MKme/ResQ/Aircraft Files  and Design Ref/Flight Controller Reference/f405-wing_3.jpg

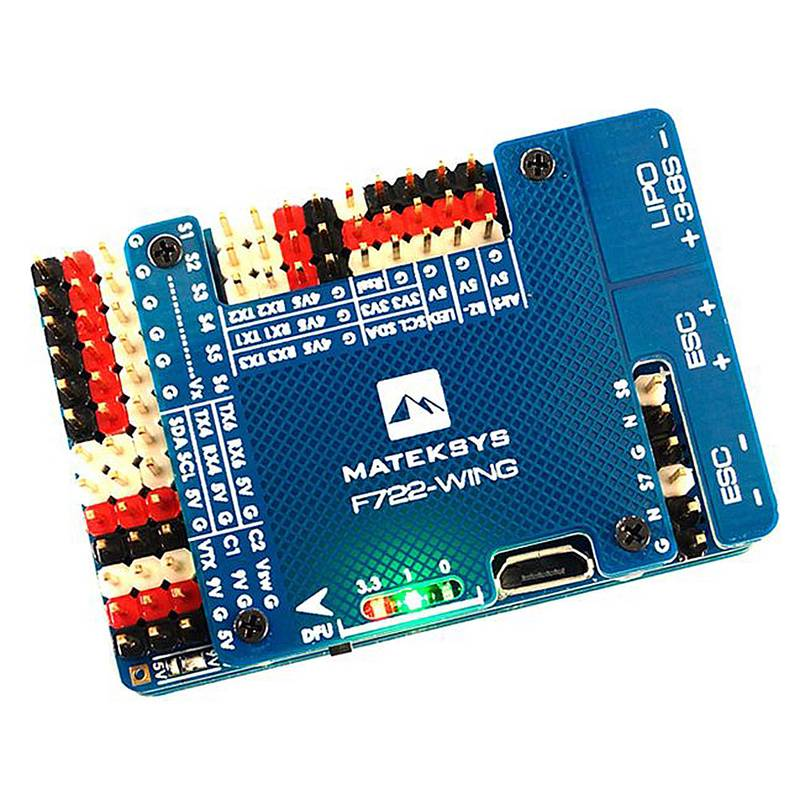
Aircraft Files and Design Ref/Flight Controller Reference/f405-wing_3.jpg
