MKme/ResQ/Code/Camera Module ESP32 Code/FTDI Connections for programming .PNG

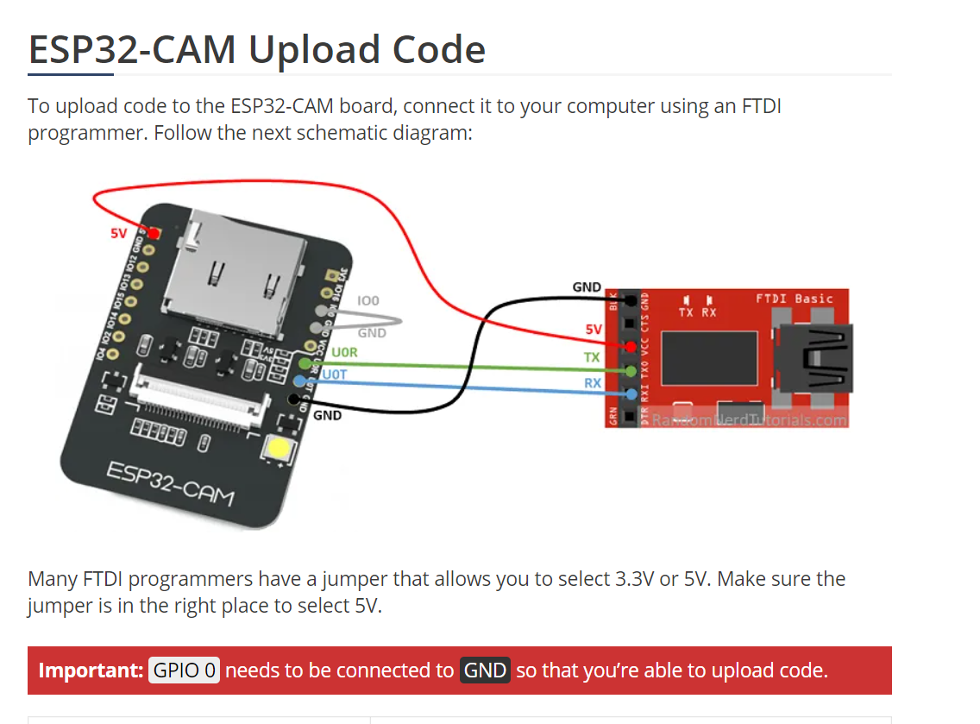
Code/Camera Module ESP32 Code/FTDI Connections for programming .PNG
