MKme/ResQ/Code/Camera Module ESP32 Code/Use the3se settings in Arduino IDE to program the board.png

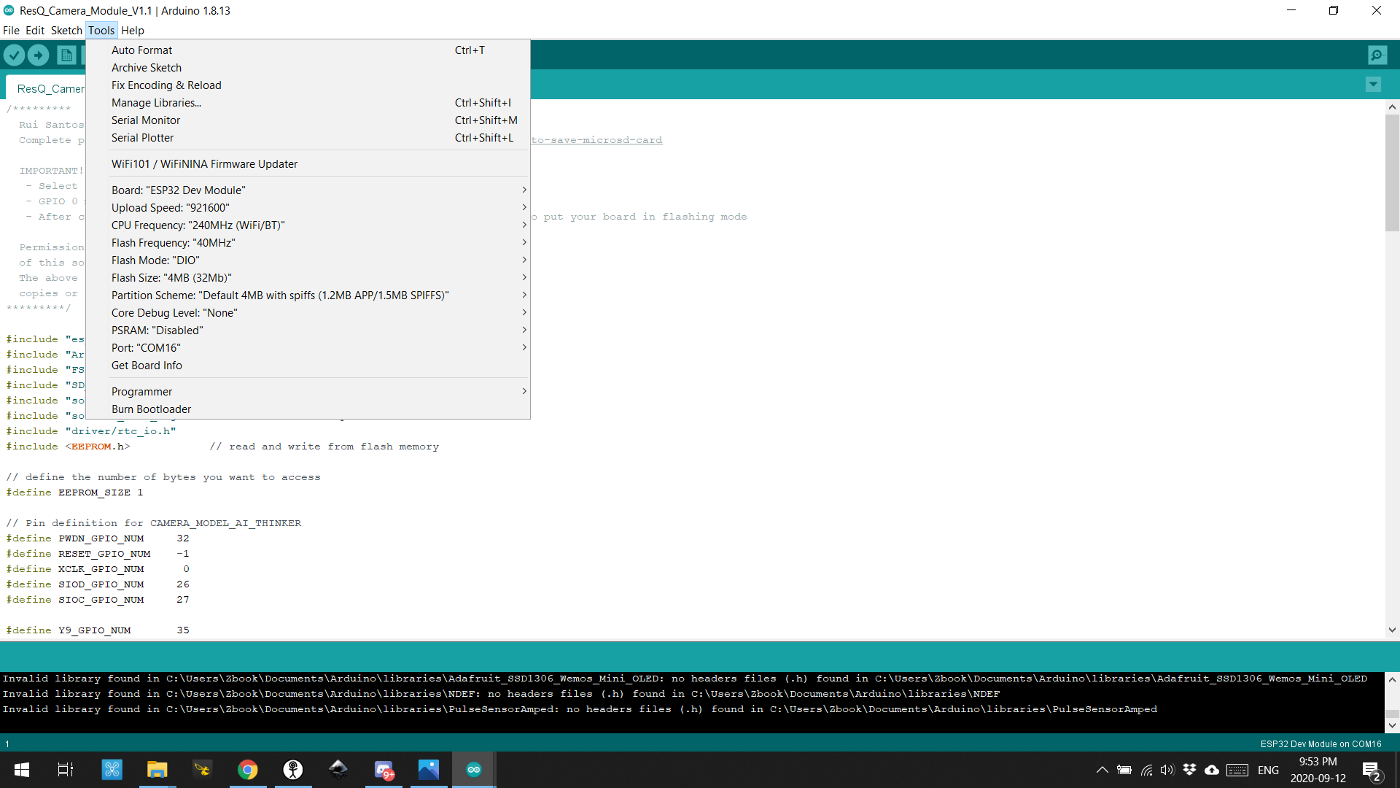
Code/Camera Module ESP32 Code/Use the3se settings in Arduino IDE to program the board.png
