MKme/ResQ/Enclsoure CAD Files/2D Models/Air unit case design  svg .PNG

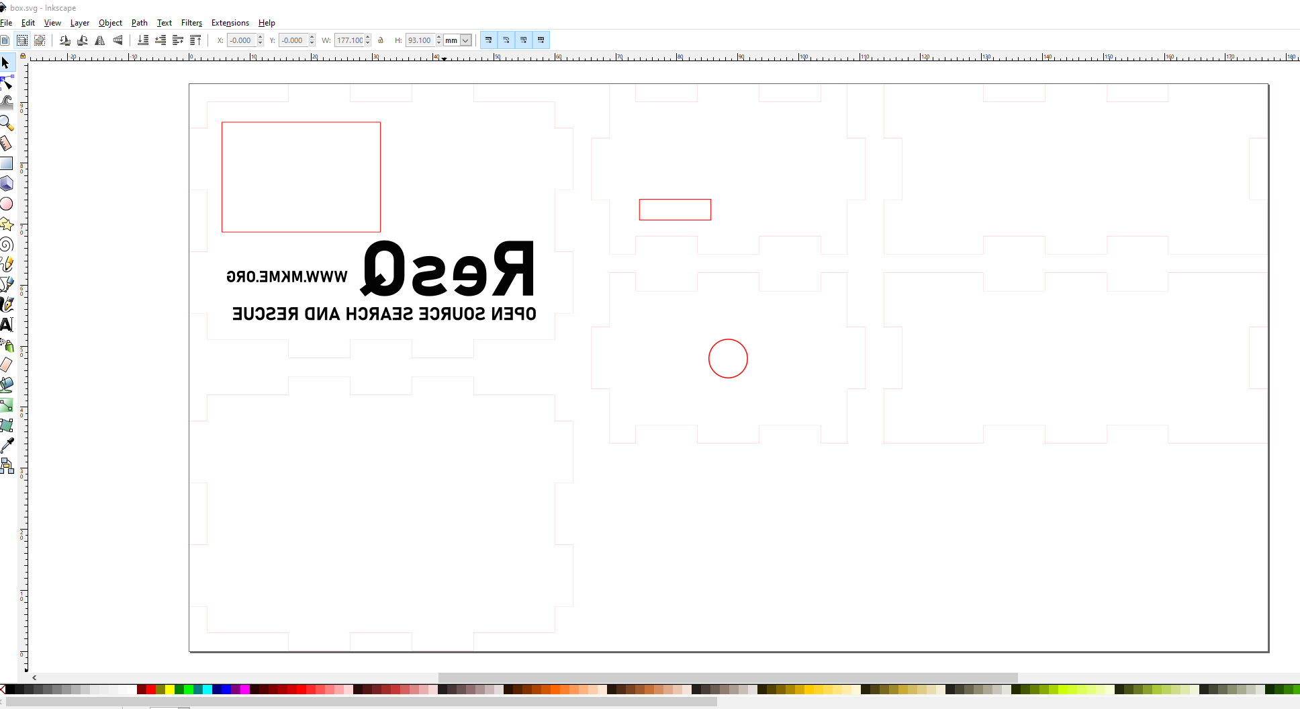
Enclsoure CAD Files/2D Models/Air unit case design svg .PNG
