MKme/ResQ/Enclsoure CAD Files/2D Models/Air Unit/V1.1 Air Unit Enclosure Laser Cut Version/Air unit dimensions.PNG

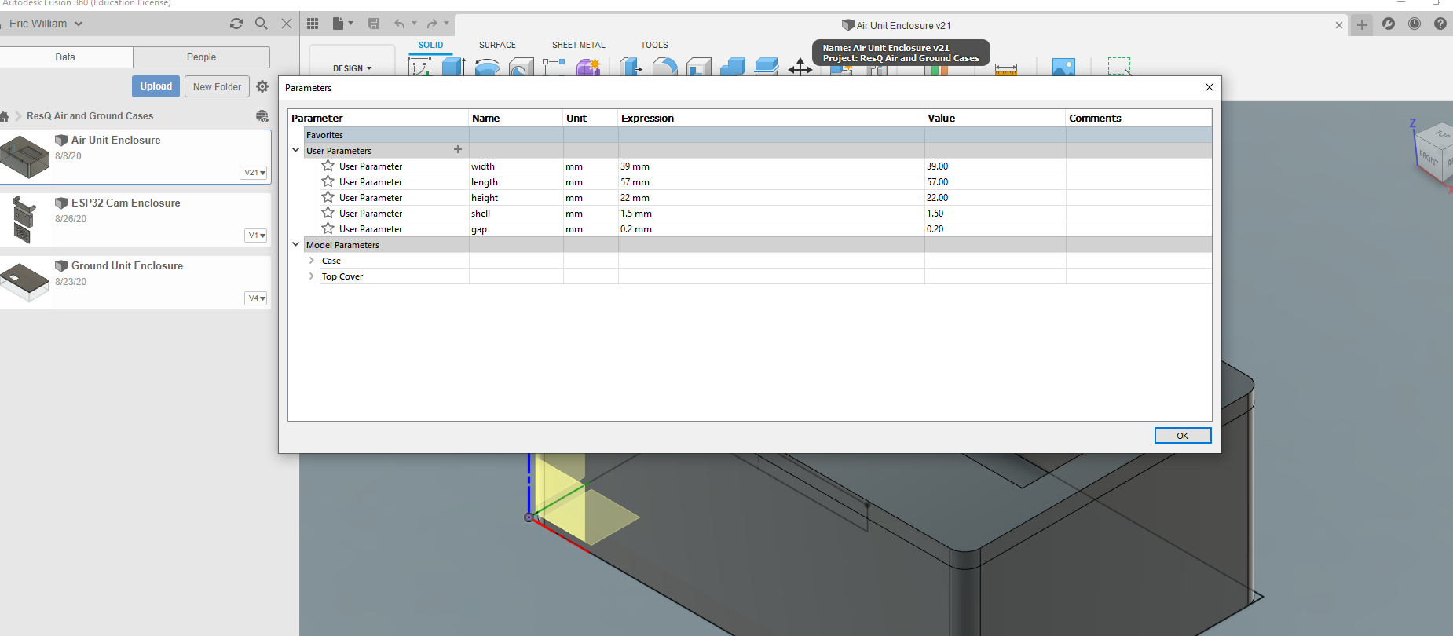
Enclsoure CAD Files/2D Models/Air Unit/V1.1 Air Unit Enclosure Laser Cut Version/Air unit dimensions.PNG
