MKme/ResQ/Enclsoure CAD Files/2D Models/Air Unit/V1.1 Air Unit Enclosure Laser Cut Version/OLED Cutout size that works .PNG

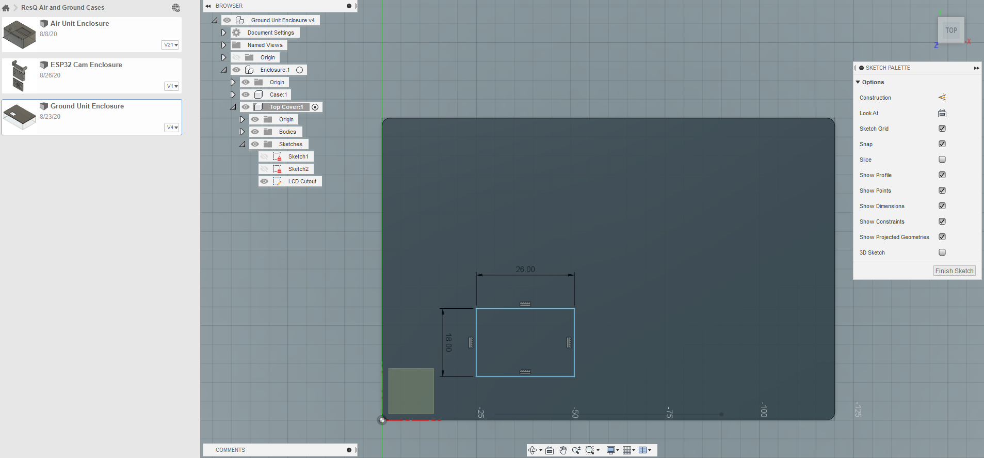
Enclsoure CAD Files/2D Models/Air Unit/V1.1 Air Unit Enclosure Laser Cut Version/OLED Cutout size that works .PNG
