MKme/ResQ/Enclsoure CAD Files/2D Models/Air Unit/V1.2 Air Unit Changed to outside dimensios plus 3mm/Dimesnions- Chjanged to INNER to add 3mm .PNG

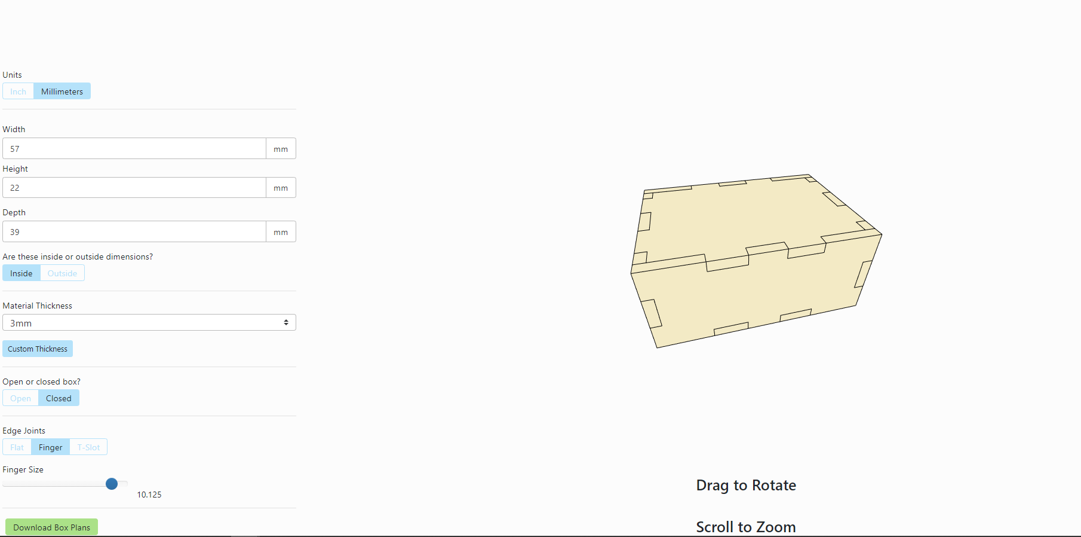
Enclsoure CAD Files/2D Models/Air Unit/V1.2 Air Unit Changed to outside dimensios plus 3mm/Dimesnions- Chjanged to INNER to add 3mm .PNG
