MKme/ResQ/Enclsoure CAD Files/2D Models/Air Unit/V1.3 Air Unit Sclaed back down to 1.1 plus 3mm height/Capture.PNG

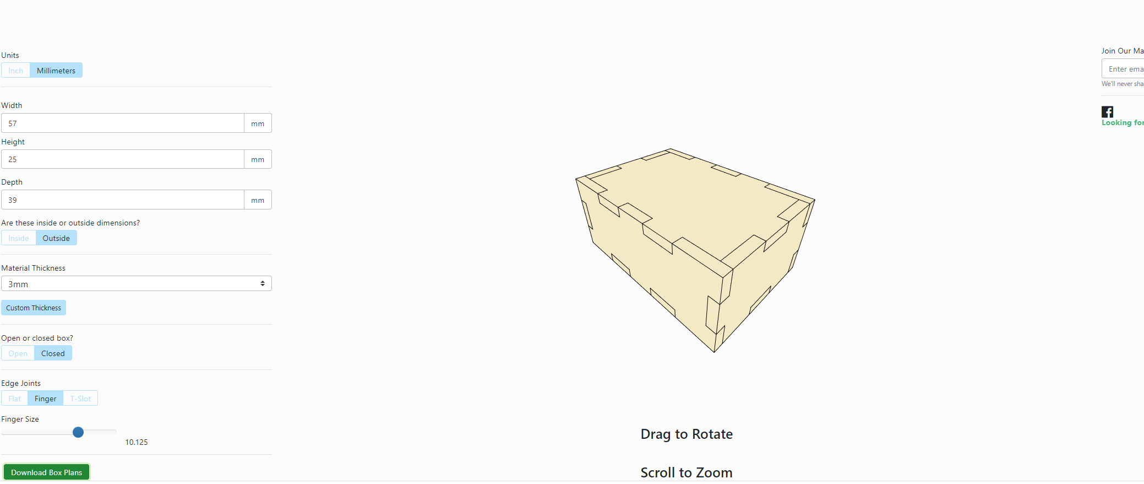
Enclsoure CAD Files/2D Models/Air Unit/V1.3 Air Unit Sclaed back down to 1.1 plus 3mm height/Capture.PNG
