MKme/ResQ/Enclsoure CAD Files/2D Models/Air Unit/V1.4 2mm Higher/Capture.PNG

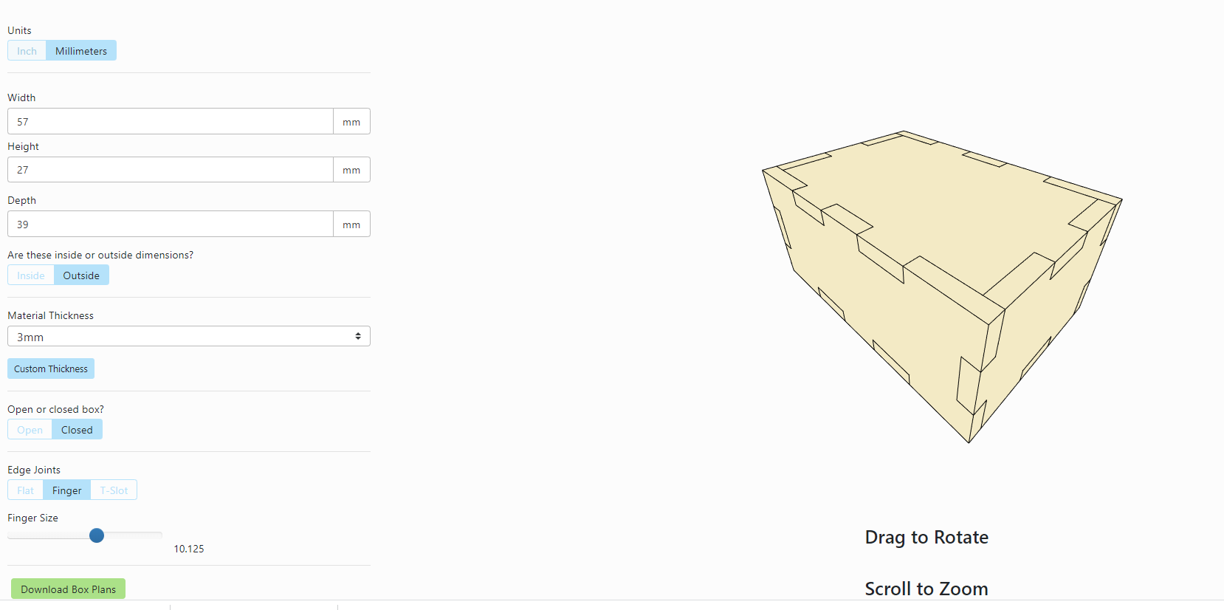
Enclsoure CAD Files/2D Models/Air Unit/V1.4 2mm Higher/Capture.PNG
