MKme/ResQ/Enclsoure CAD Files/2D Models/Ground Enclosure design V1.1 .PNG

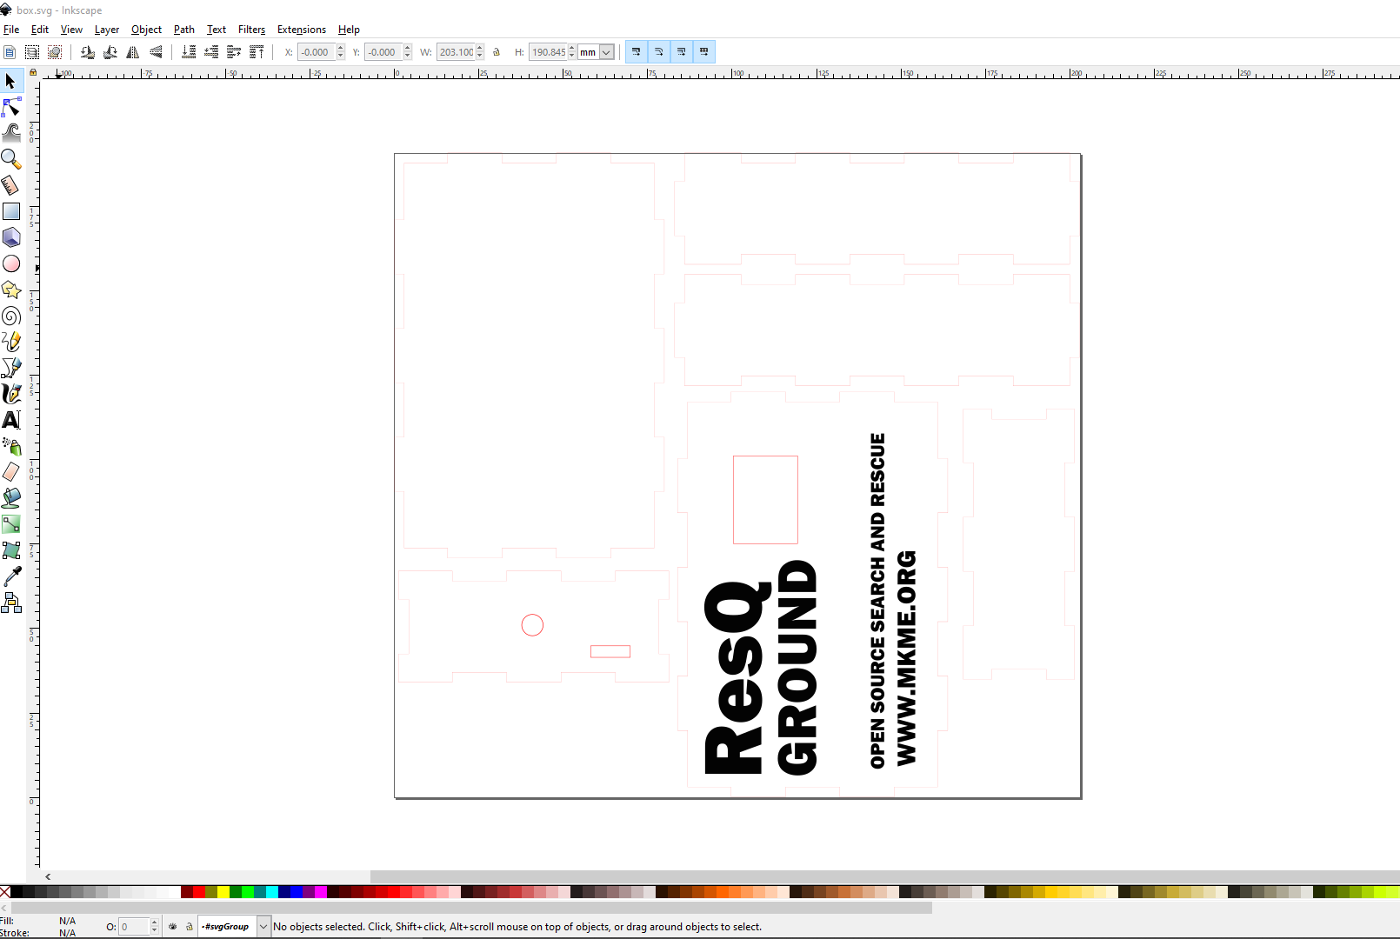
Enclsoure CAD Files/2D Models/Ground Enclosure design V1.1 .PNG
