MKme/ResQ/Enclsoure CAD Files/3D Models/Air Unit Enclosure/V1.4 Fusion 360/CaseBottom .PNG

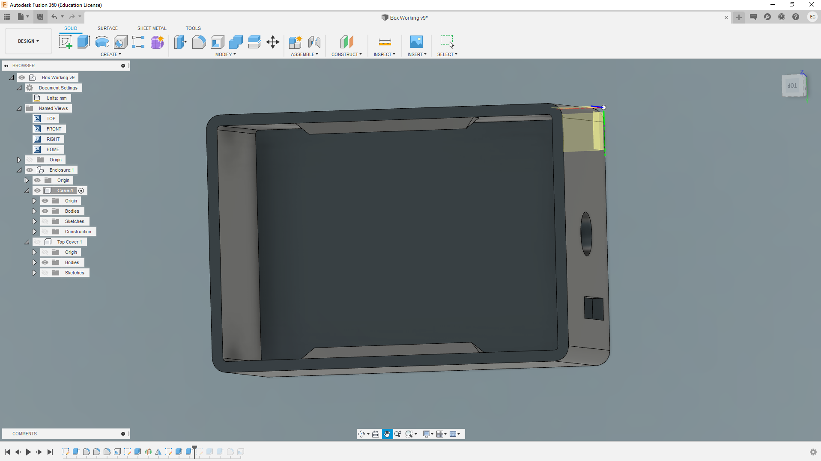
Enclsoure CAD Files/3D Models/Air Unit Enclosure/V1.4 Fusion 360/CaseBottom .PNG
