MKme/ResQ/Enclsoure CAD Files/ResQ Sentry Enclosure/2D/dimensions.PNG

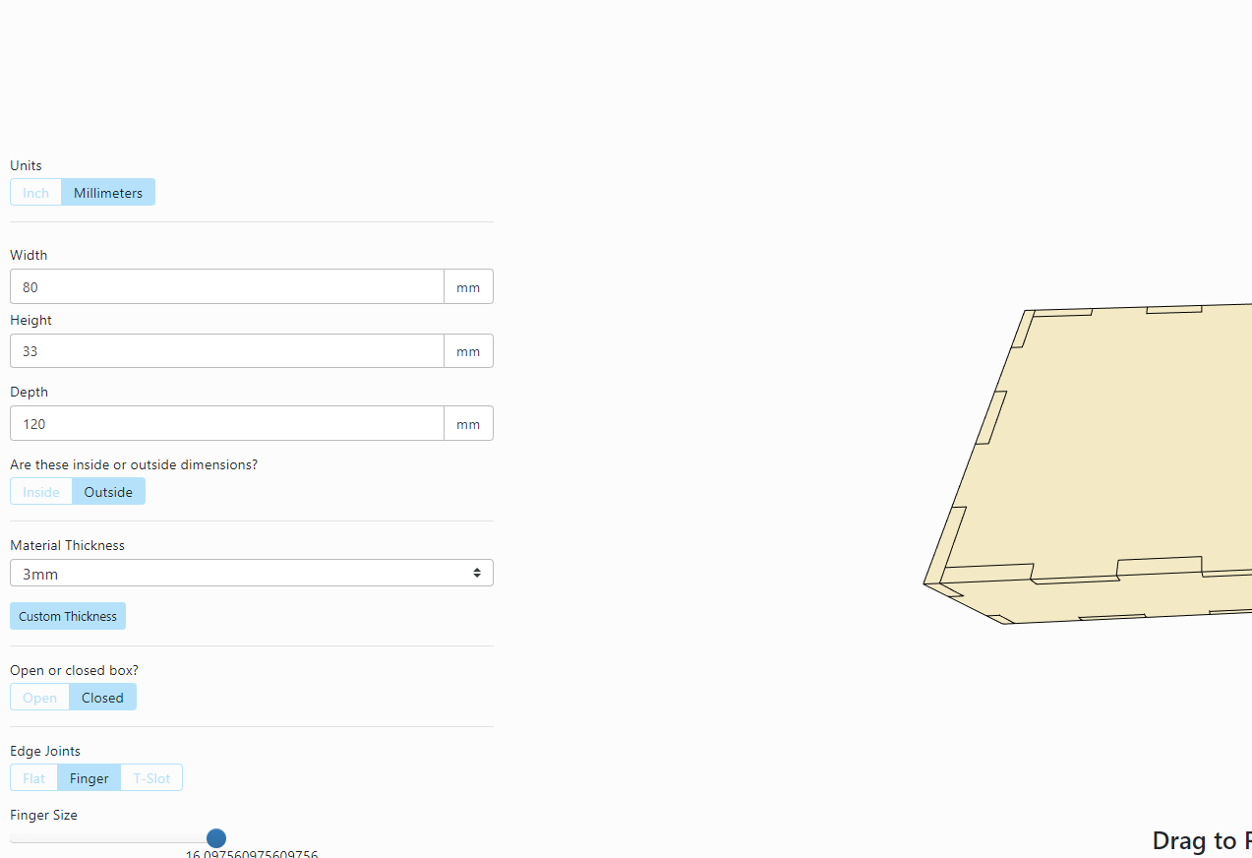
Enclsoure CAD Files/ResQ Sentry Enclosure/2D/dimensions.PNG
