MKme/ResQ/PCB/V1.1 PCB Files and Gerbers/ResQ PCB V1.1 Routing PCB 2  _schem.png

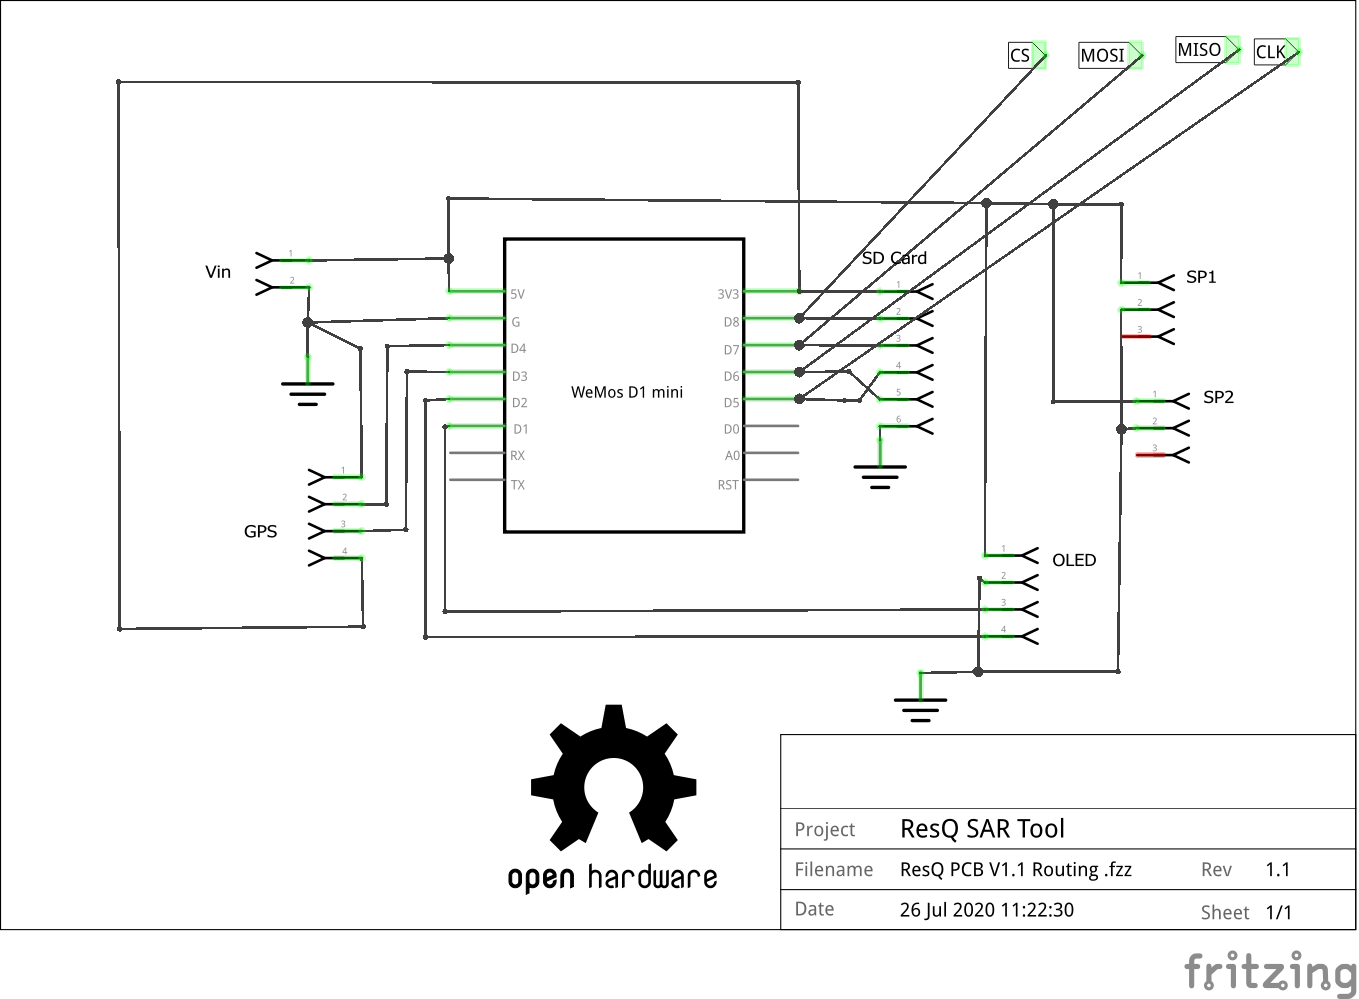
PCB/V1.1 PCB Files and Gerbers/ResQ PCB V1.1 Routing PCB 2 _schem.png
