MKme/ResQ/PCB/V1.1 PCB Files and Gerbers/ResQ V1.1PCB Powers and Grounds png.png

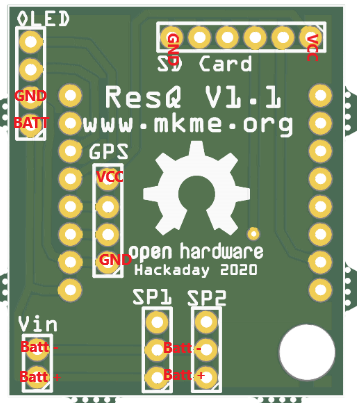
PCB/V1.1 PCB Files and Gerbers/ResQ V1.1PCB Powers and Grounds png.png
