MKme/ResQ/PCB/V2.1 KiCad Version/Board Connections Layout .png

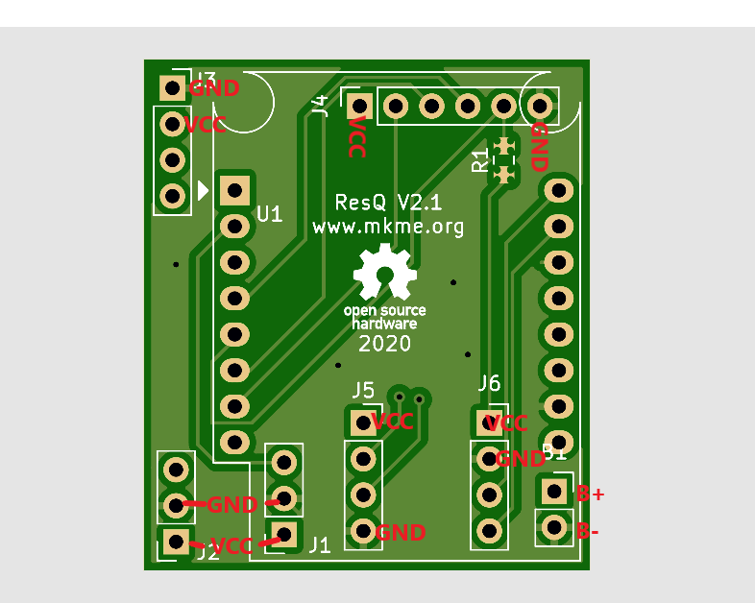
PCB/V2.1 KiCad Version/Board Connections Layout .png
