MKme/ResQ/PCB/V2.1 KiCad Version/Bottom .PNG

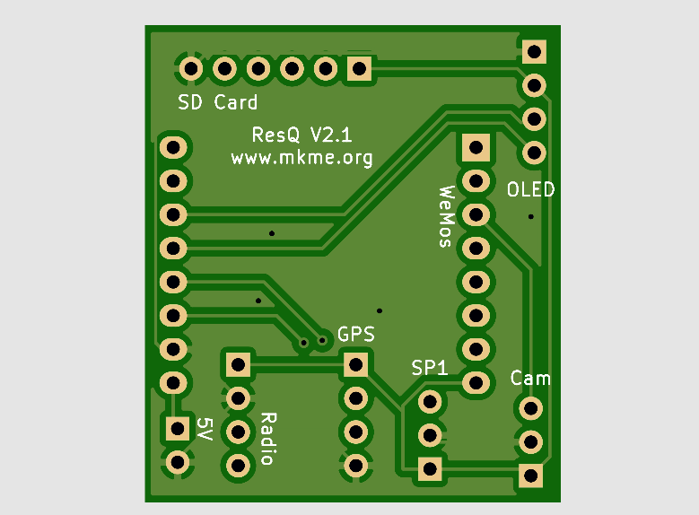
PCB/V2.1 KiCad Version/Bottom .PNG
