MKme/ResQ/PCB/V2.1 KiCad Version/ResQ KiCad Version/oled.jpg

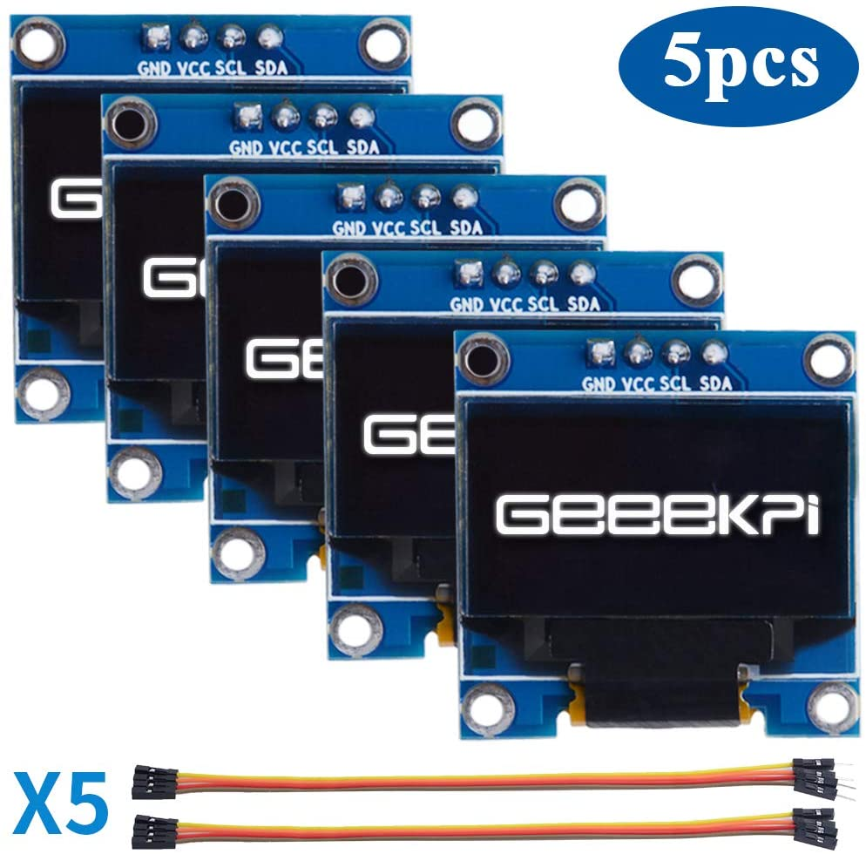
PCB/V2.1 KiCad Version/ResQ KiCad Version/oled.jpg
