MKme/ResQ/Photos/4CA8209F-AA27-4E30-B530-D4E17EBE052C.jpg

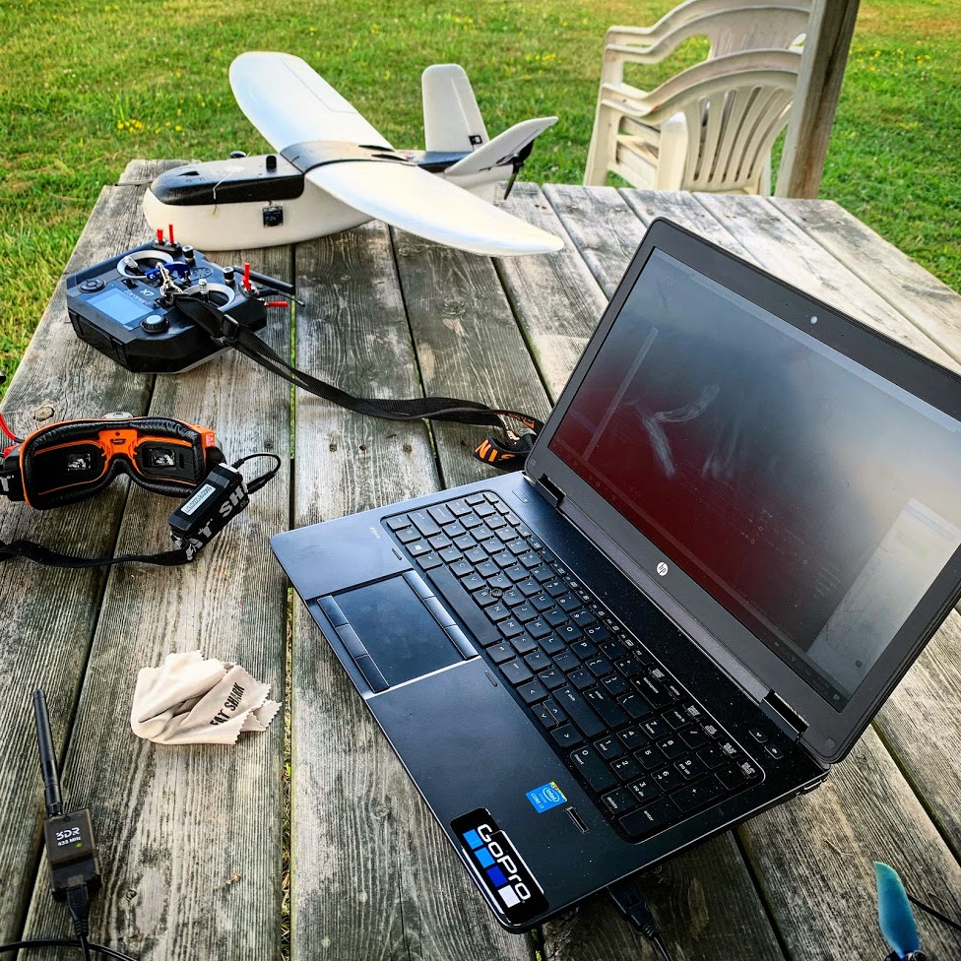
Photos/4CA8209F-AA27-4E30-B530-D4E17EBE052C.jpg
