MKme/ResQ/Photos/Air Unit Case .PNG

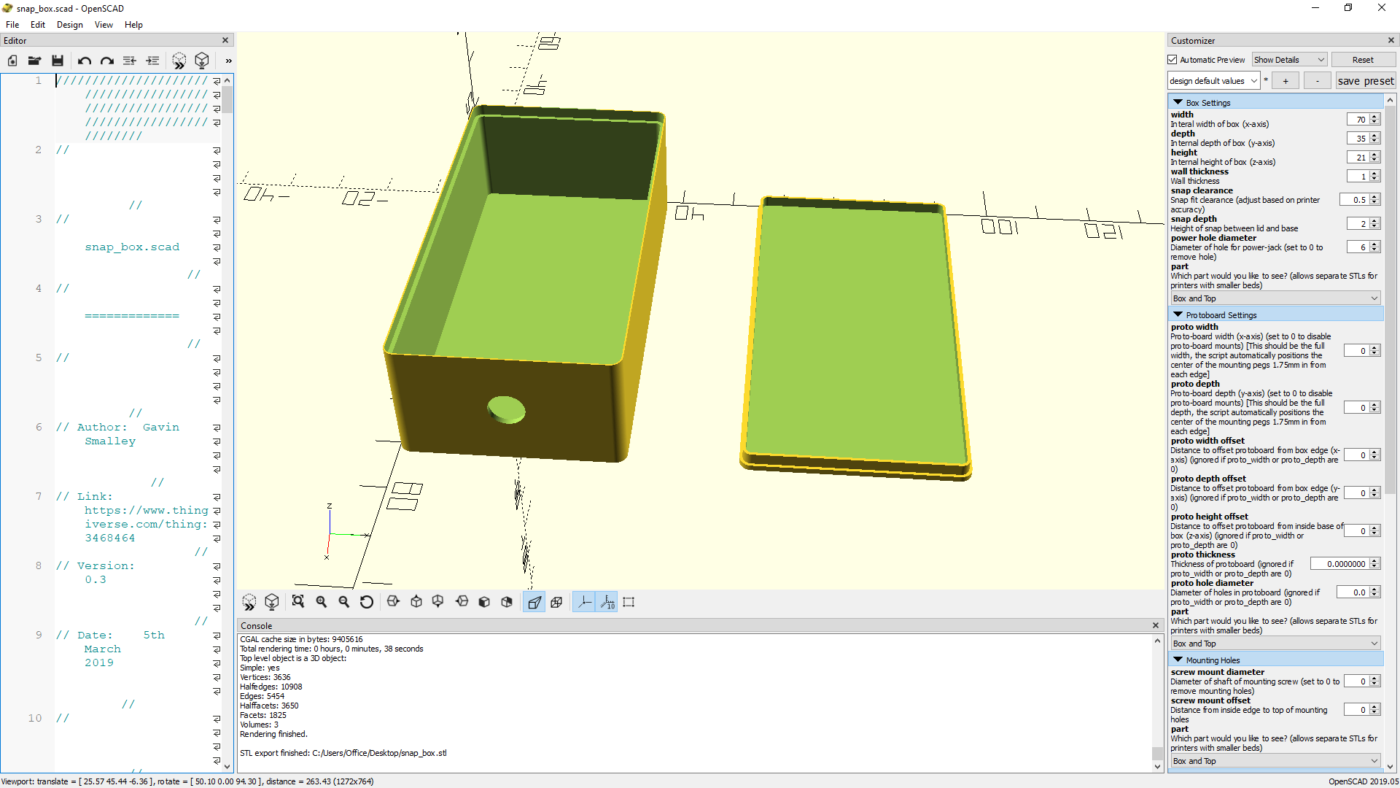
Photos/Air Unit Case .PNG
