MKme/ResQ/Photos/Airunitcura.PNG

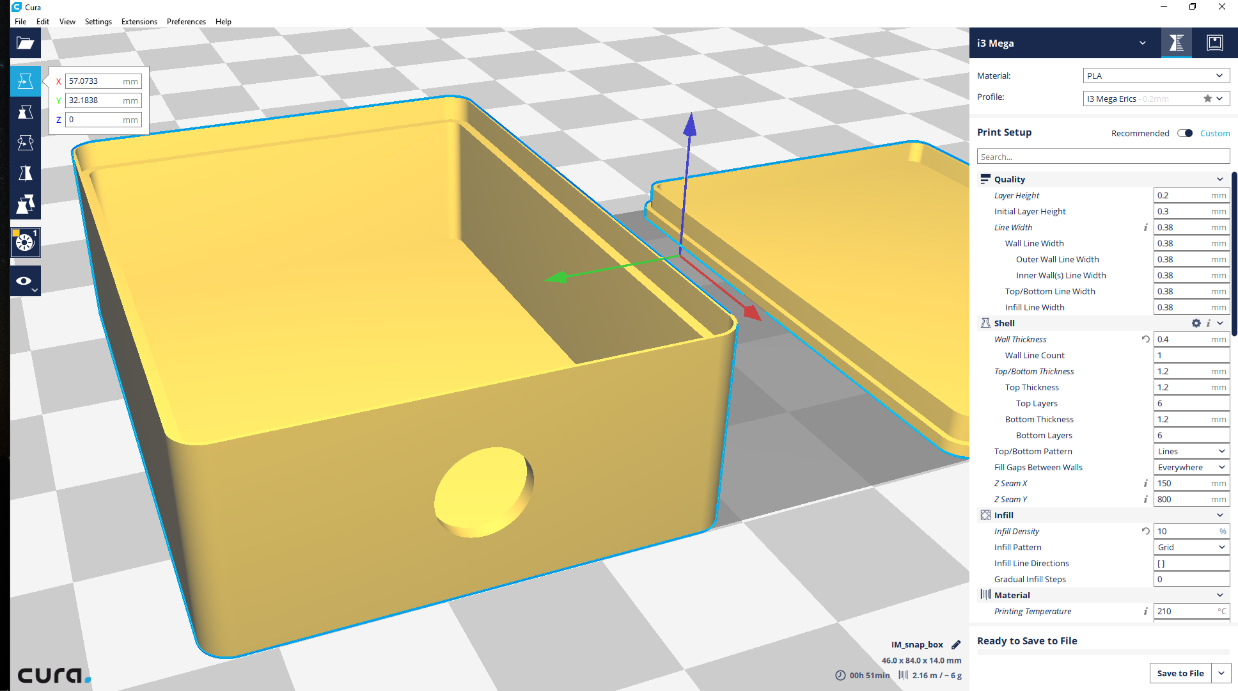
Photos/Airunitcura.PNG
