MKme/ResQ/Photos/Airunitopenscad.PNG

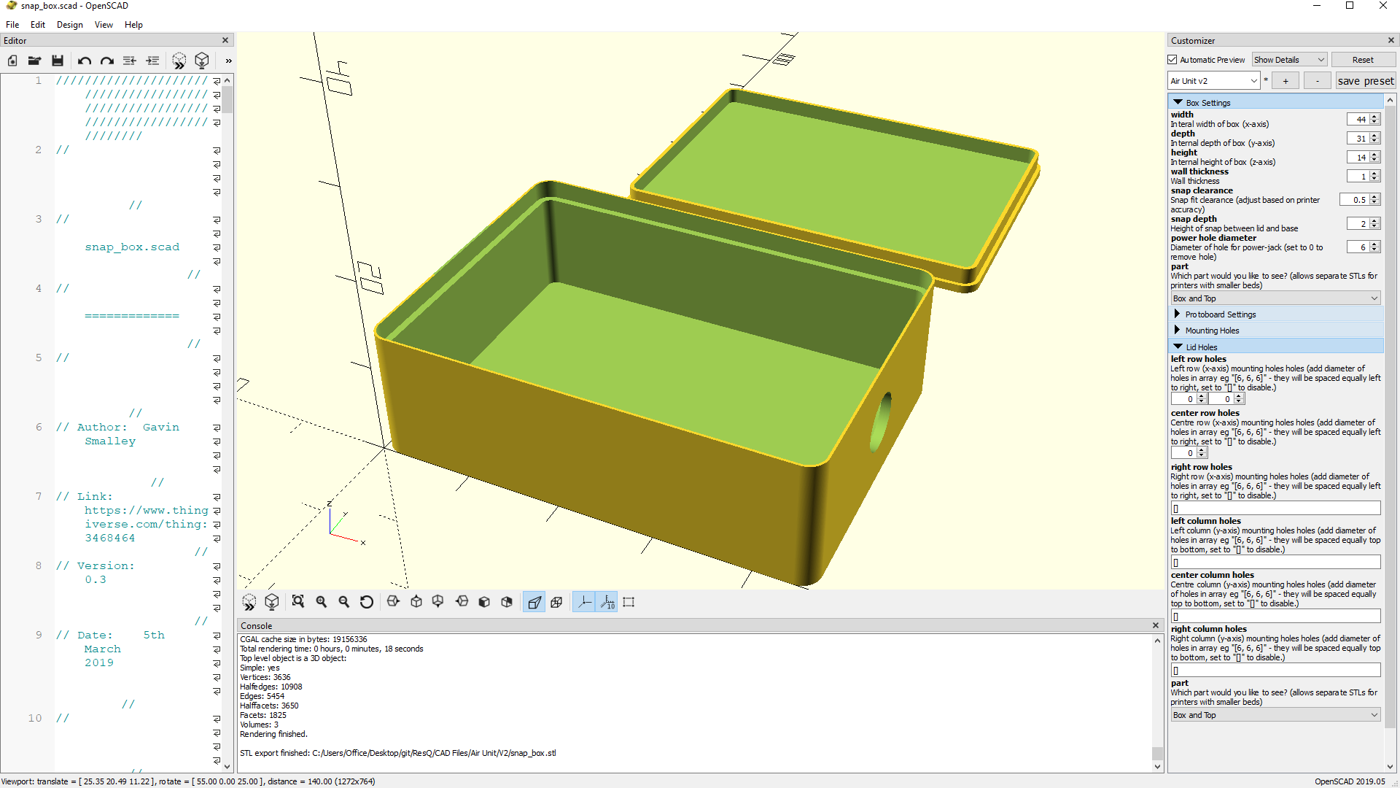
Photos/Airunitopenscad.PNG
