MKme/ResQ/Photos/Bluetooth/HC-05-Bluetooth-Module.jpg

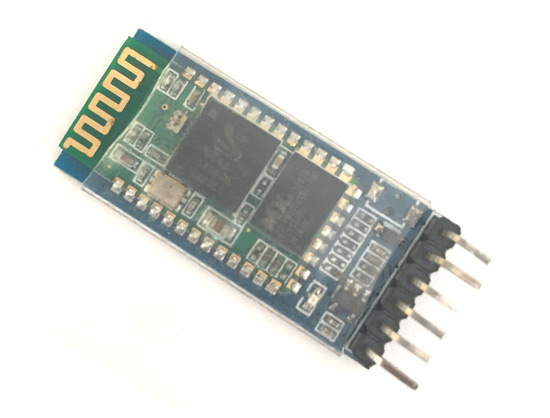
Photos/Bluetooth/HC-05-Bluetooth-Module.jpg
