MKme/ResQ/Photos/Bluetooth/IMG_1080.jpg

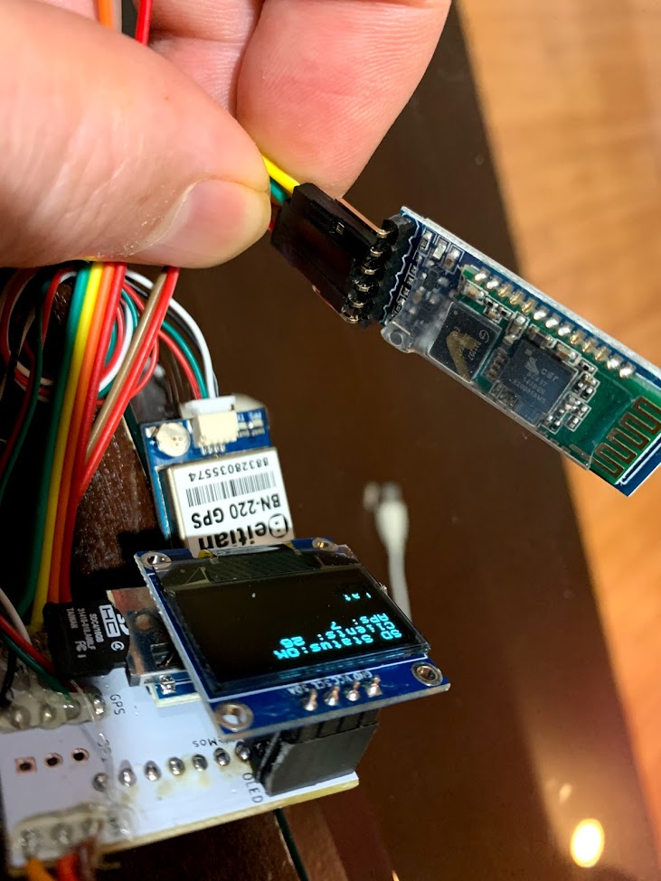
Photos/Bluetooth/IMG_1080.jpg
