MKme/ResQ/Photos/Bluetooth/IMG_1085.jpg

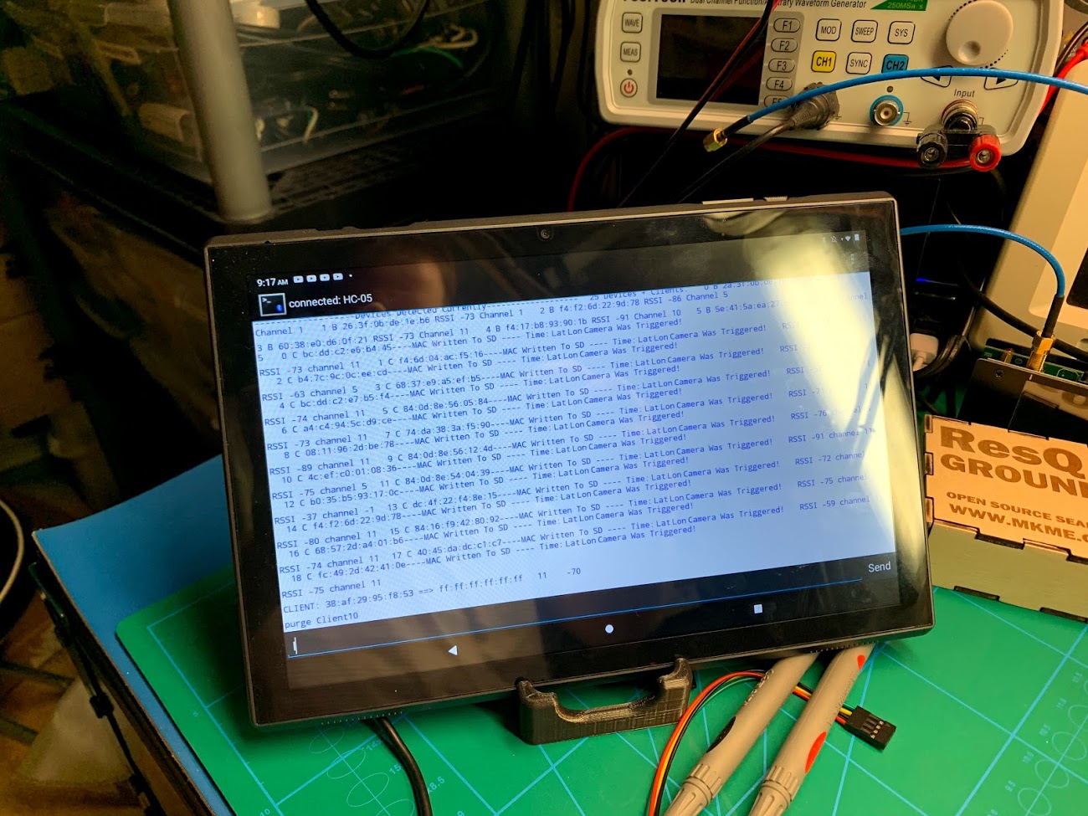
Photos/Bluetooth/IMG_1085.jpg
