MKme/ResQ/Photos/Bluetooth/IMG_1095.jpg

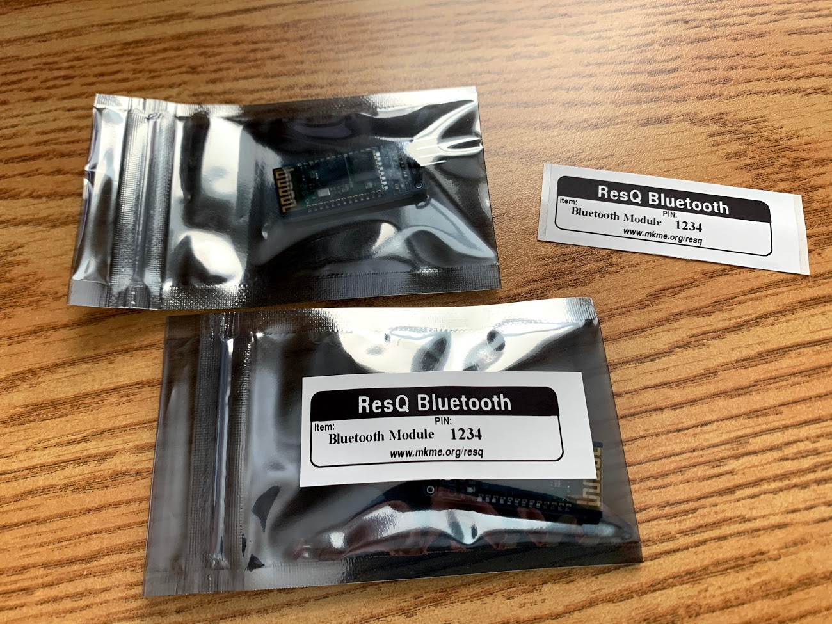
Photos/Bluetooth/IMG_1095.jpg
