MKme/ResQ/Photos/Bluetooth/RadioConn.jpg

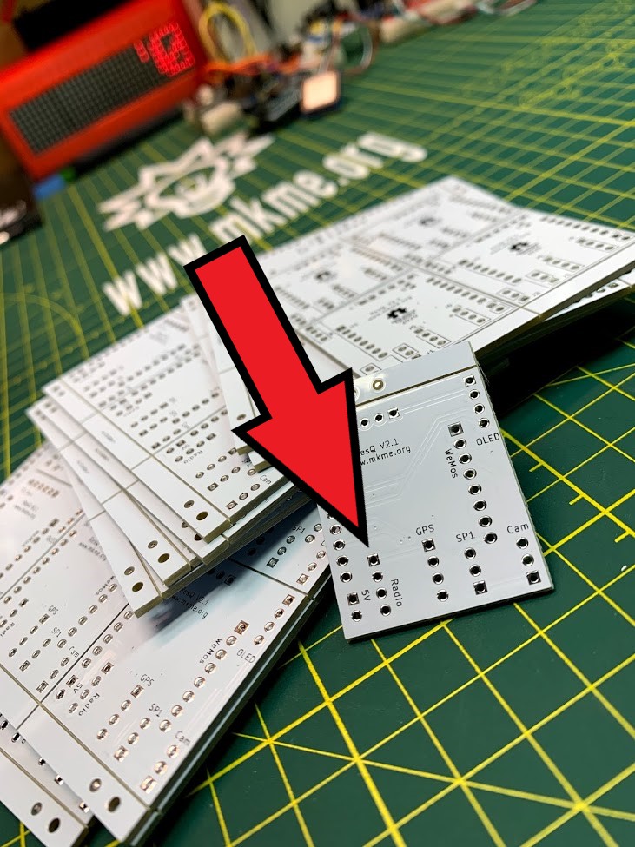
Photos/Bluetooth/RadioConn.jpg
