MKme/ResQ/Photos/C24DCCB7-45C5-4DEE-B202-2B8DF717EF2D.jpg

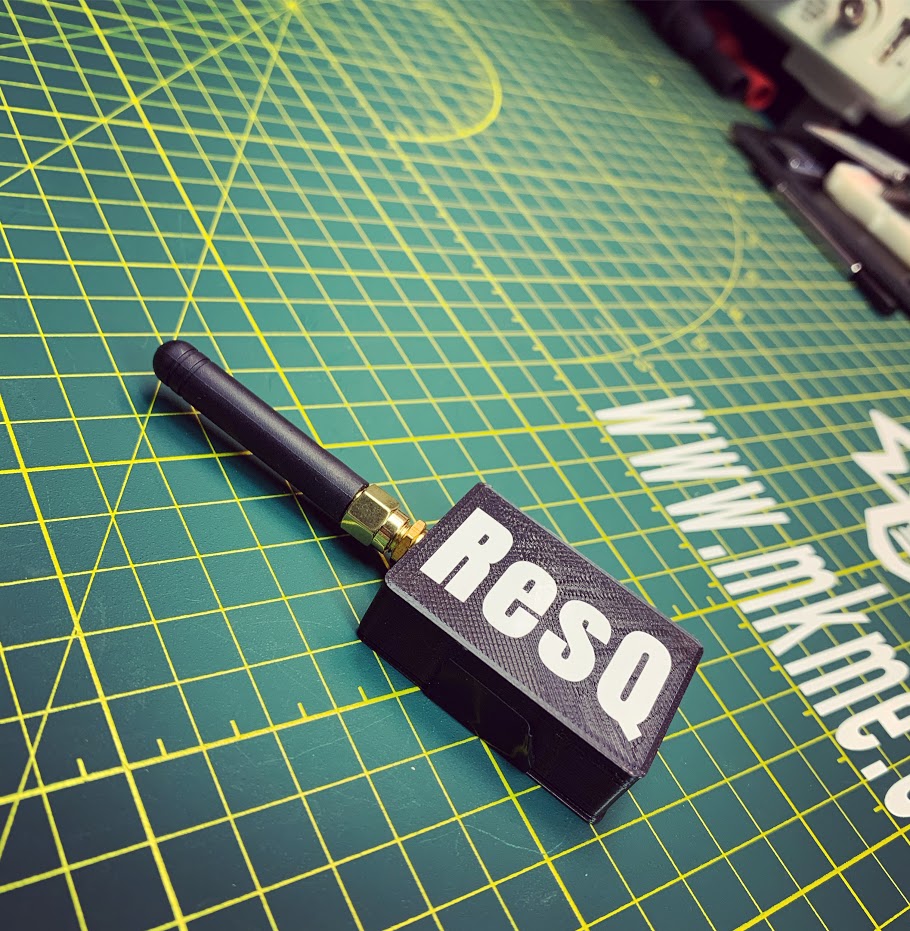
Photos/C24DCCB7-45C5-4DEE-B202-2B8DF717EF2D.jpg
