MKme/ResQ/Photos/Clients at Beach. PNG.PNG

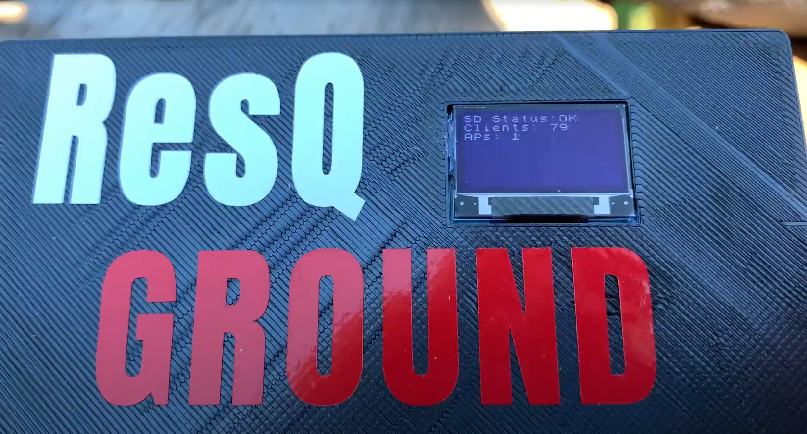
Photos/Clients at Beach. PNG.PNG
