MKme/ResQ/Photos/DA7A53AD-6385-4ABC-AD7B-FEE3AB23B0AE.jpg

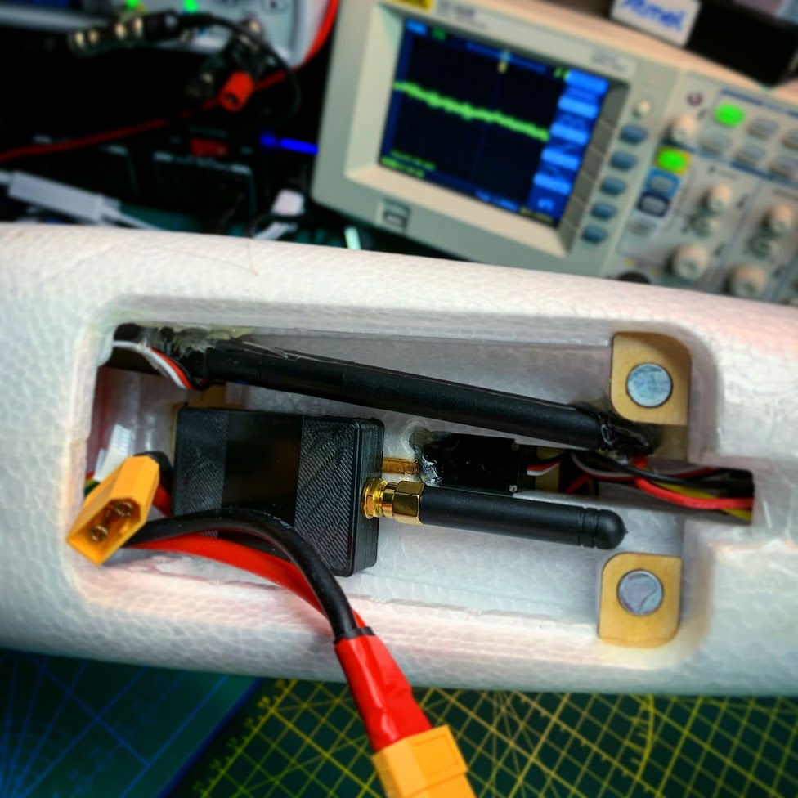
Photos/DA7A53AD-6385-4ABC-AD7B-FEE3AB23B0AE.jpg
