MKme/ResQ/Photos/datalog txt screenshot .PNG

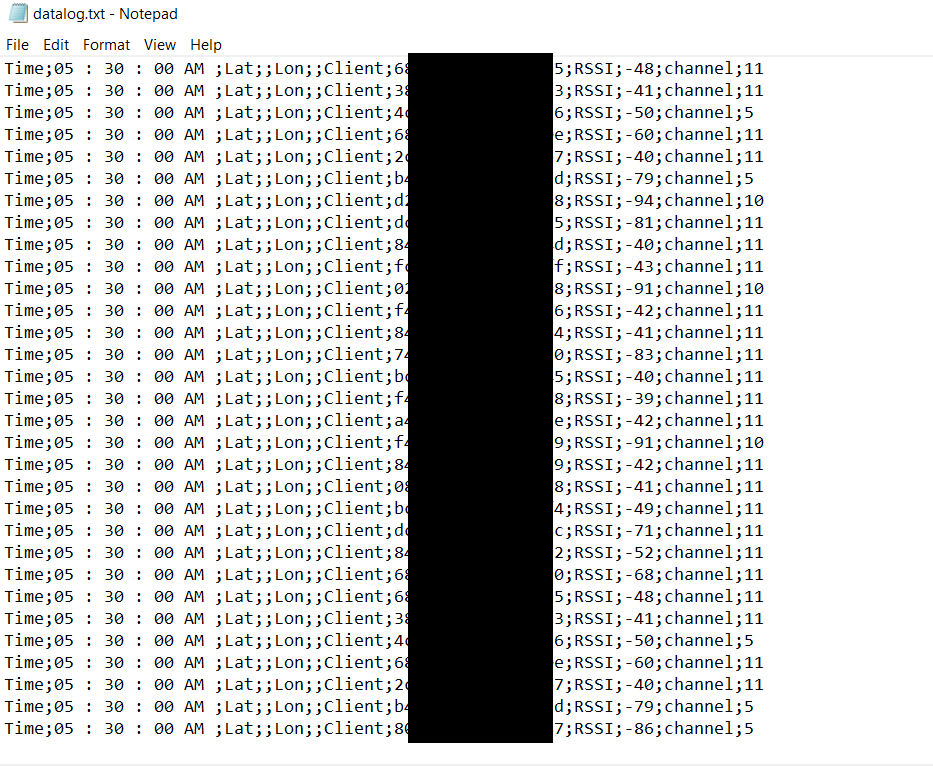
Photos/datalog txt screenshot .PNG
