MKme/ResQ/Photos/Edit.PNG

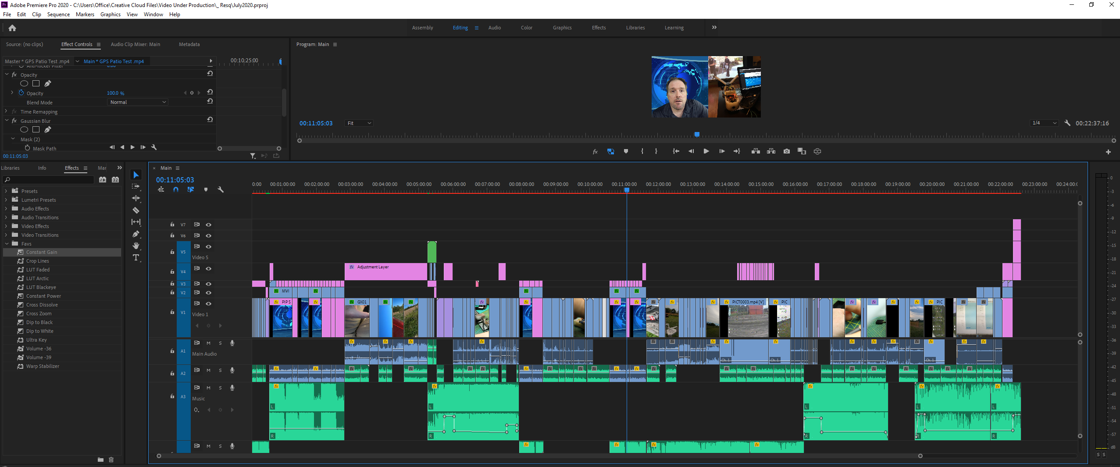
Photos/Edit.PNG
