MKme/ResQ/Photos/Fall2019 proto.jpg

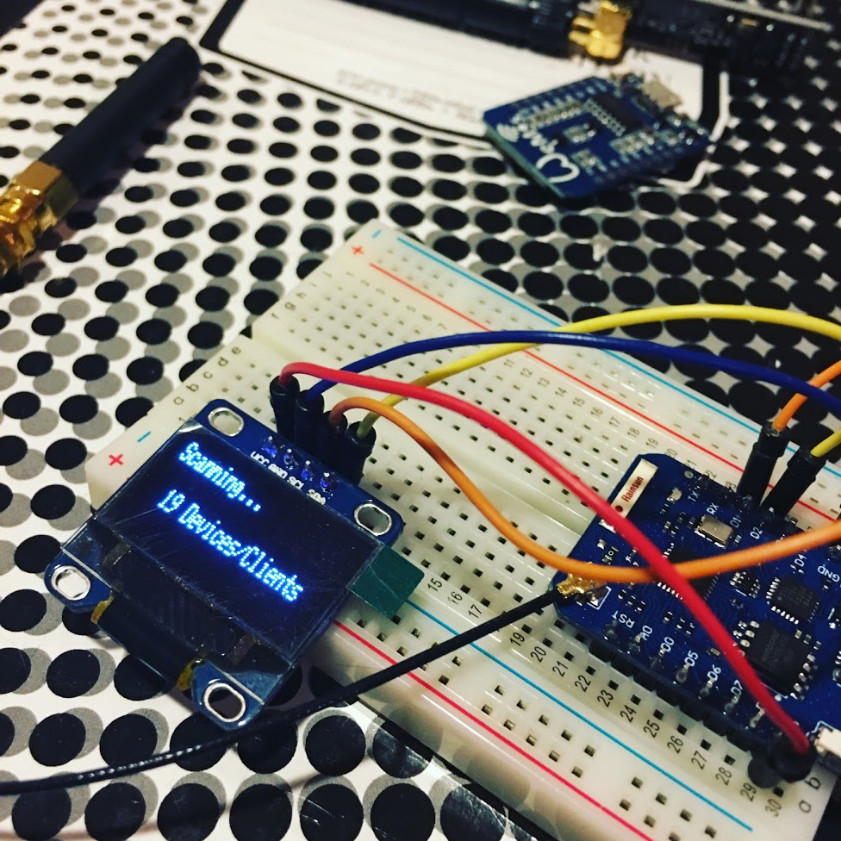
Photos/Fall2019 proto.jpg
