MKme/ResQ/Photos/FritzingBreadboard .PNG

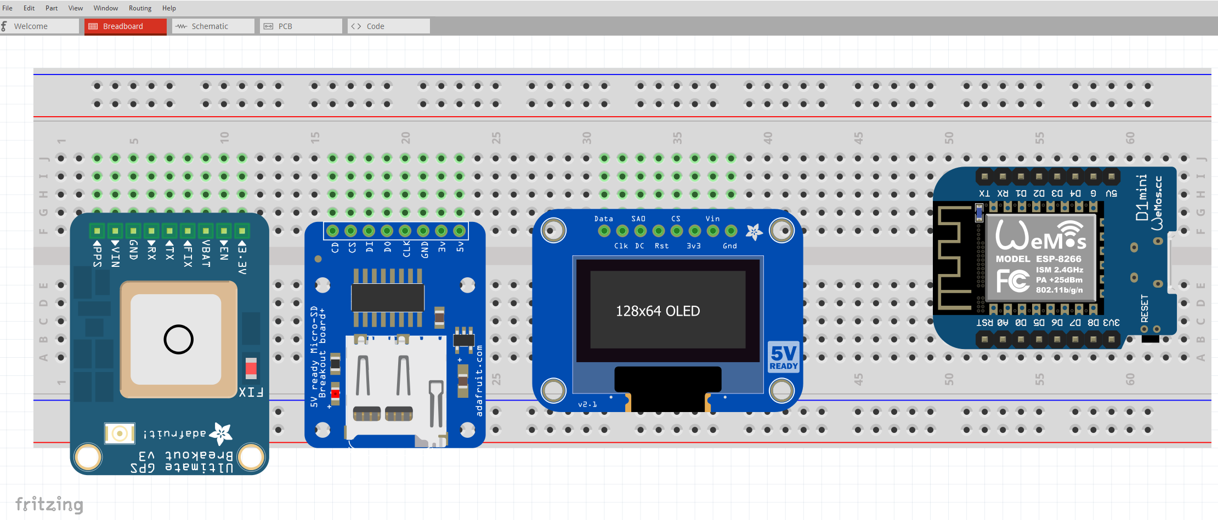
Photos/FritzingBreadboard .PNG
