MKme/ResQ/Photos/GPS _Code_Added .PNG

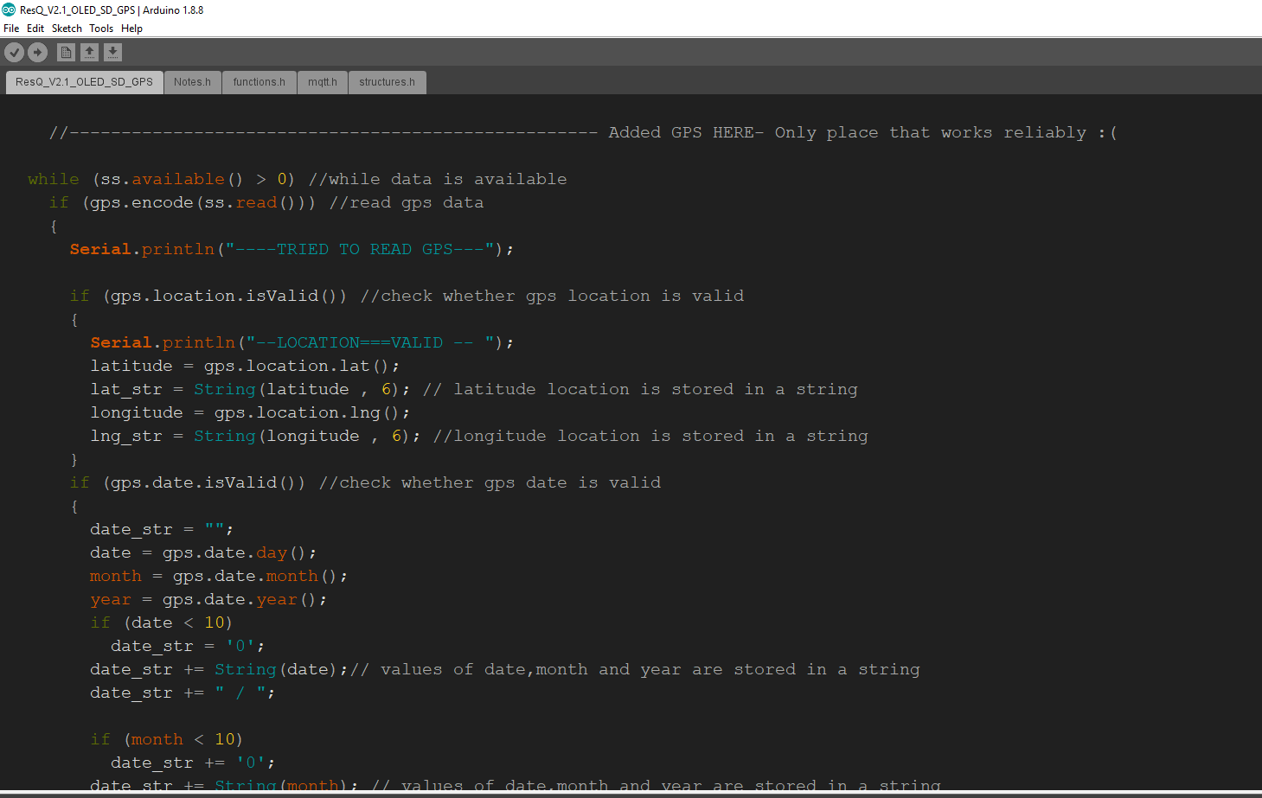
Photos/GPS _Code_Added .PNG
