MKme/ResQ/Photos/GPS_Integration_WORKS.jpg

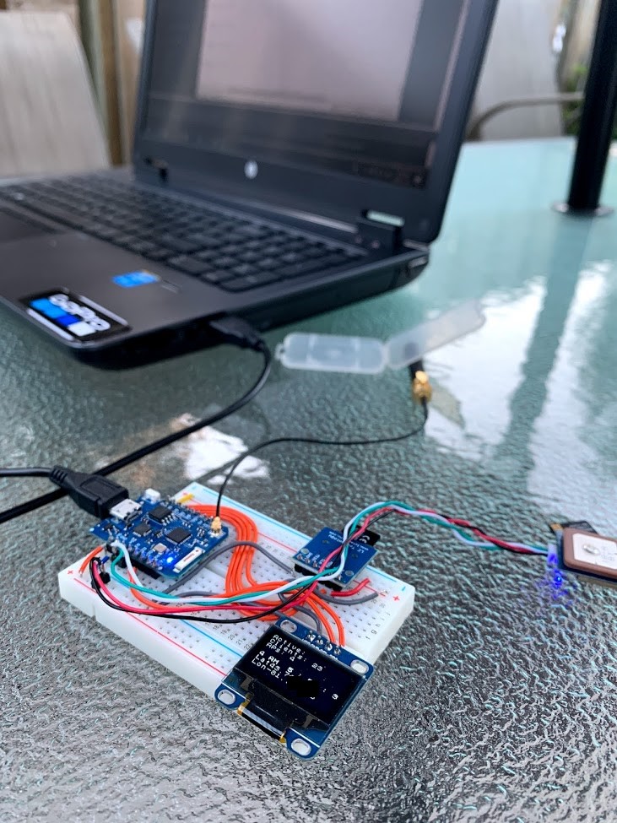
Photos/GPS_Integration_WORKS.jpg
