MKme/ResQ/Photos/Ground Unit CAD .PNG

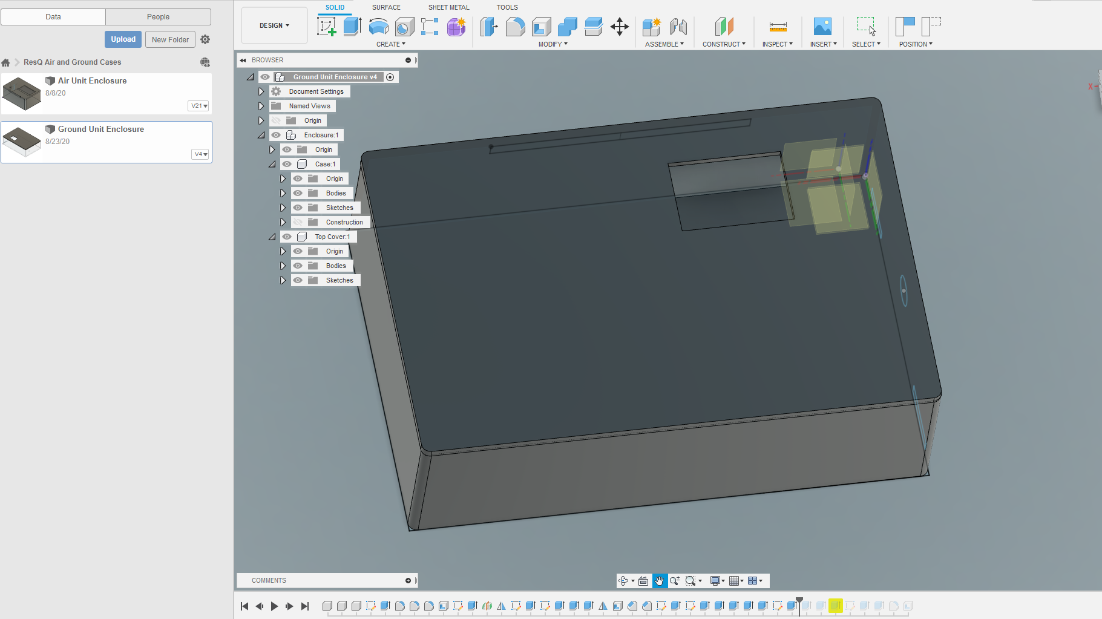
Photos/Ground Unit CAD .PNG
