MKme/ResQ/Photos/Ground Unit Enclosure CURA .PNG

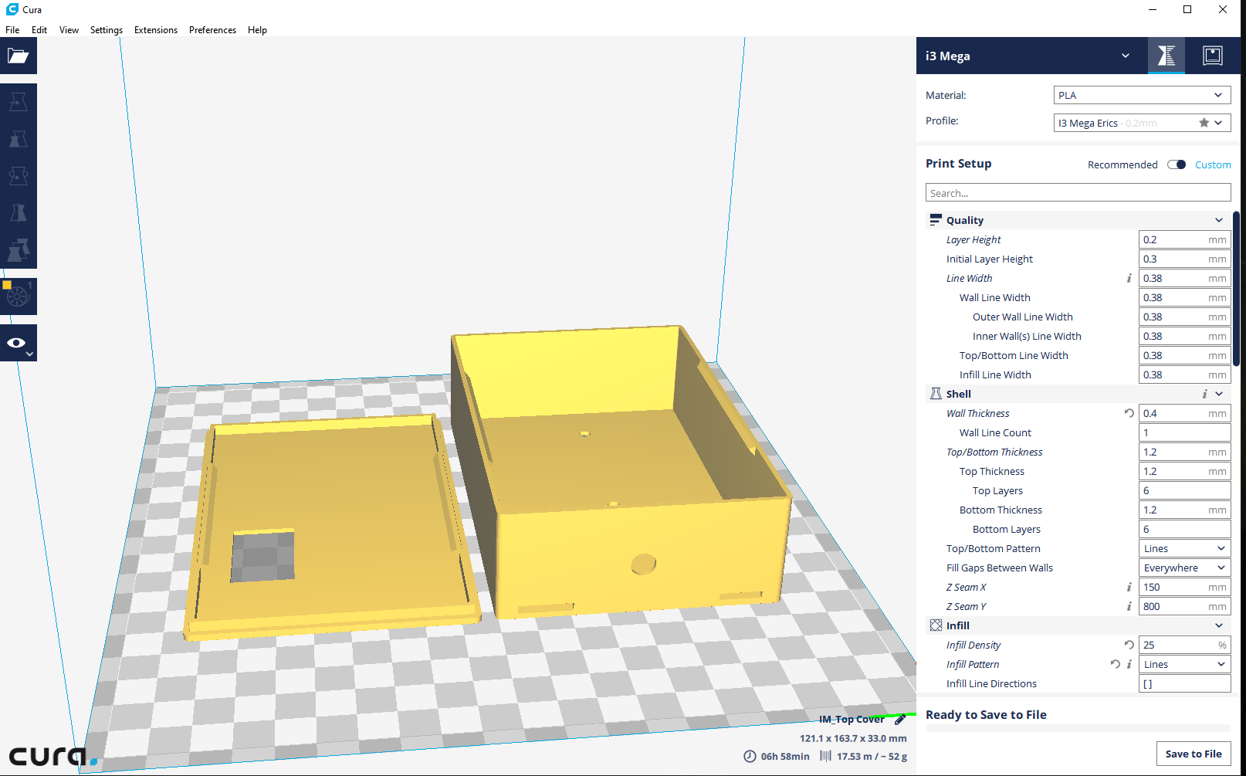
Photos/Ground Unit Enclosure CURA .PNG
