MKme/ResQ/Photos/IMG_0216.jpg

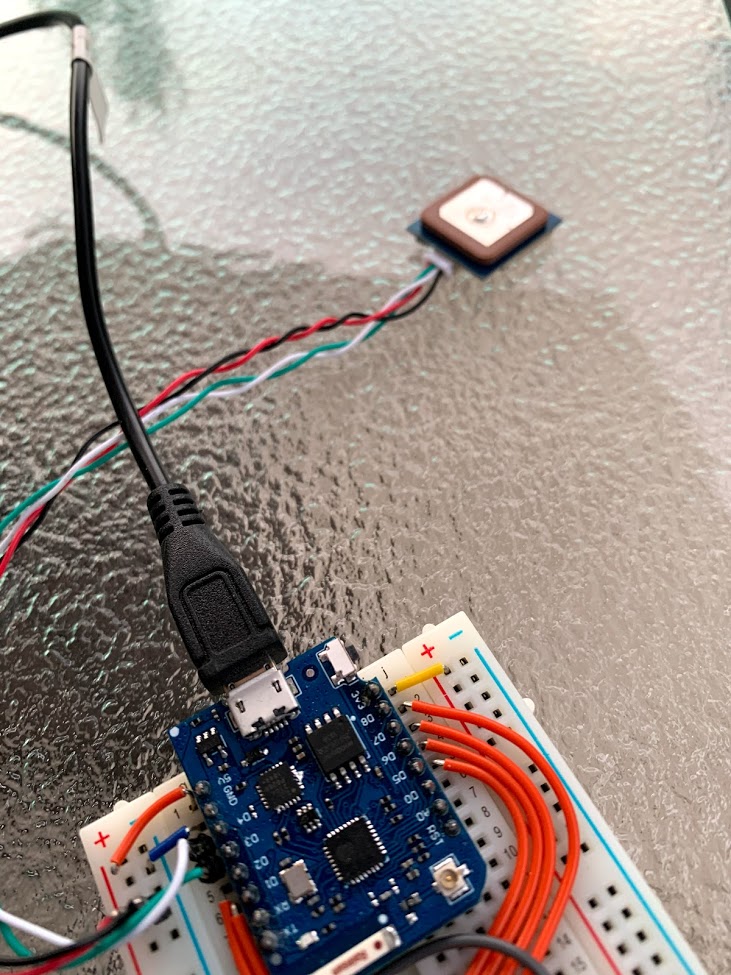
Photos/IMG_0216.jpg
