MKme/ResQ/Photos/IMG_0254.jpg

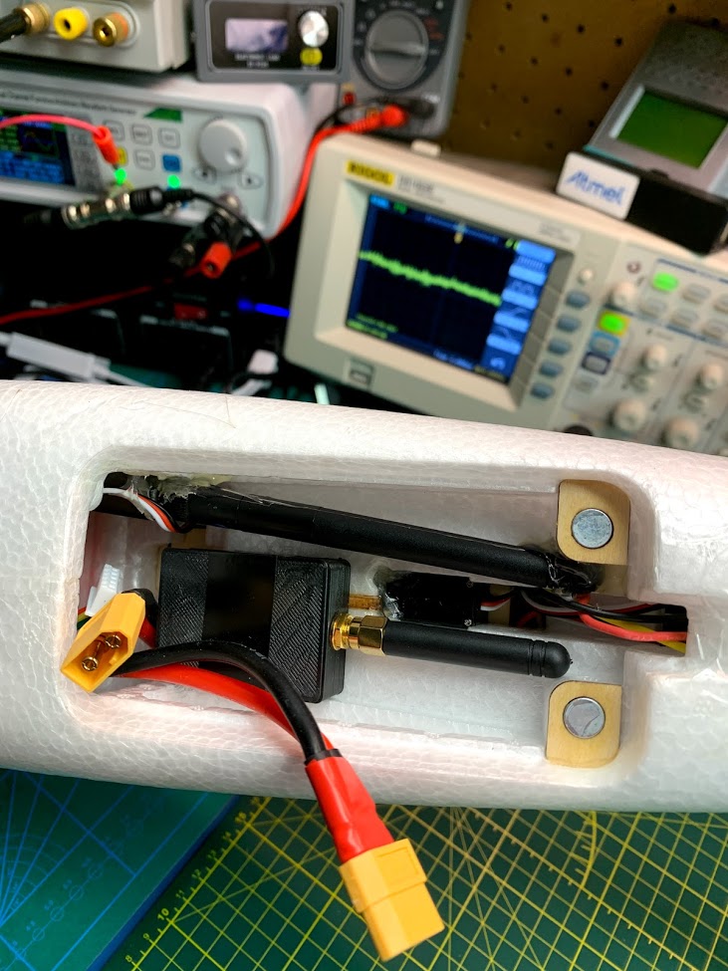
Photos/IMG_0254.jpg
