MKme/ResQ/Photos/IMG_0349.jpg

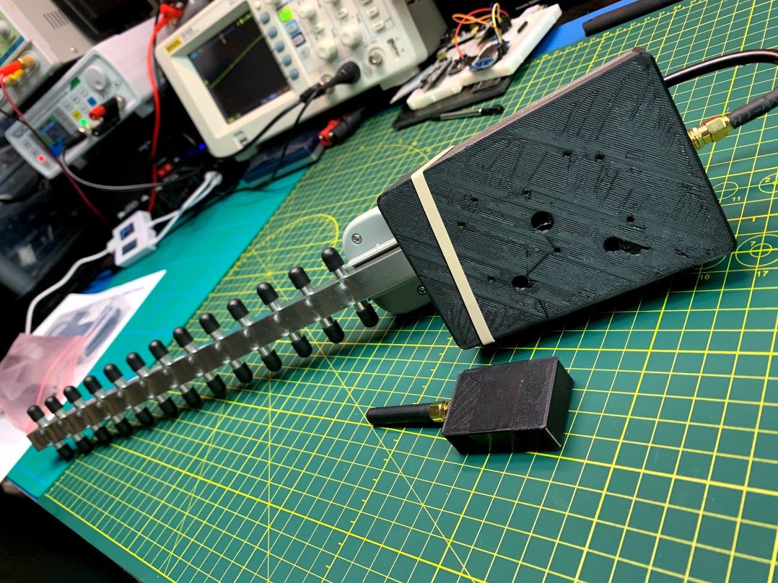
Photos/IMG_0349.jpg
