MKme/ResQ/Photos/IMG_0379.jpg

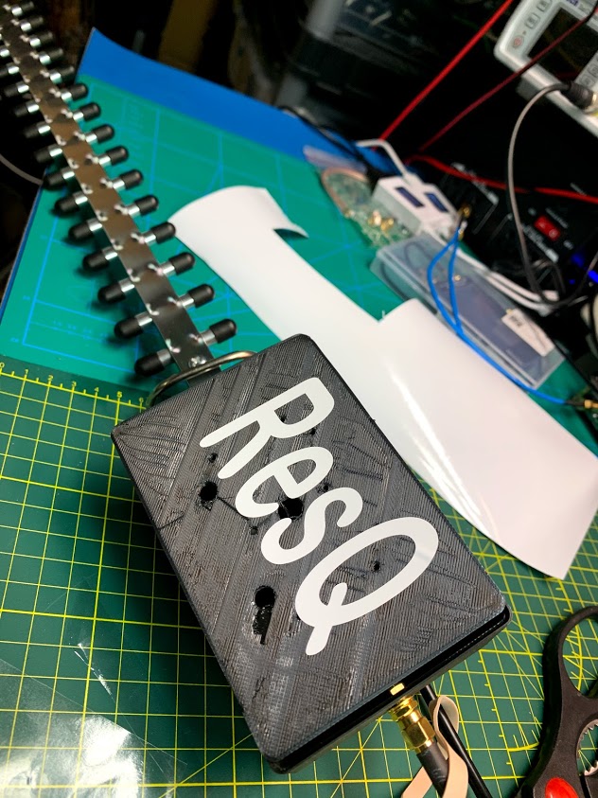
Photos/IMG_0379.jpg
