MKme/ResQ/Photos/IMG_0539.jpg

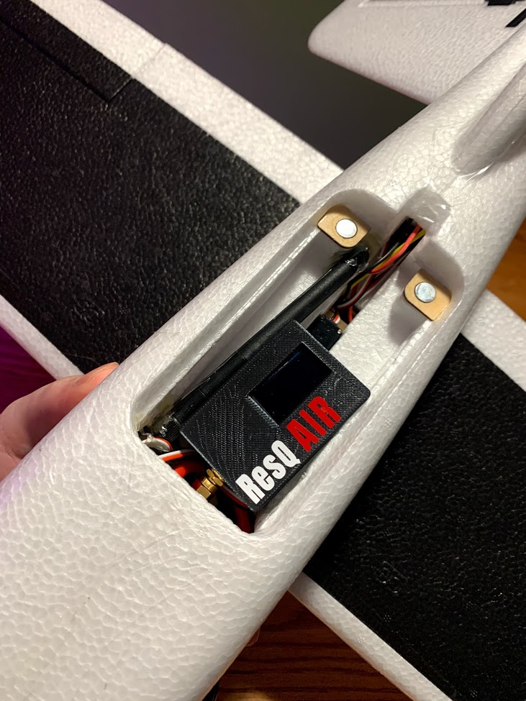
Photos/IMG_0539.jpg
