MKme/ResQ/Photos/IMG_0625.jpg

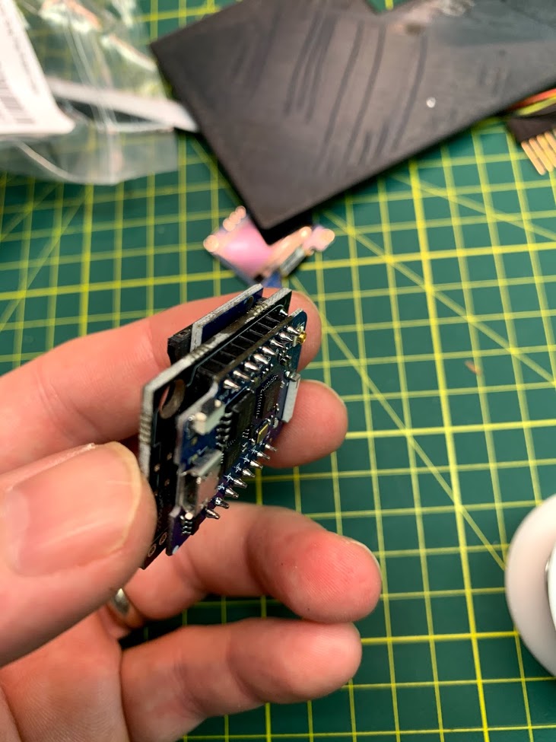
Photos/IMG_0625.jpg
