MKme/ResQ/Photos/IMG_0630.jpg

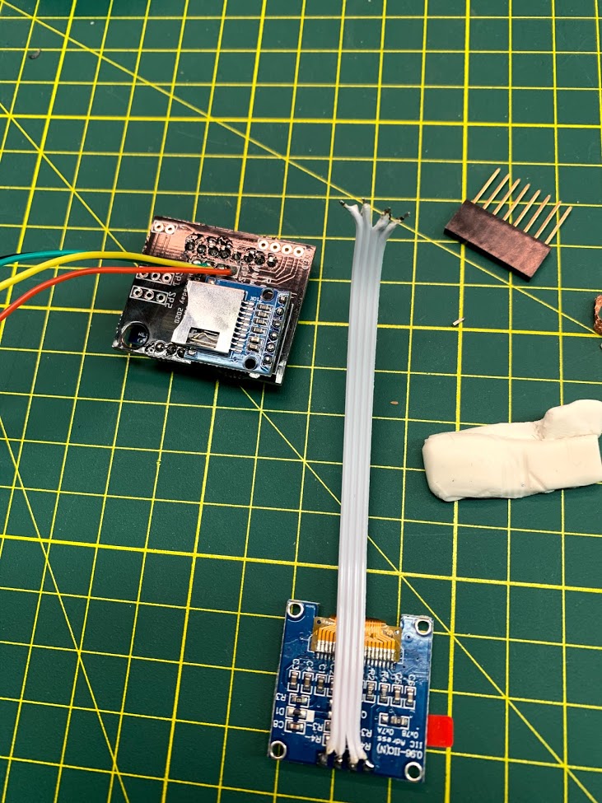
Photos/IMG_0630.jpg
