MKme/ResQ/Photos/IMG_0642.jpg

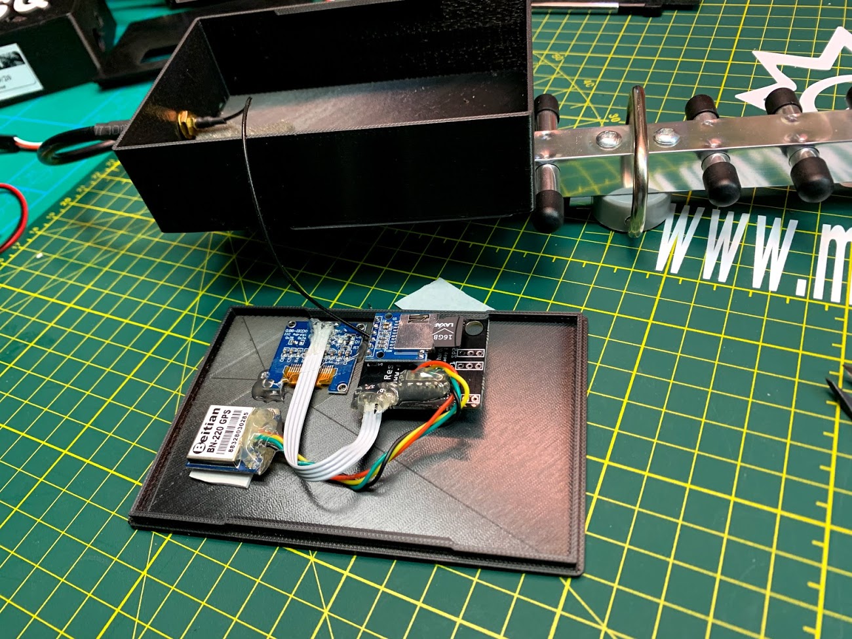
Photos/IMG_0642.jpg
