MKme/ResQ/Photos/IMG_0659.jpg

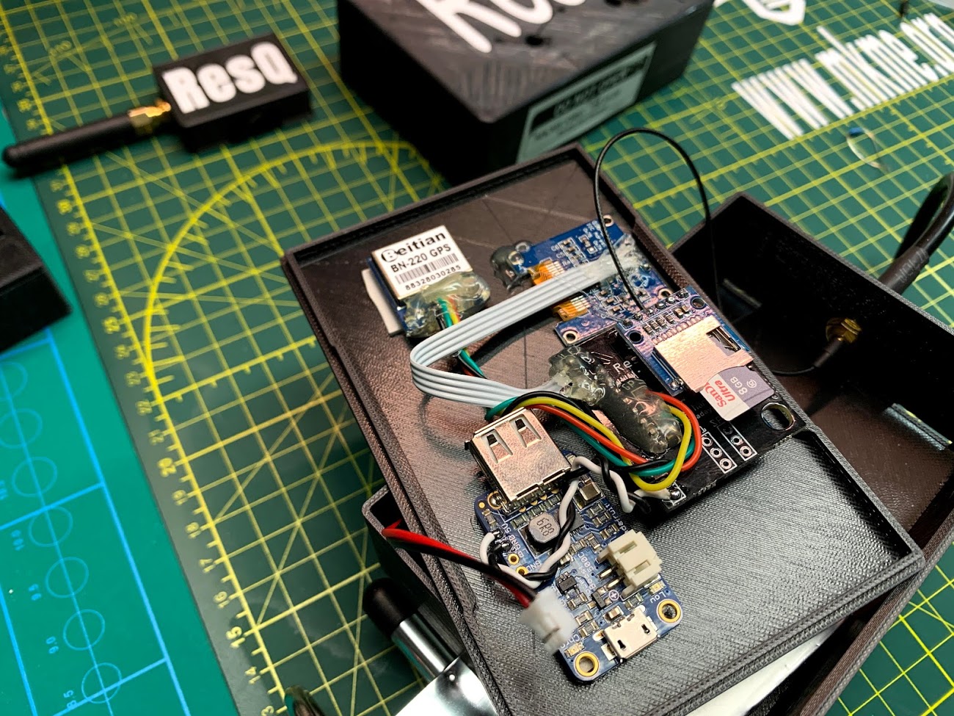
Photos/IMG_0659.jpg
