MKme/ResQ/Photos/IMG_0660.jpg

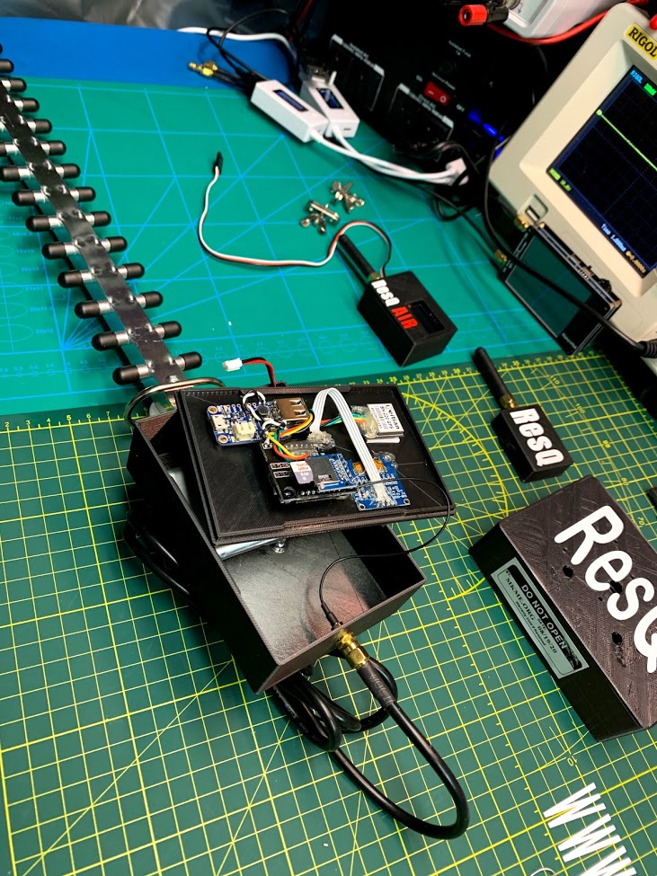
Photos/IMG_0660.jpg
