MKme/ResQ/Photos/IMG_0670.jpg

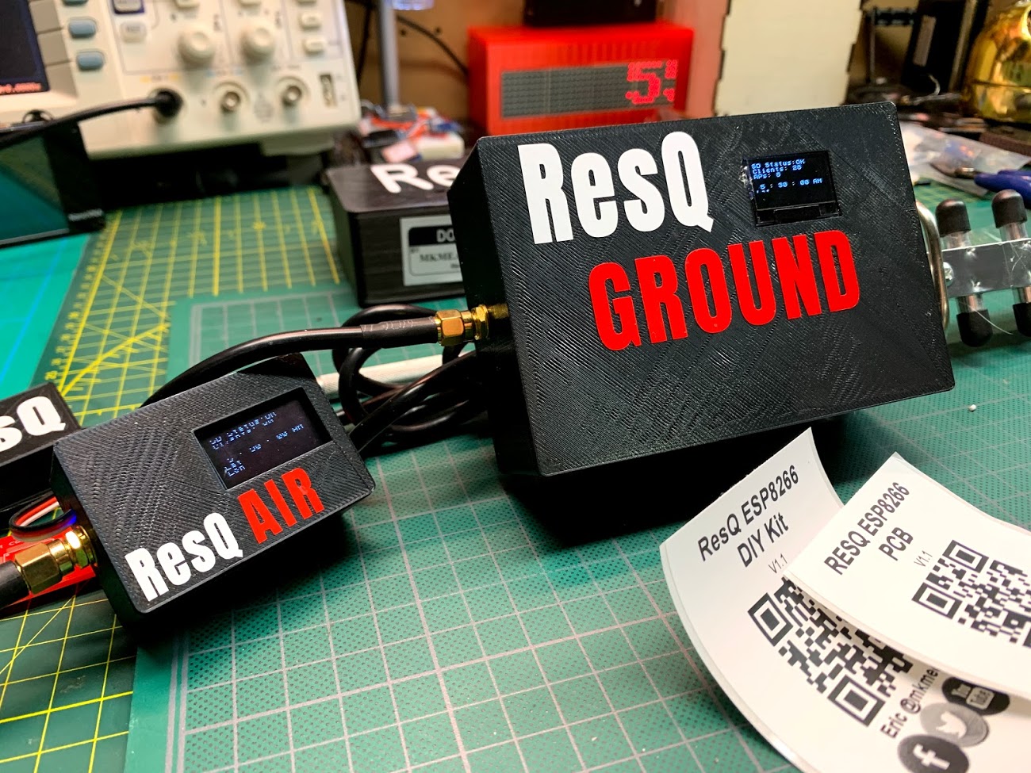
Photos/IMG_0670.jpg
