MKme/ResQ/Photos/IMG_0807.jpg

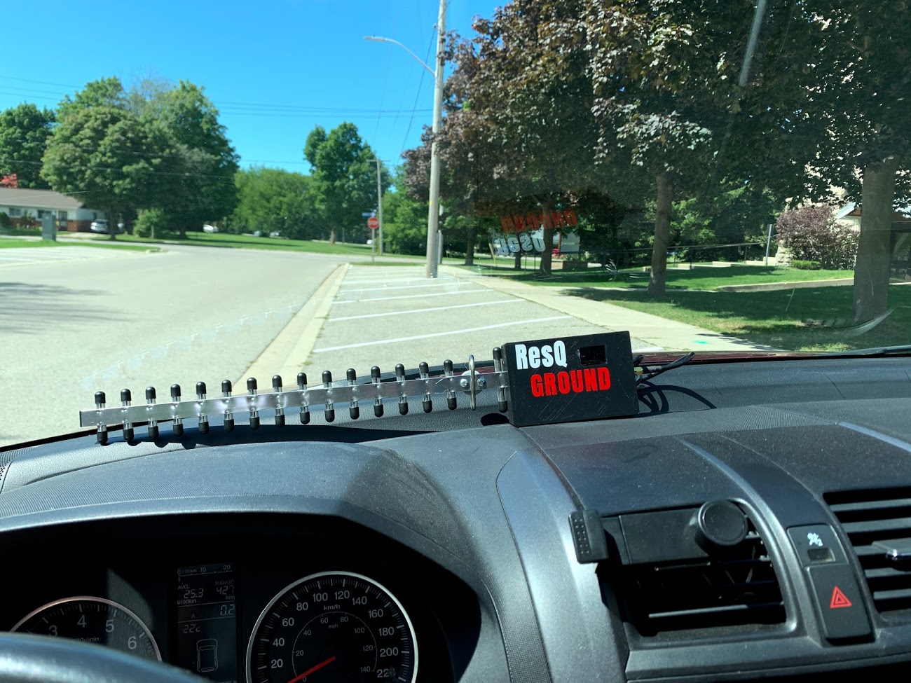
Photos/IMG_0807.jpg
