MKme/ResQ/Photos/IMG_0820.jpg

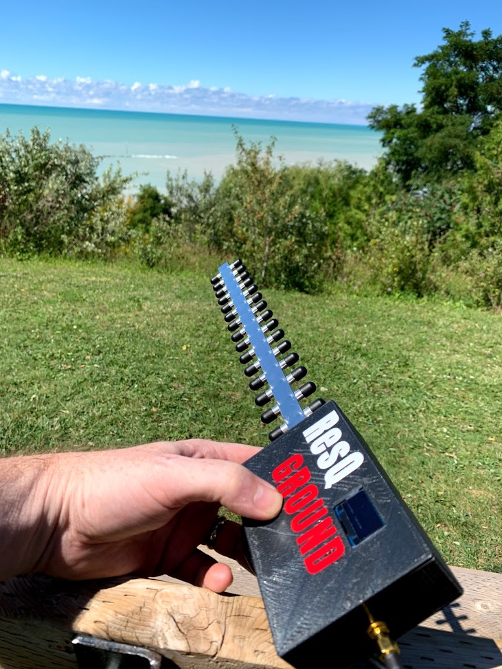
Photos/IMG_0820.jpg
