MKme/ResQ/Photos/IMG_0826.jpg

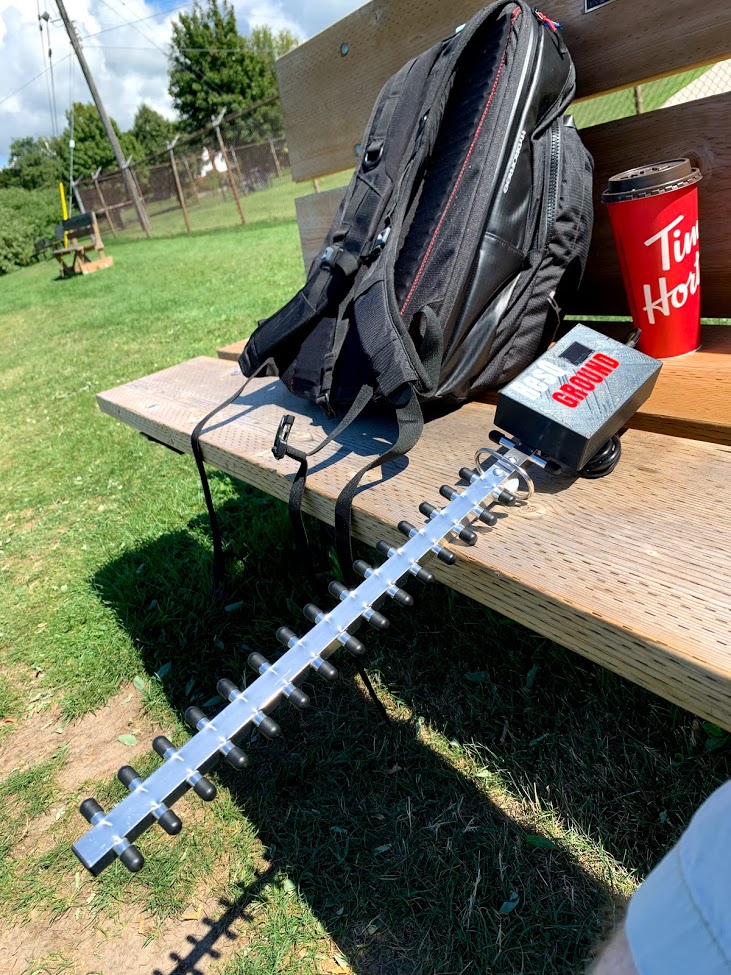
Photos/IMG_0826.jpg
