MKme/ResQ/Photos/IMG_1096.jpg

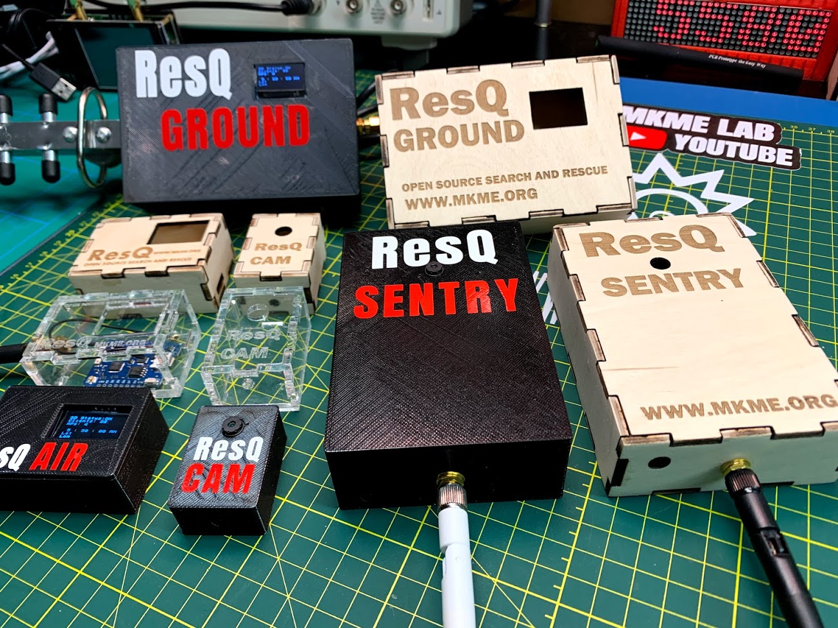
Photos/IMG_1096.jpg
