MKme/ResQ/Photos/IMG_1097.jpg

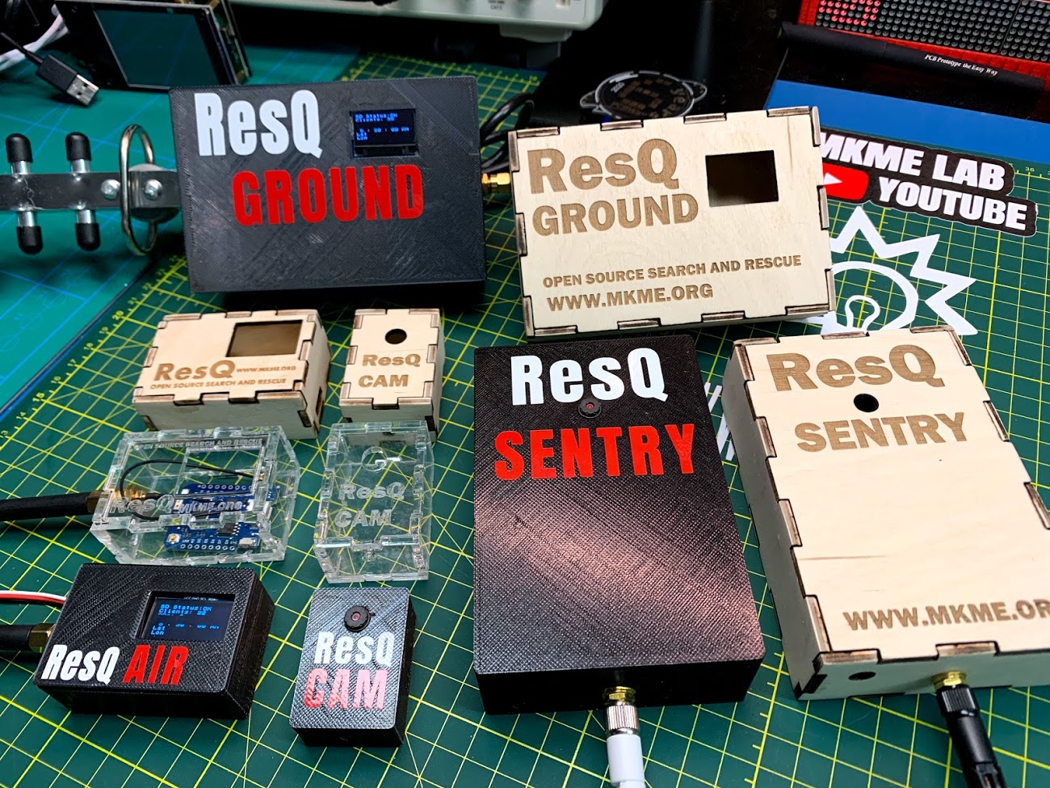
Photos/IMG_1097.jpg
