MKme/ResQ/Photos/IMG_3125.jpg

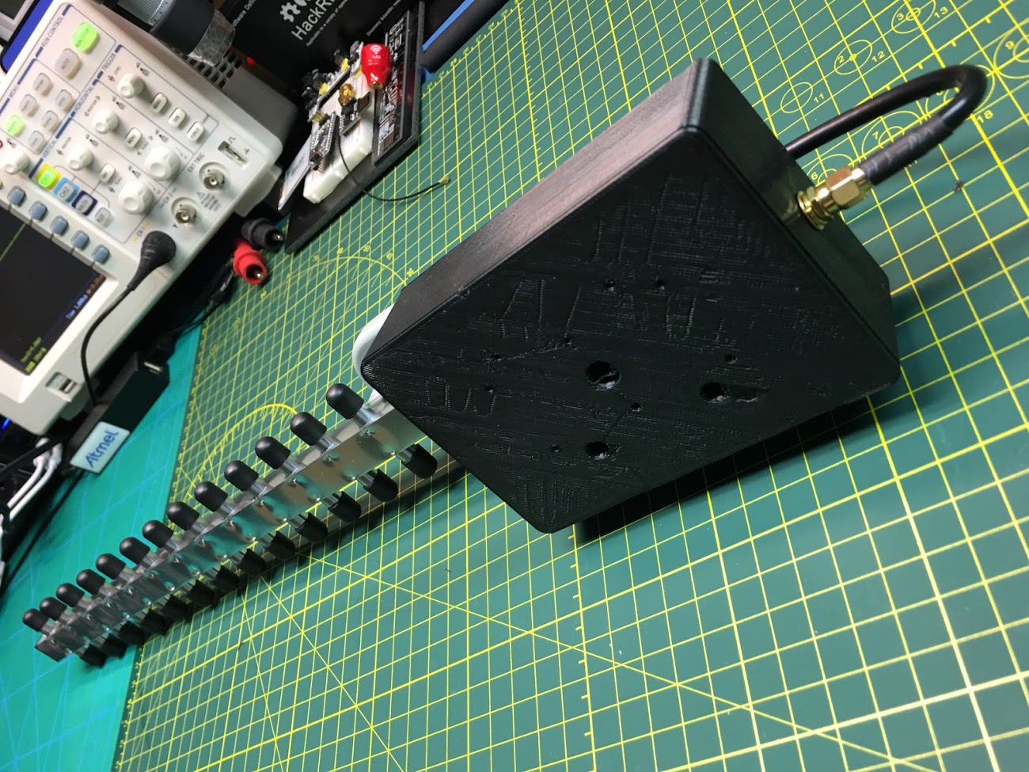
Photos/IMG_3125.jpg
