MKme/ResQ/Photos/Kits/32462DD9-EC00-4F45-B1A9-F2E413A55265.jpg

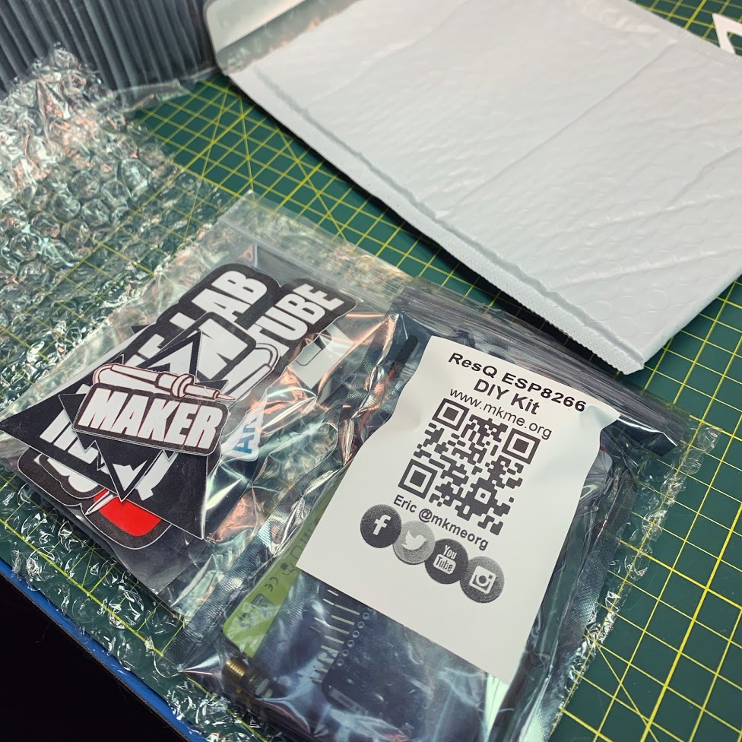
Photos/Kits/32462DD9-EC00-4F45-B1A9-F2E413A55265.jpg
