MKme/ResQ/Photos/Kits/C25DD262-713B-4B76-90C8-FA7FE2238E6B.jpg

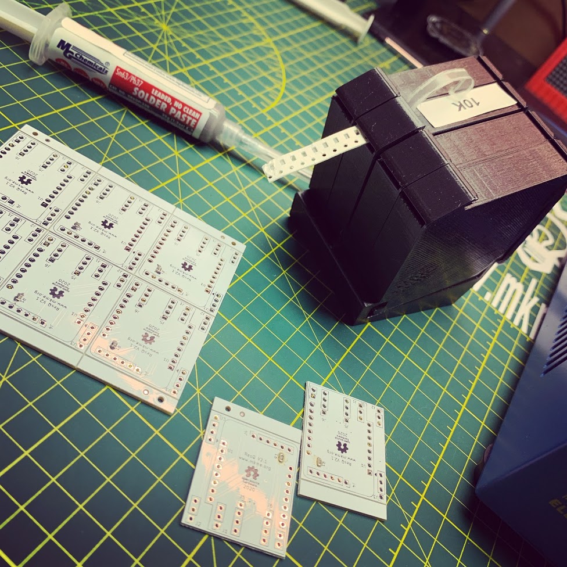
Photos/Kits/C25DD262-713B-4B76-90C8-FA7FE2238E6B.jpg
