MKme/ResQ/Photos/Kits/IMG_1240.jpg

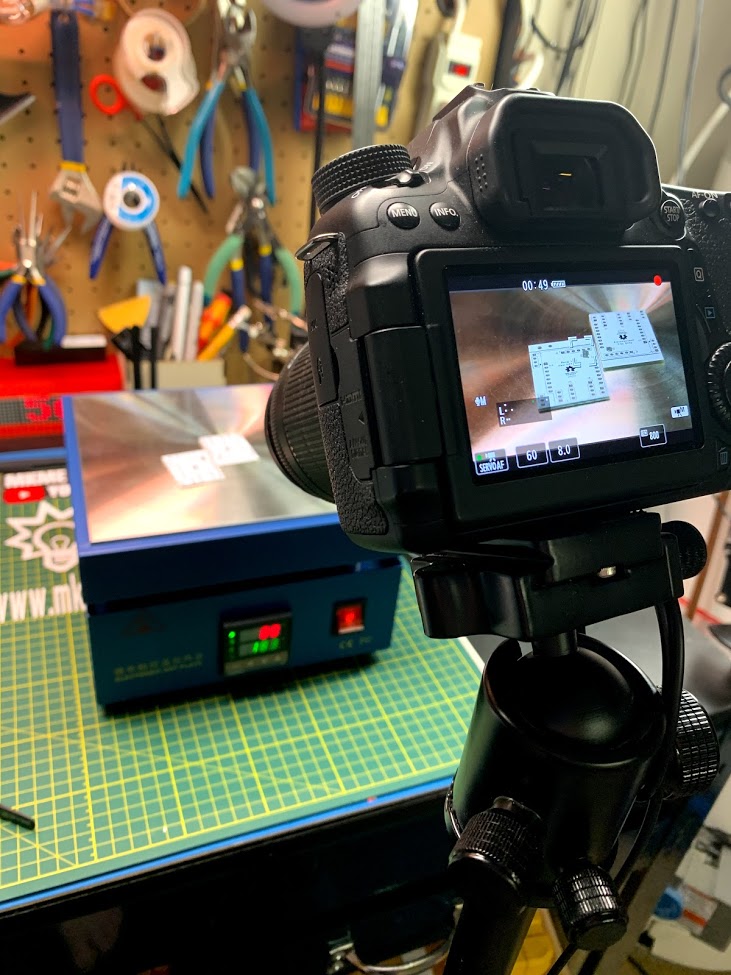
Photos/Kits/IMG_1240.jpg
