MKme/ResQ/Photos/Laser Cut Cases/IMG_0686.jpg

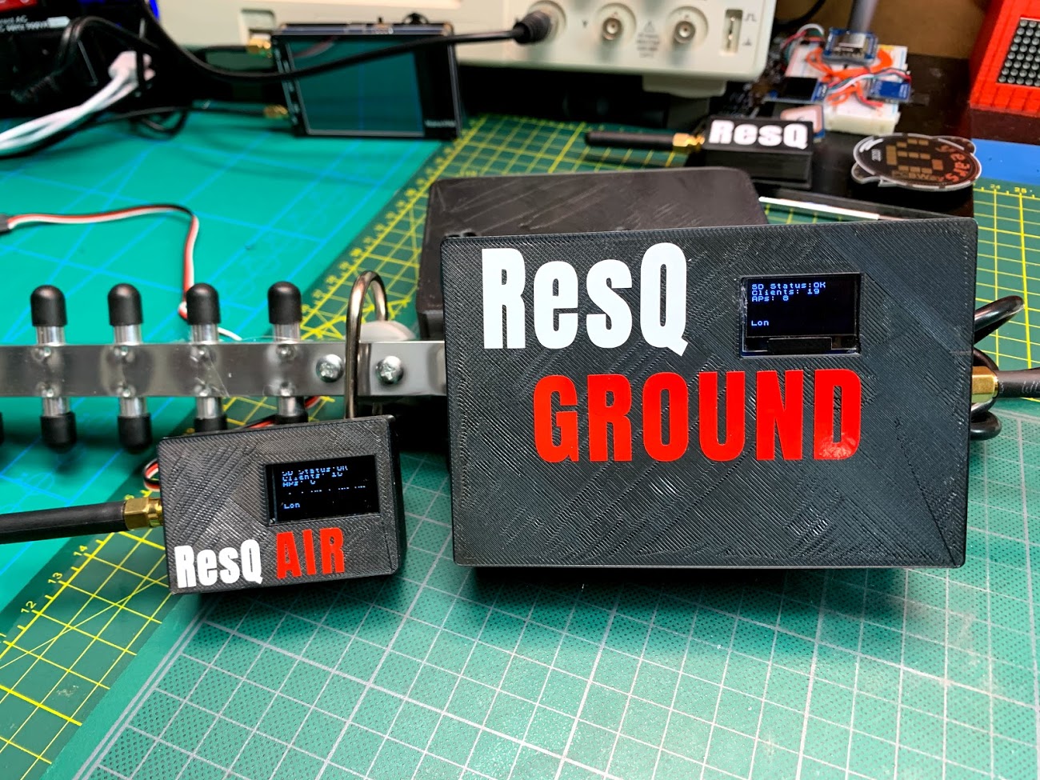
Photos/Laser Cut Cases/IMG_0686.jpg
