MKme/ResQ/Photos/Laser Cut Cases/IMG_0705.jpg

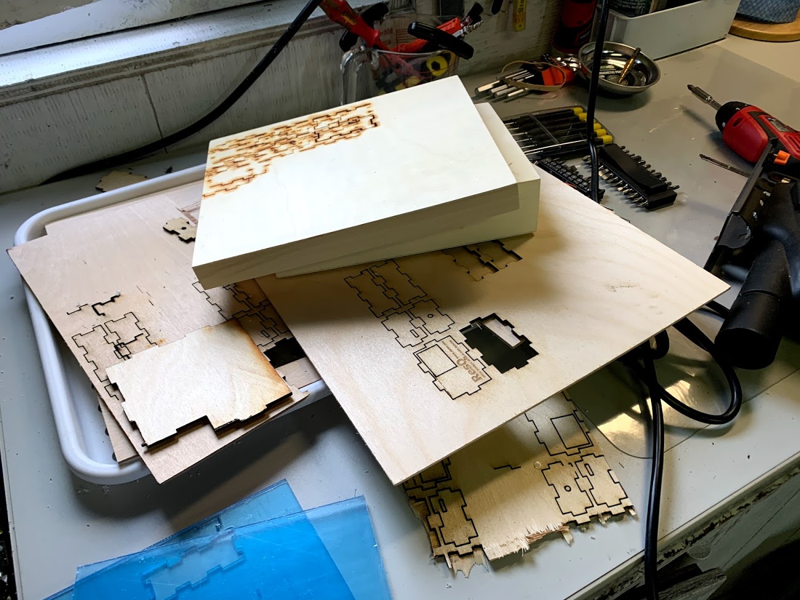
Photos/Laser Cut Cases/IMG_0705.jpg
