MKme/ResQ/Photos/Laser Cut Cases/IMG_0752.jpg

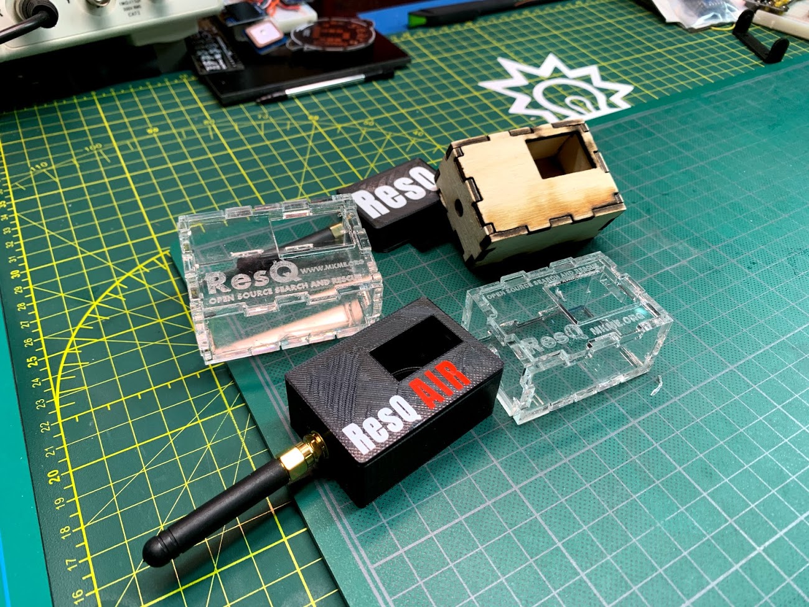
Photos/Laser Cut Cases/IMG_0752.jpg
