MKme/ResQ/Photos/Laser Cut Cases/IMG_0758.jpg

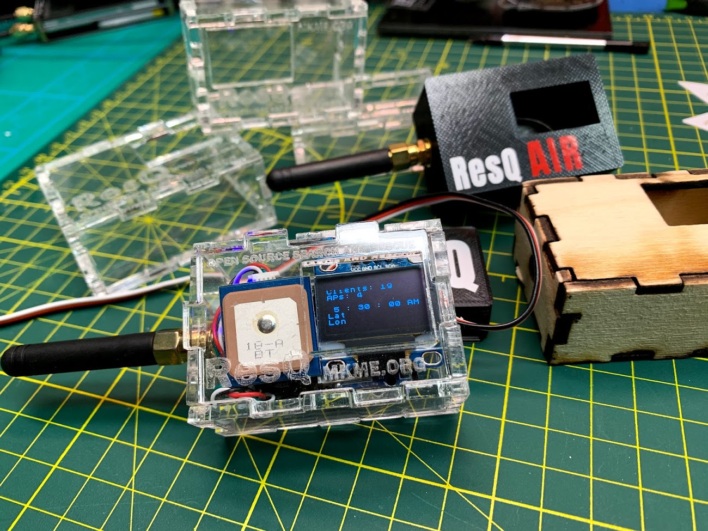
Photos/Laser Cut Cases/IMG_0758.jpg
