MKme/ResQ/Photos/Laser Cut Cases/IMG_0834.jpg

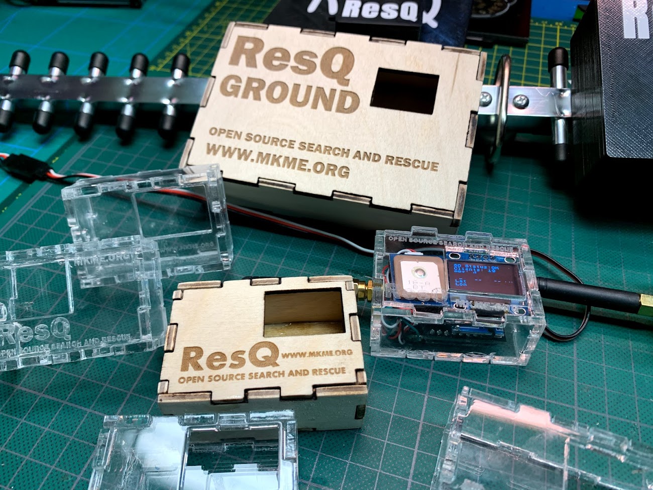
Photos/Laser Cut Cases/IMG_0834.jpg
