MKme/ResQ/Photos/MAcaddresses.png

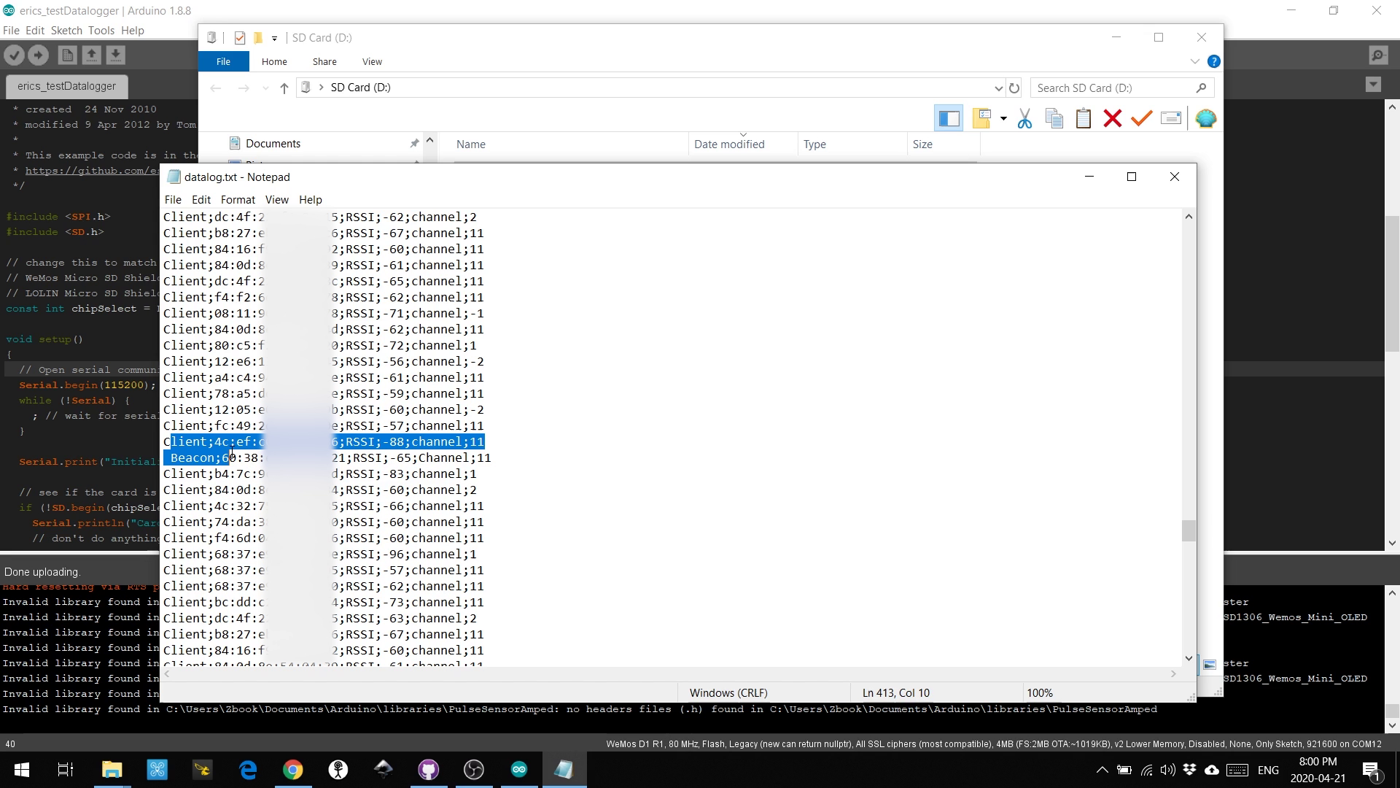
Photos/MAcaddresses.png
