MKme/ResQ/Photos/NanoTalonprogramming.jpg

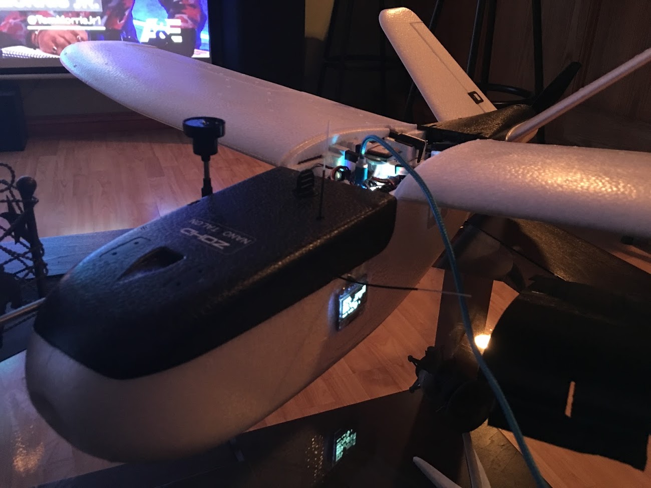
Photos/NanoTalonprogramming.jpg
