MKme/ResQ/Photos/OLED and SD.jpg

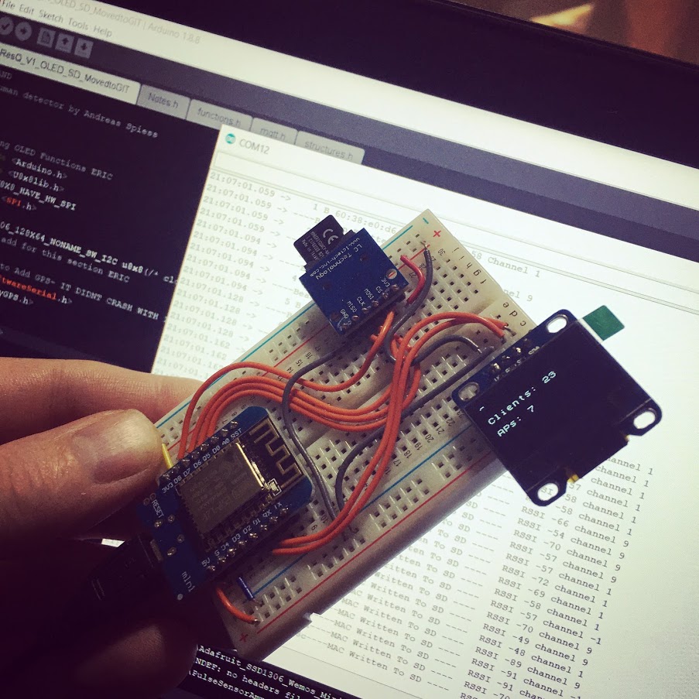
Photos/OLED and SD.jpg
