MKme/ResQ/Photos/PCB V2.1/IMG_0991.jpg

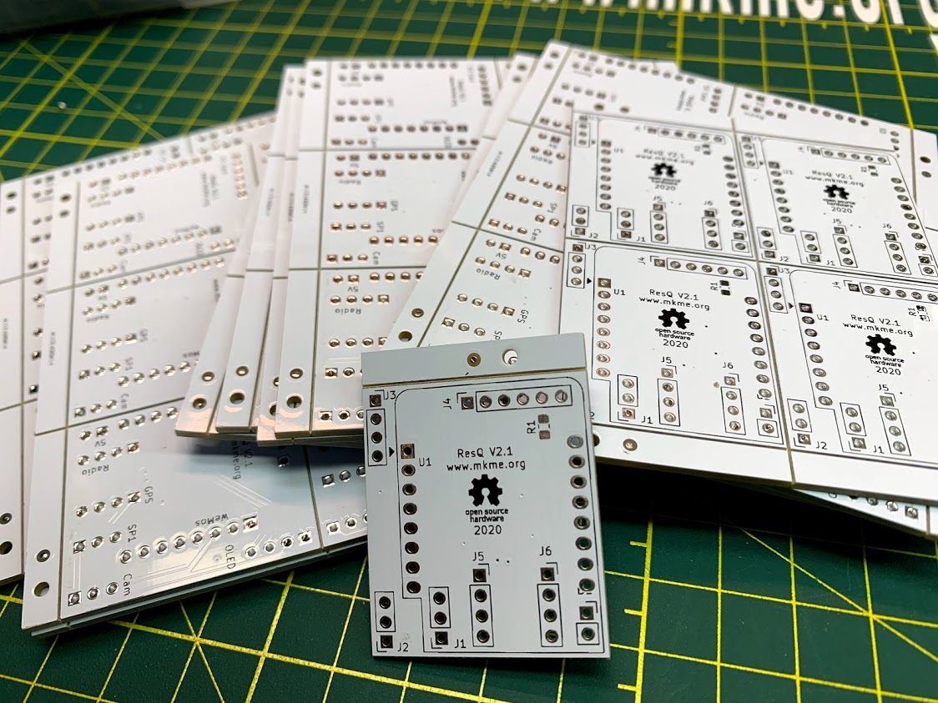
Photos/PCB V2.1/IMG_0991.jpg
