MKme/ResQ/Photos/PCB V2.1/IMG_0994.jpg

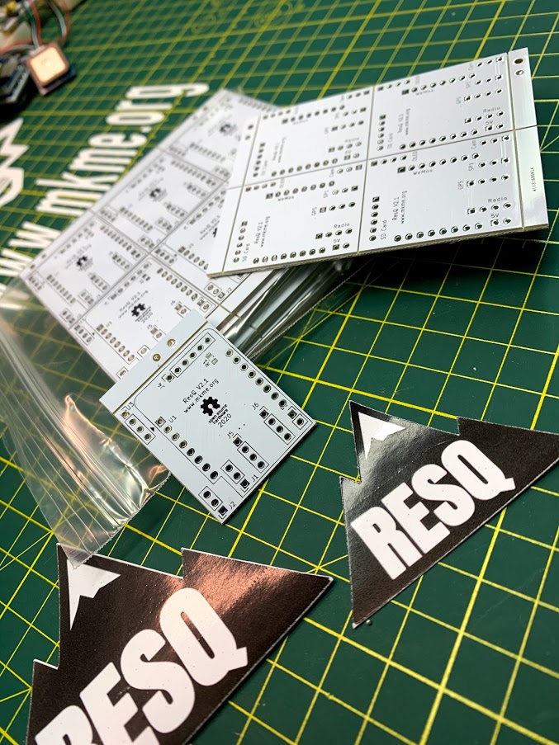
Photos/PCB V2.1/IMG_0994.jpg
