MKme/ResQ/Photos/PCB V2.1/IMG_0998.jpg

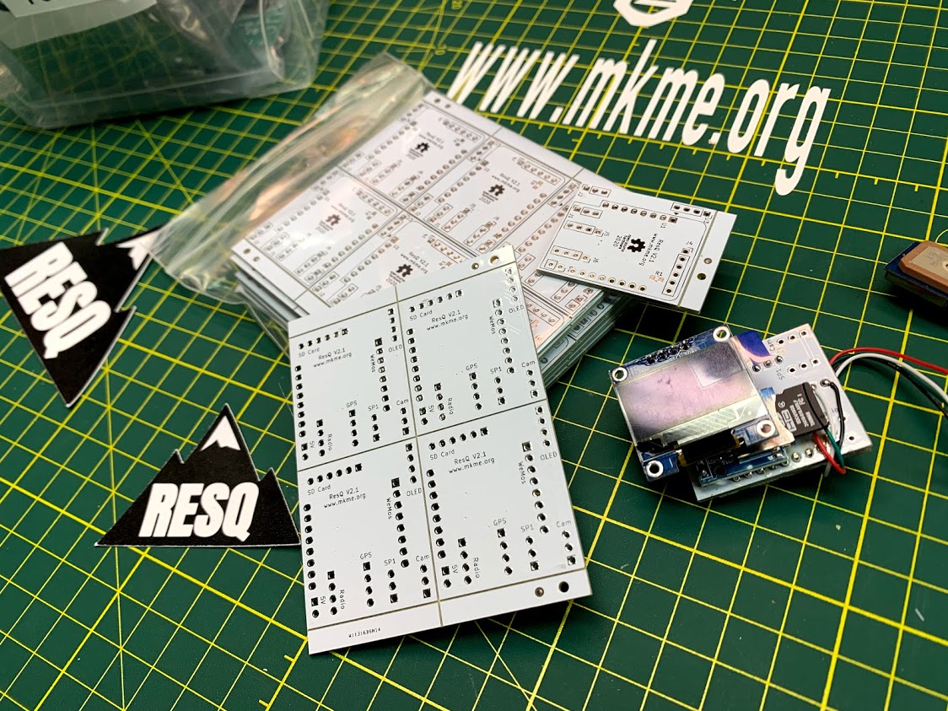
Photos/PCB V2.1/IMG_0998.jpg
