MKme/ResQ/Photos/PCB V2.1/IMG_1001.jpg

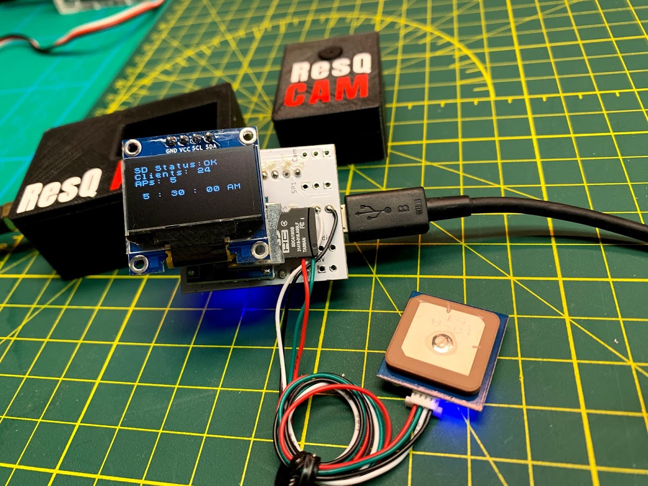
Photos/PCB V2.1/IMG_1001.jpg
