MKme/ResQ/Photos/ProjectBox.PNG

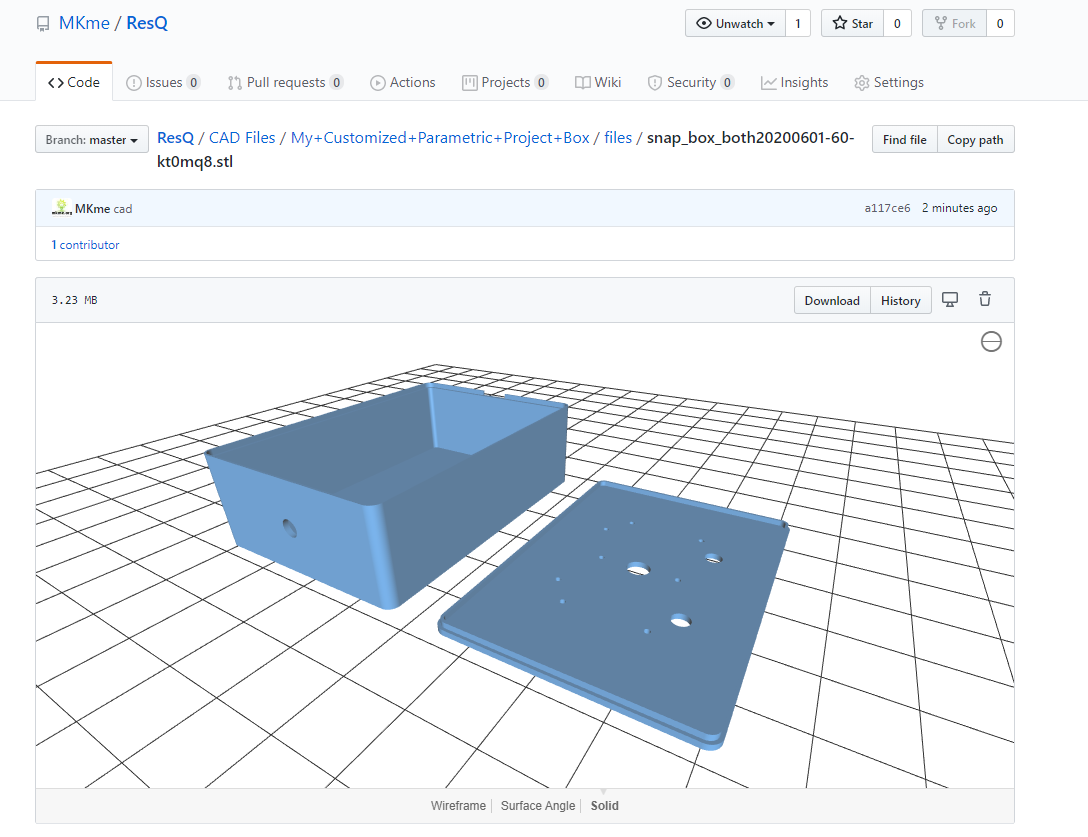
Photos/ProjectBox.PNG
