MKme/ResQ/Photos/proto.jpg

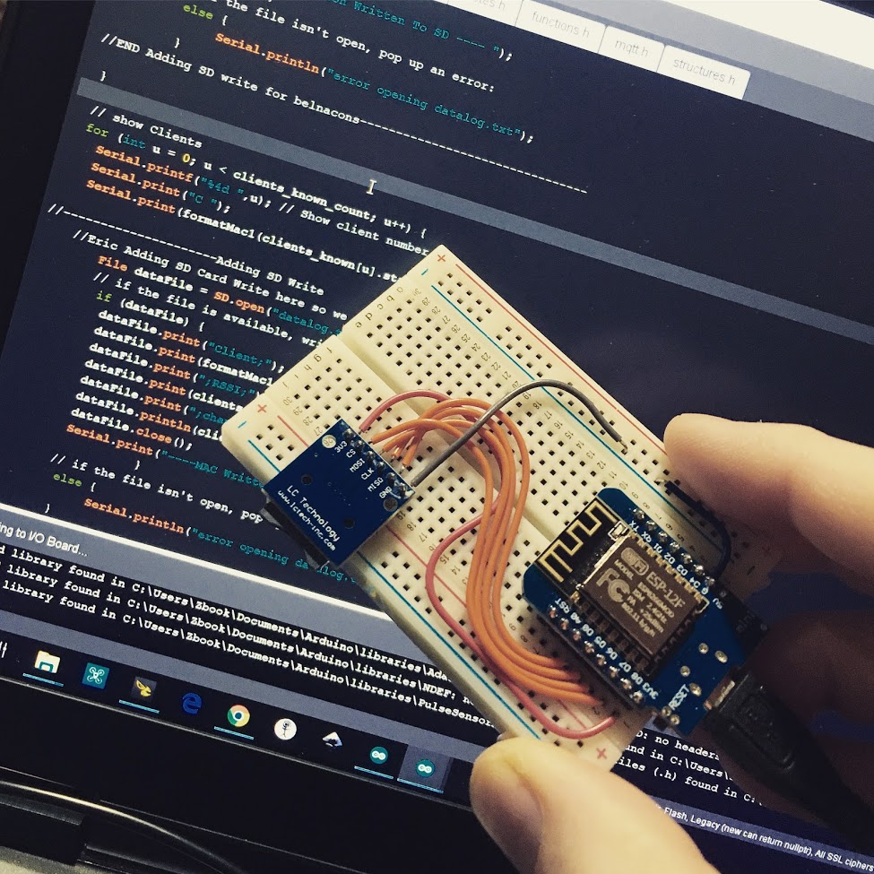
Photos/proto.jpg
