MKme/ResQ/Photos/ResQ Cam Photos/61bZxEnlkxL._AC_SL1200_.jpg

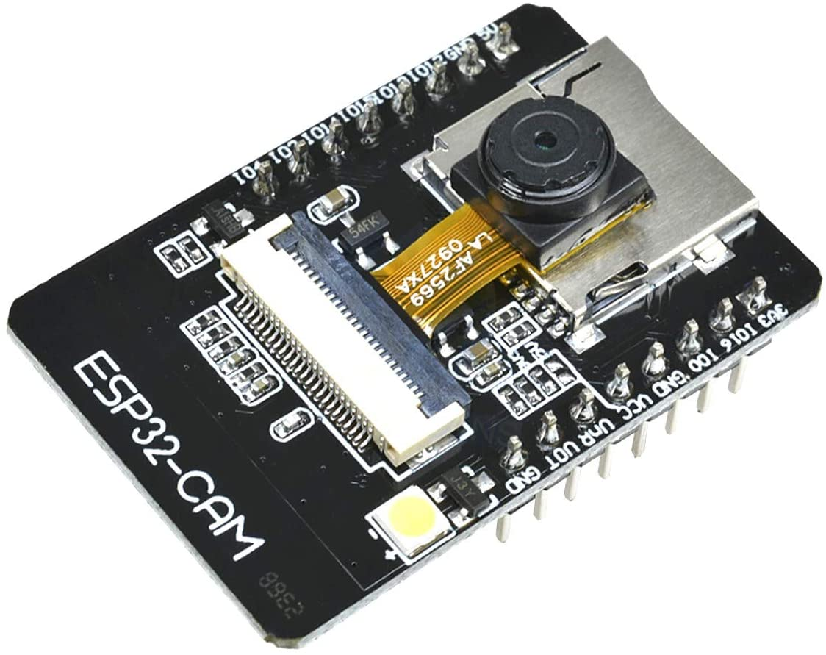
Photos/ResQ Cam Photos/61bZxEnlkxL._AC_SL1200_.jpg
