MKme/ResQ/Photos/ResQ Cam Photos/61Rg76OVZ8L._AC_SL1200_.jpg

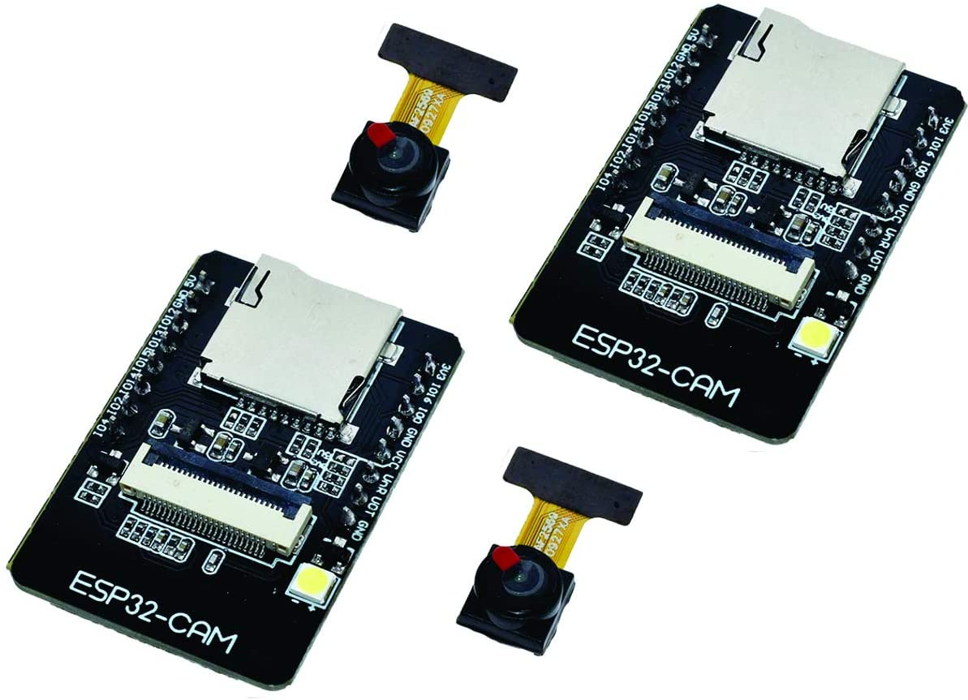
Photos/ResQ Cam Photos/61Rg76OVZ8L._AC_SL1200_.jpg
