MKme/ResQ/Photos/ResQ Cam Photos/61VzMgN85RL._AC_SL1200_.jpg

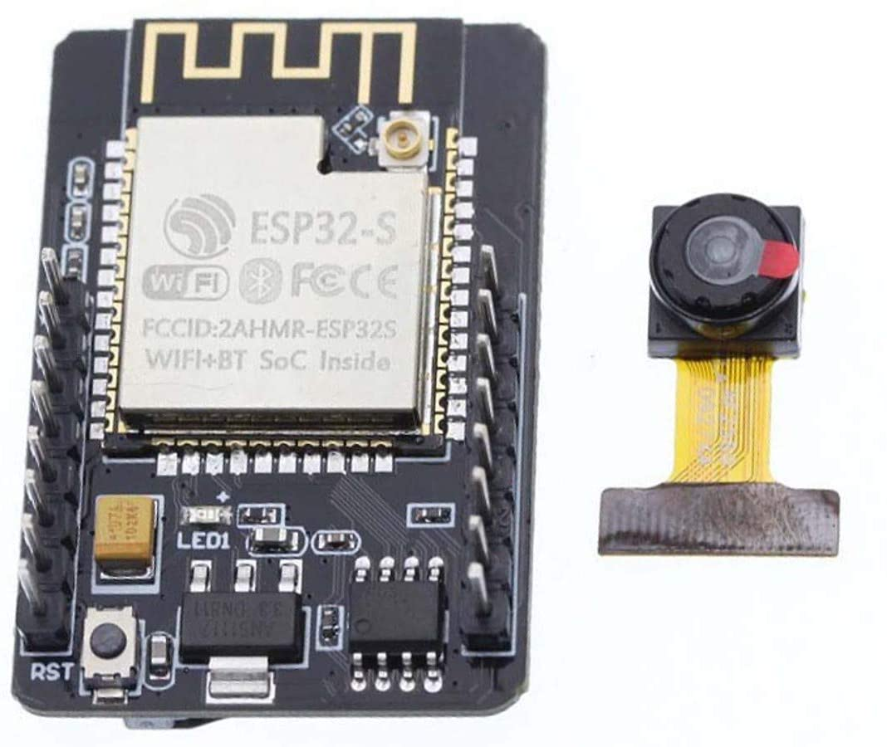
Photos/ResQ Cam Photos/61VzMgN85RL._AC_SL1200_.jpg
