MKme/ResQ/Photos/ResQ Cam Photos/71iEnwv+FJL._AC_SL1200_.jpg

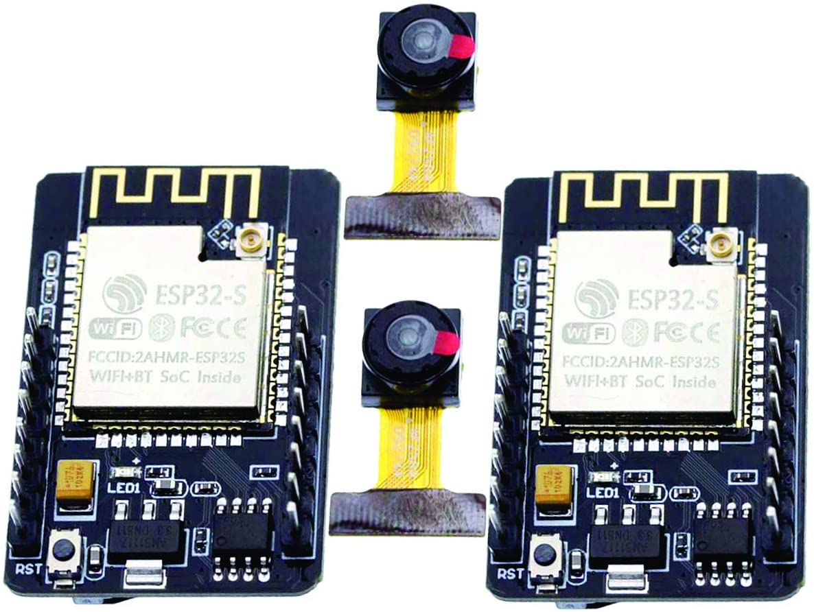
Photos/ResQ Cam Photos/71iEnwv+FJL._AC_SL1200_.jpg
