MKme/ResQ/Photos/ResQ Cam Photos/54250D96-BCF0-466D-9418-B9D42D90DC9A.jpg

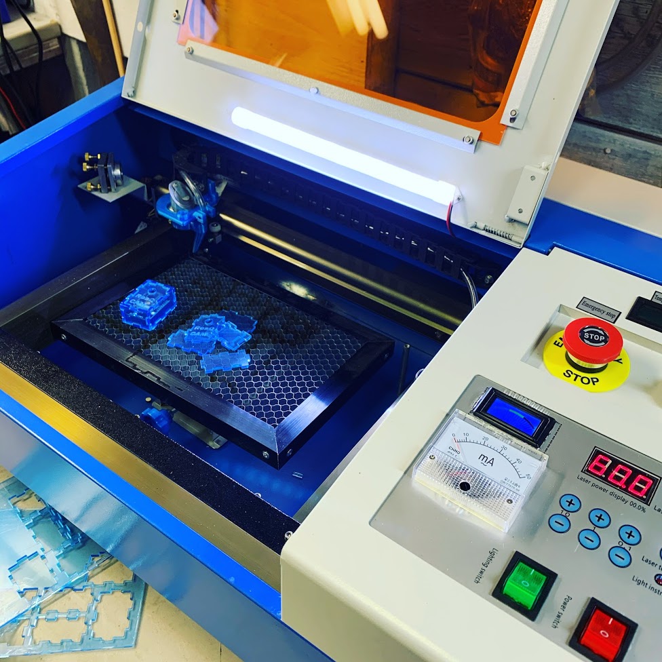
Photos/ResQ Cam Photos/54250D96-BCF0-466D-9418-B9D42D90DC9A.jpg
