MKme/ResQ/Photos/ResQ Cam Photos/Cam enclosure .PNG

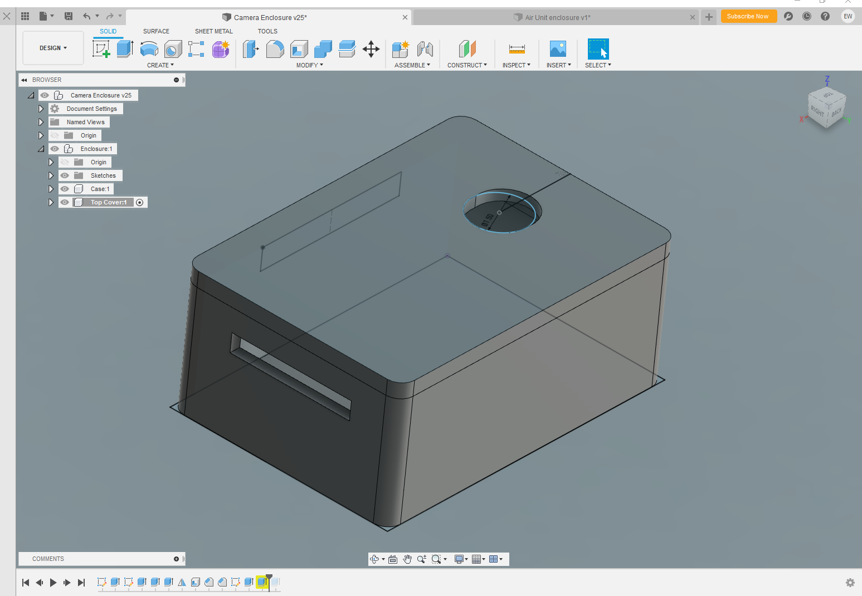
Photos/ResQ Cam Photos/Cam enclosure .PNG
