MKme/ResQ/Photos/ResQ Cam Photos/IMG_0904.jpg

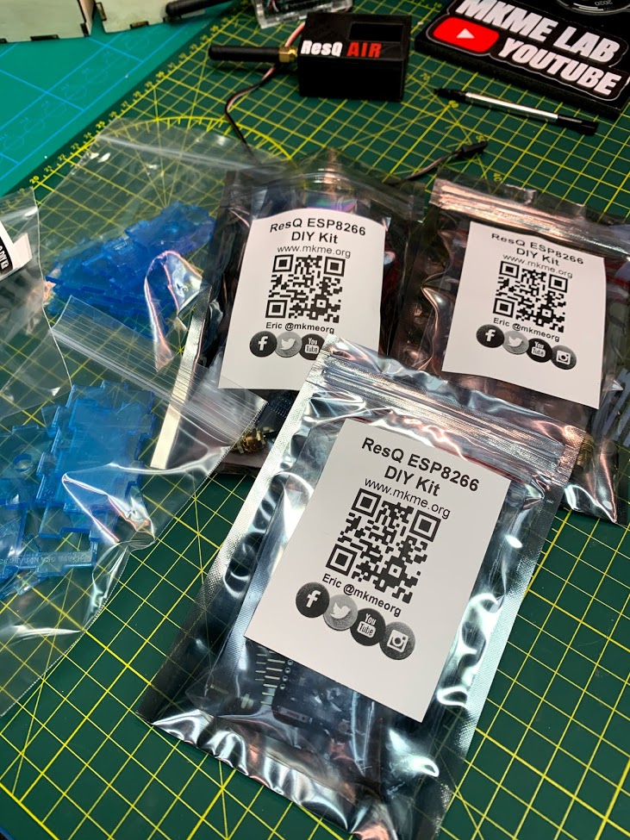
Photos/ResQ Cam Photos/IMG_0904.jpg
