MKme/ResQ/Photos/ResQ Cam Photos/IMG_0908.jpg

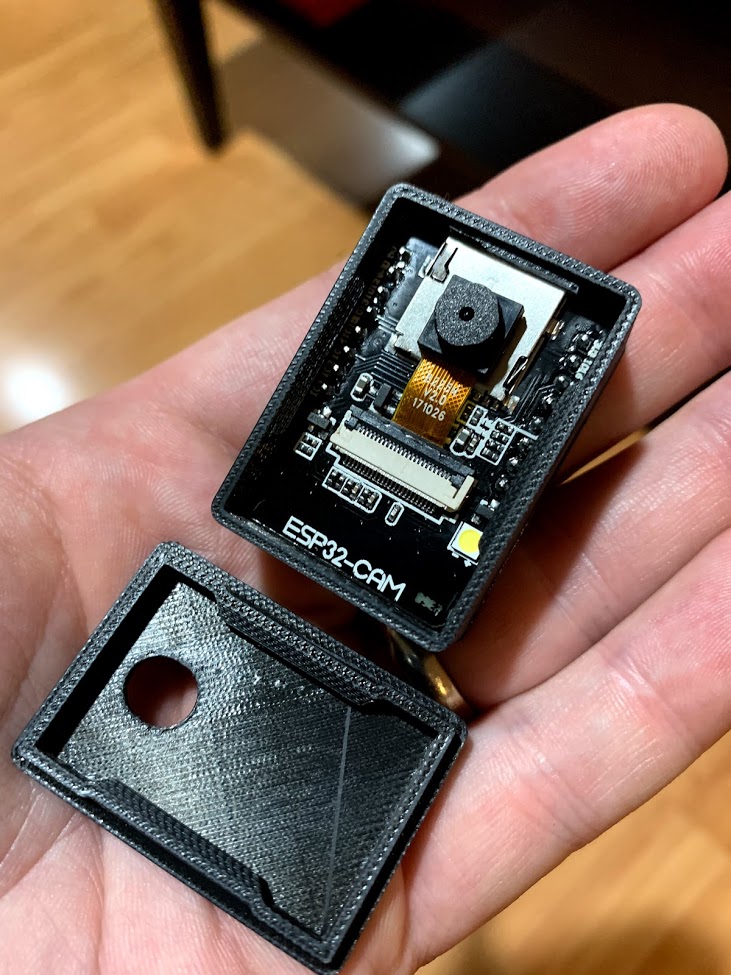
Photos/ResQ Cam Photos/IMG_0908.jpg
