MKme/ResQ/Photos/ResQ Cam Photos/IMG_0913.jpg

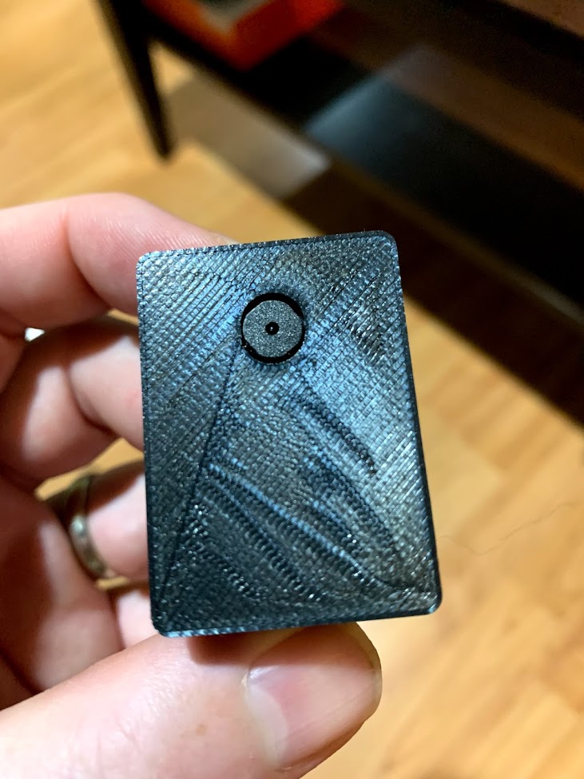
Photos/ResQ Cam Photos/IMG_0913.jpg
