MKme/ResQ/Photos/ResQ Cam Photos/IMG_0914.jpg

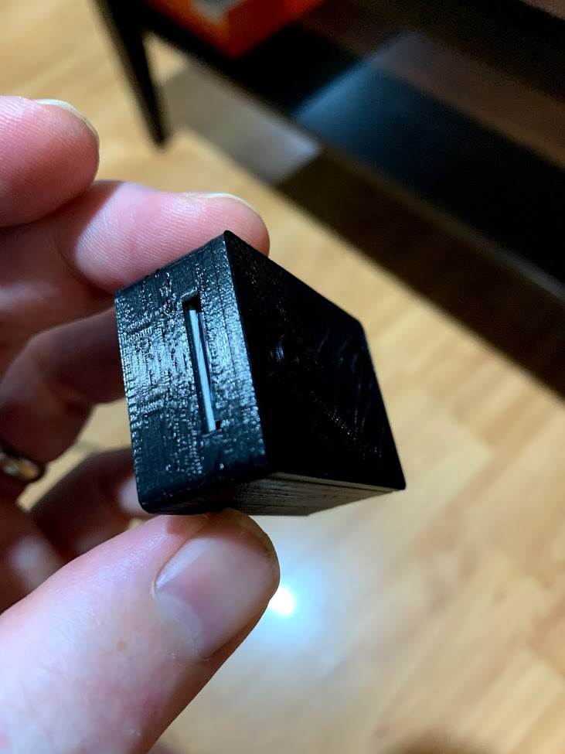
Photos/ResQ Cam Photos/IMG_0914.jpg
