MKme/ResQ/Photos/ResQ Cam Photos/IMG_0928.jpg

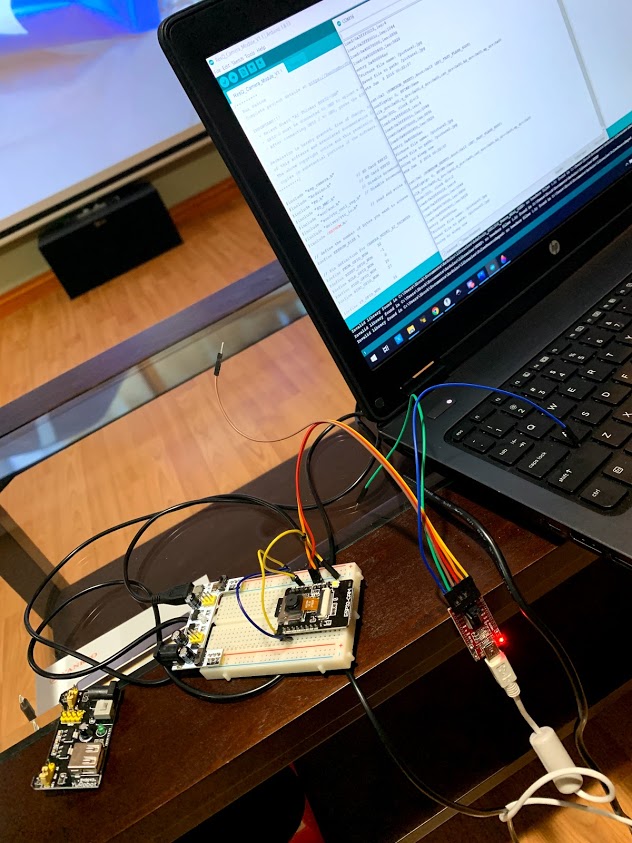
Photos/ResQ Cam Photos/IMG_0928.jpg
