MKme/ResQ/Photos/ResQ Cam Photos/IMG_0930.jpg

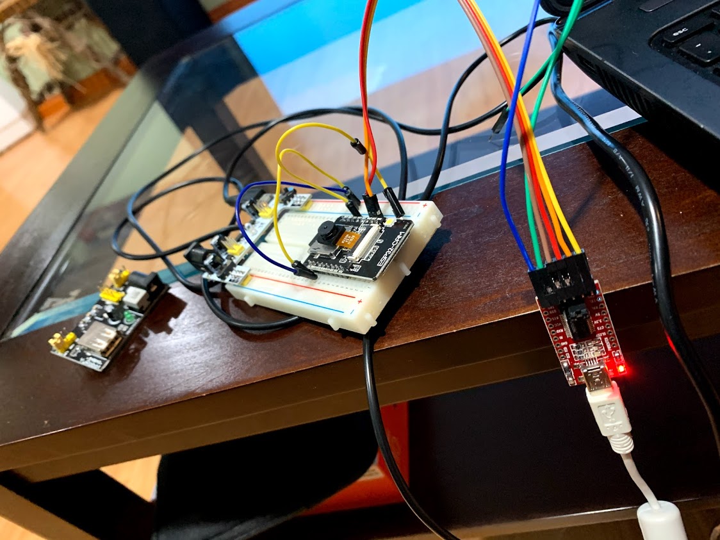
Photos/ResQ Cam Photos/IMG_0930.jpg
