MKme/ResQ/Photos/ResQ Cam Photos/IMG_0932.jpg

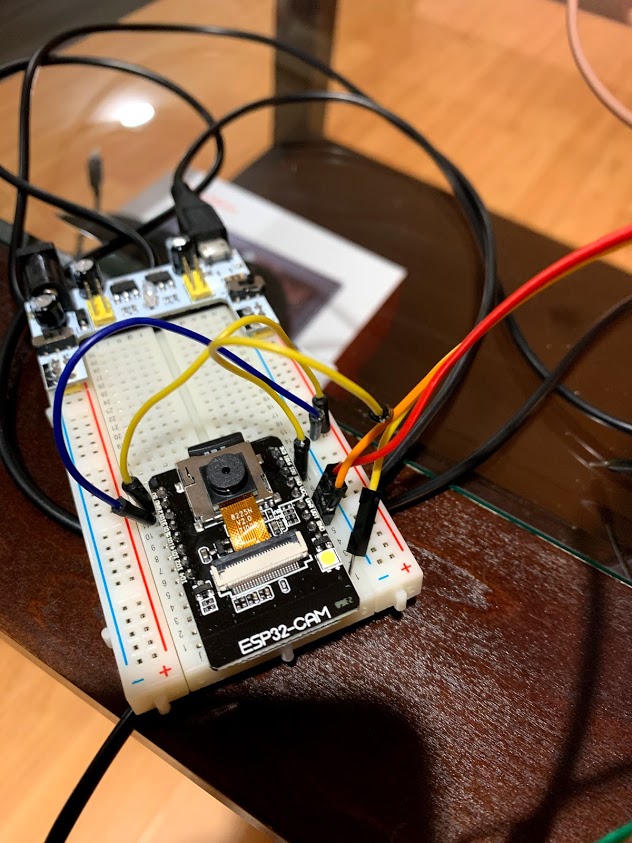
Photos/ResQ Cam Photos/IMG_0932.jpg
