MKme/ResQ/Photos/ResQ Cam Photos/IMG_1034.jpg

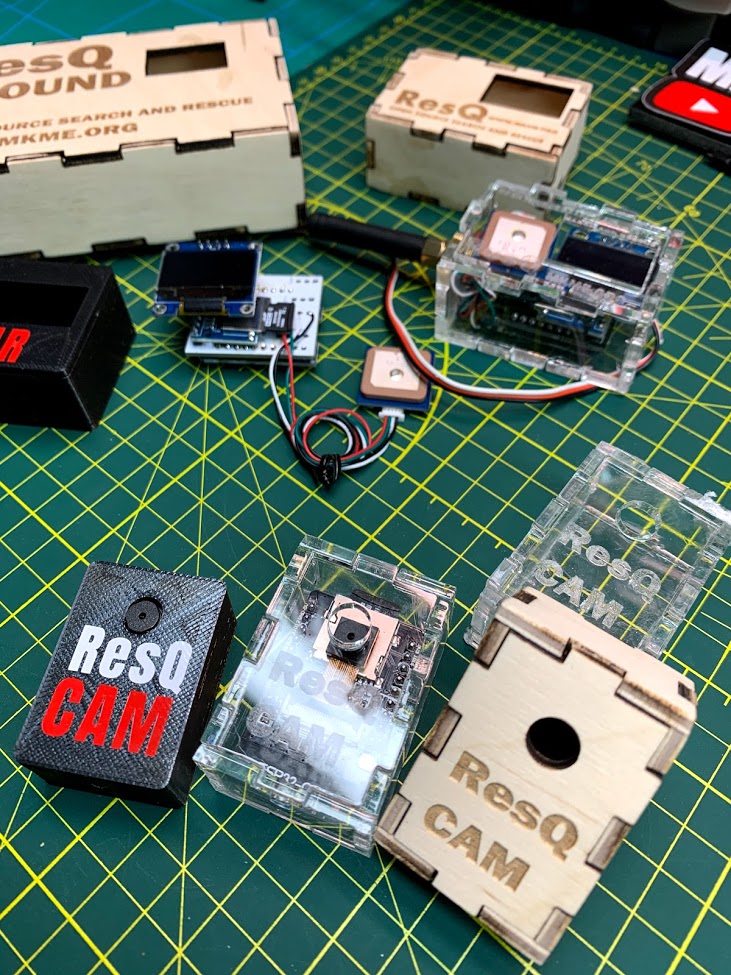
Photos/ResQ Cam Photos/IMG_1034.jpg
