MKme/ResQ/Photos/ResQ Cam Photos/IMG_1042.jpg

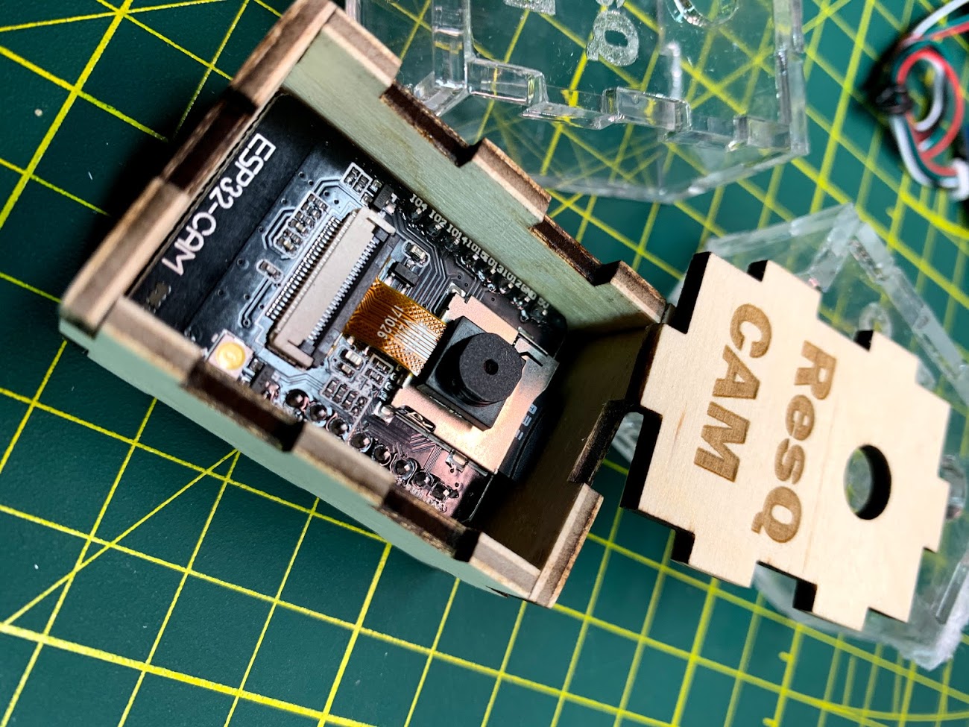
Photos/ResQ Cam Photos/IMG_1042.jpg
