MKme/ResQ/Photos/ResQ Cam Photos/IMG_1046.jpg

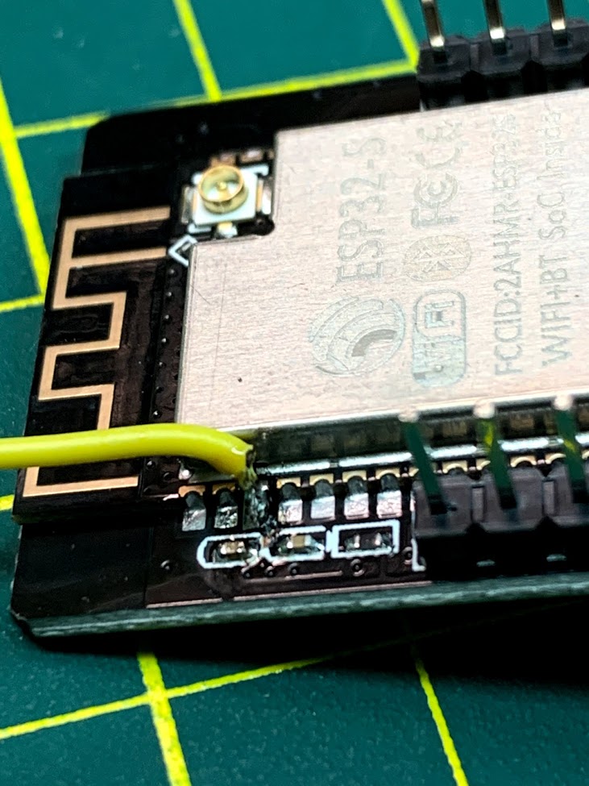
Photos/ResQ Cam Photos/IMG_1046.jpg
