MKme/ResQ/Photos/ResQ Cam Photos/IMG_1049.jpg

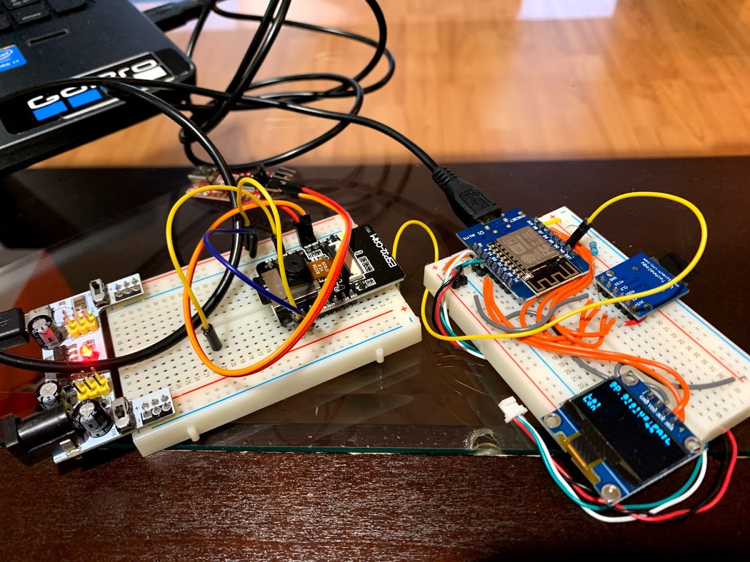
Photos/ResQ Cam Photos/IMG_1049.jpg
