MKme/ResQ/Photos/ResQ Cam Photos/picture19.jpg

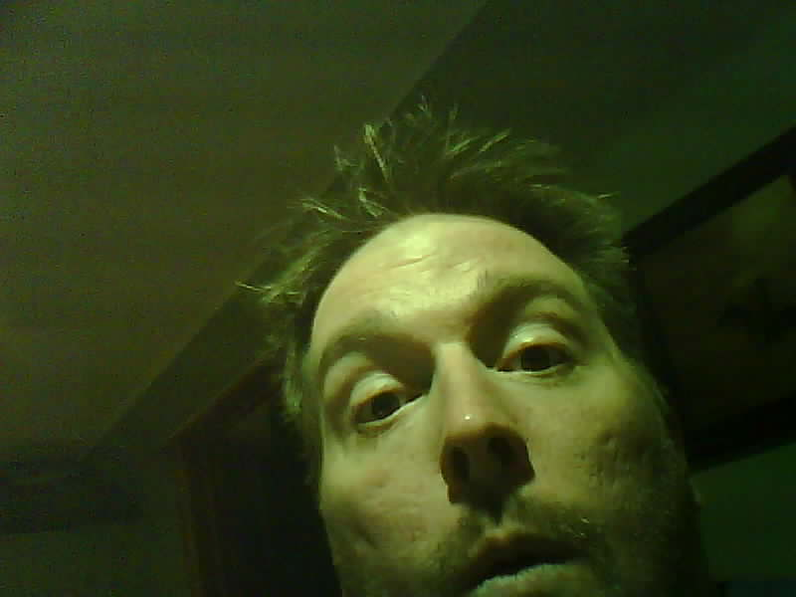
Photos/ResQ Cam Photos/picture19.jpg
