MKme/ResQ/Photos/ResQ Cam Photos/SentryEnclosure .PNG

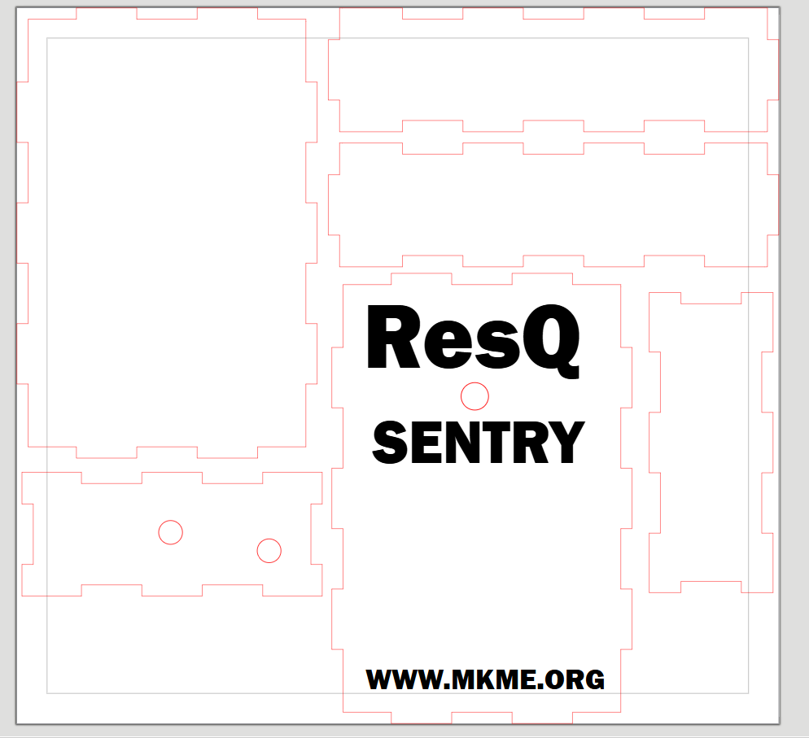
Photos/ResQ Cam Photos/SentryEnclosure .PNG
