MKme/ResQ/Photos/ResQ Cam Photos/trig.PNG

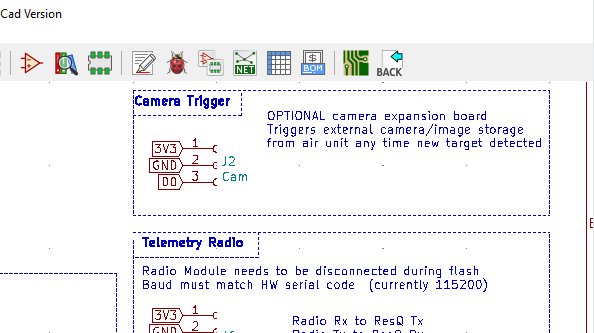
Photos/ResQ Cam Photos/trig.PNG
