MKme/ResQ/Photos/rx5808-5.jpg

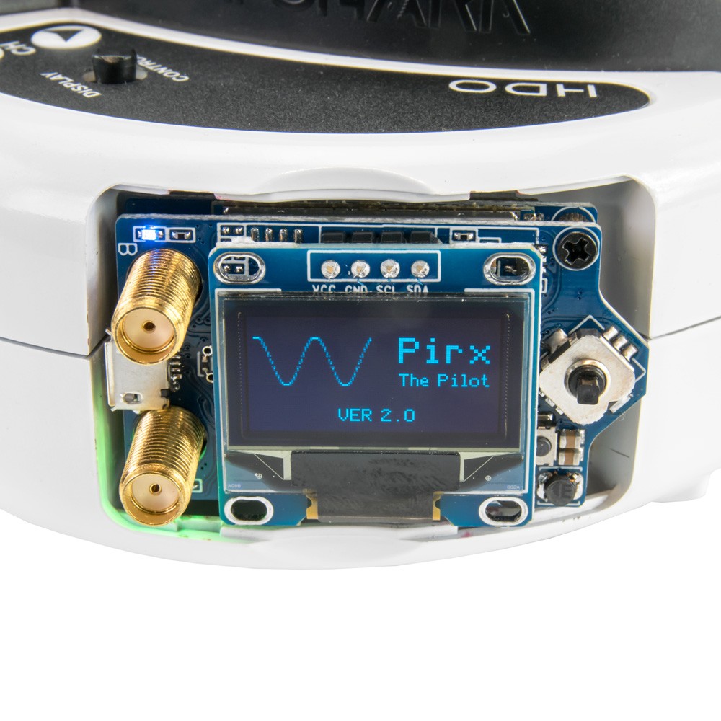
Photos/rx5808-5.jpg
