MKme/ResQ/Photos/Schematic with Cam interface .PNG

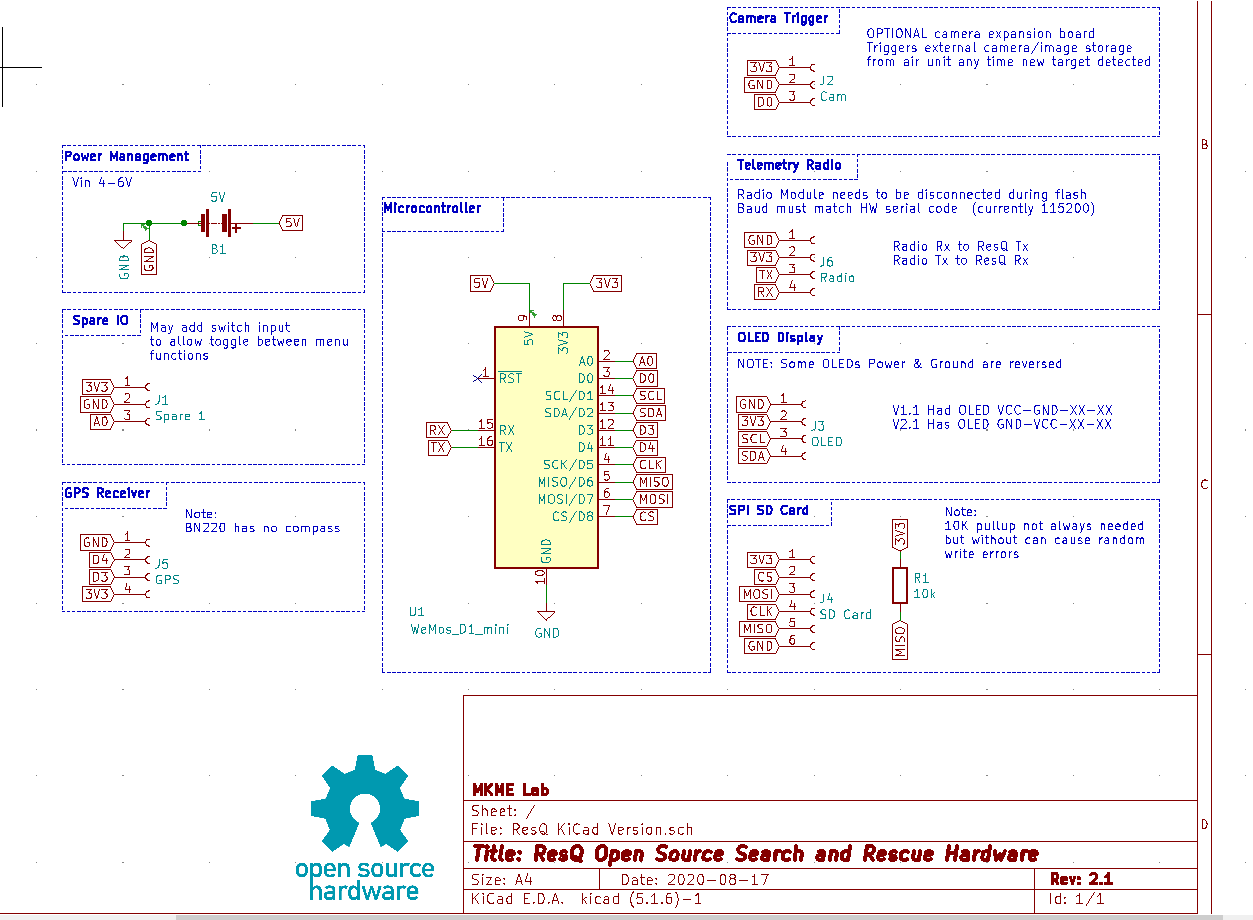
Photos/Schematic with Cam interface .PNG
