MKme/ResQ/Photos/Sentry/A5191535-75EC-4C00-8866-596DB6ED8DAF.jpg

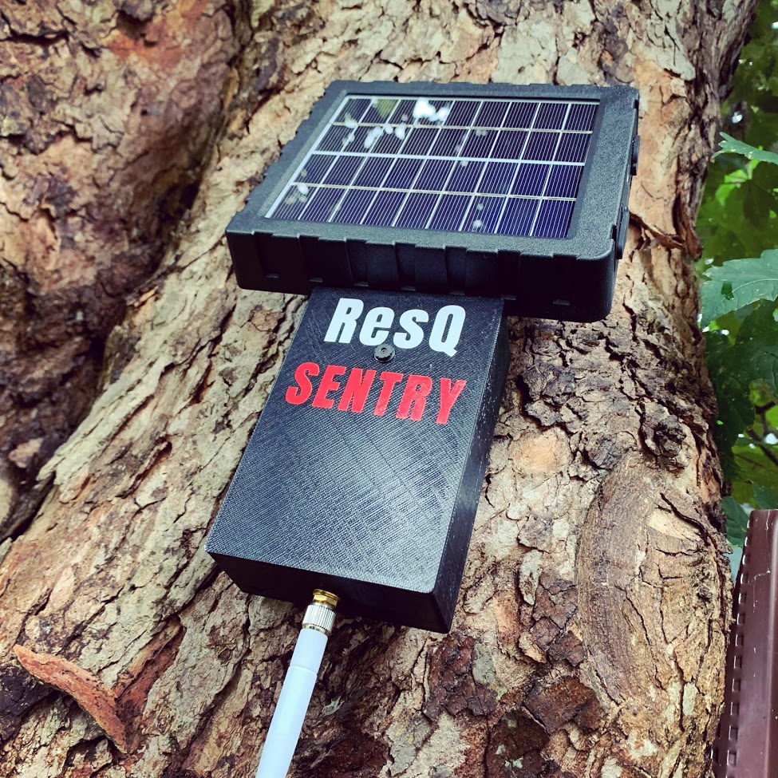
Photos/Sentry/A5191535-75EC-4C00-8866-596DB6ED8DAF.jpg
