MKme/ResQ/Photos/Sentry/CURA .JPG

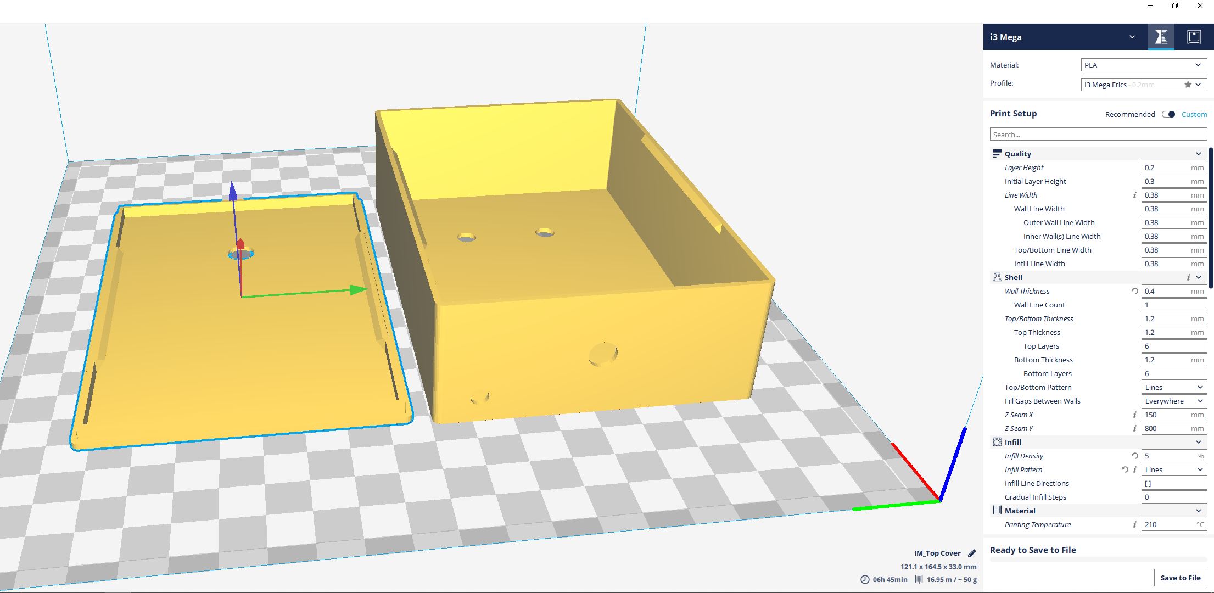
Photos/Sentry/CURA .JPG
