MKme/ResQ/Photos/Sentry/IMG_1101.jpg

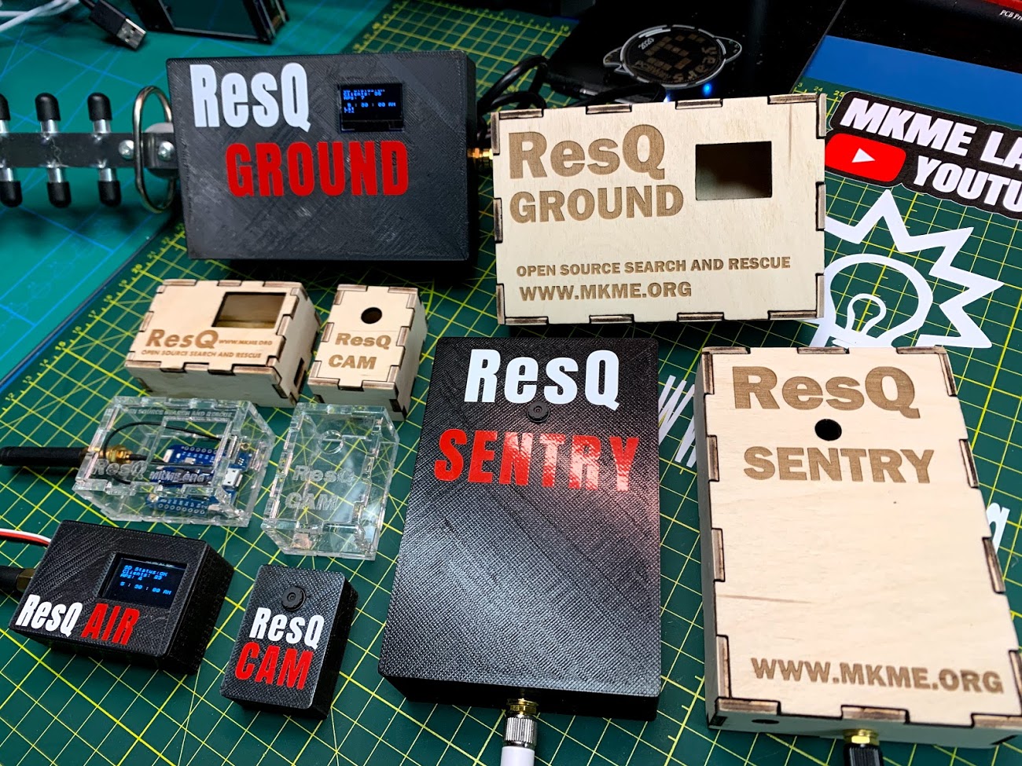
Photos/Sentry/IMG_1101.jpg
