MKme/ResQ/Photos/Sentry/IMG_1105.jpg

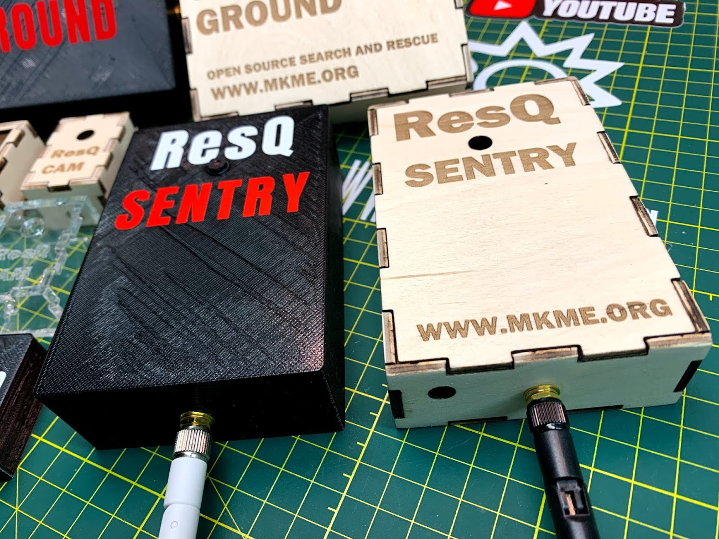
Photos/Sentry/IMG_1105.jpg
