MKme/ResQ/Photos/Sentry/IMG_1106.jpg

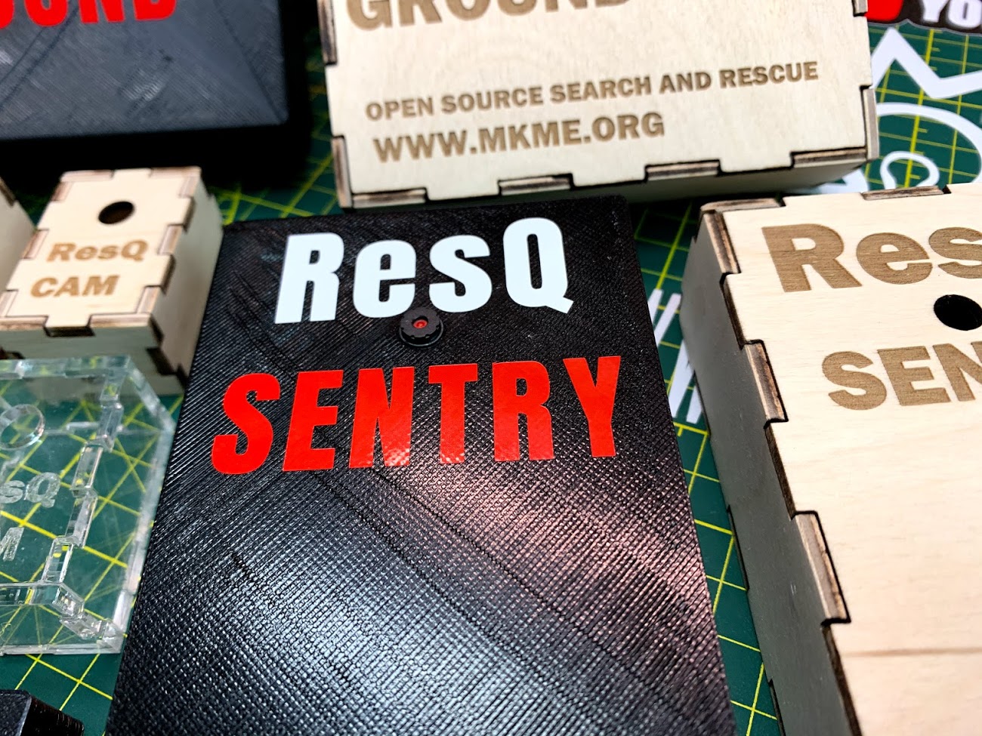
Photos/Sentry/IMG_1106.jpg
