MKme/ResQ/Photos/Sentry/IMG_1112.jpg

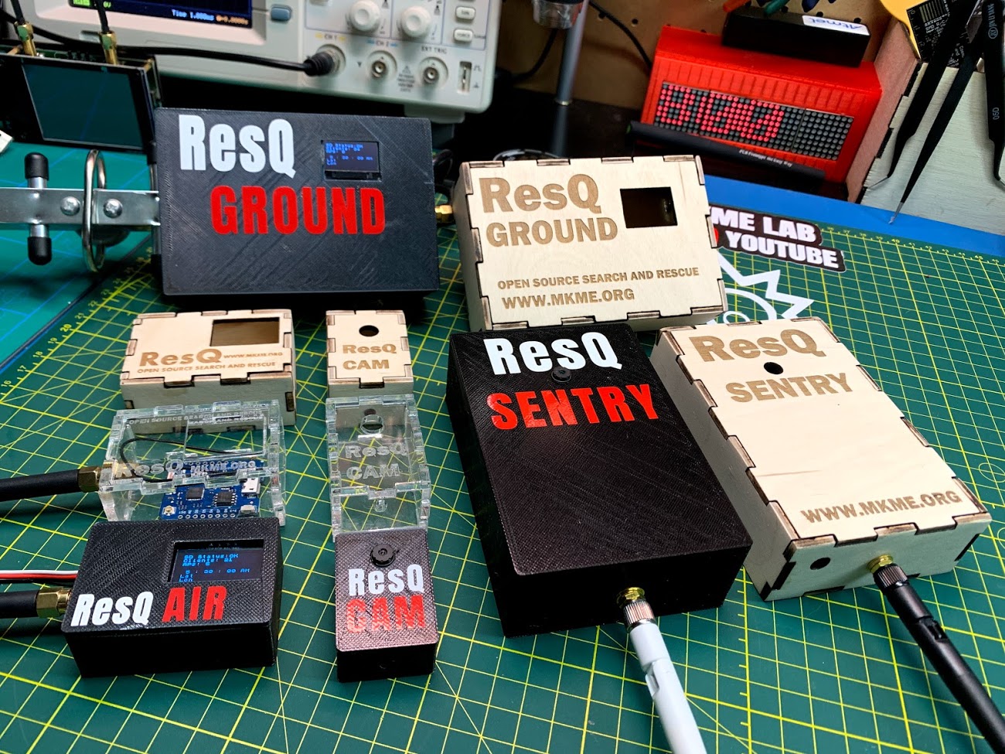
Photos/Sentry/IMG_1112.jpg
