MKme/ResQ/Photos/Sentry/IMG_1219.jpg

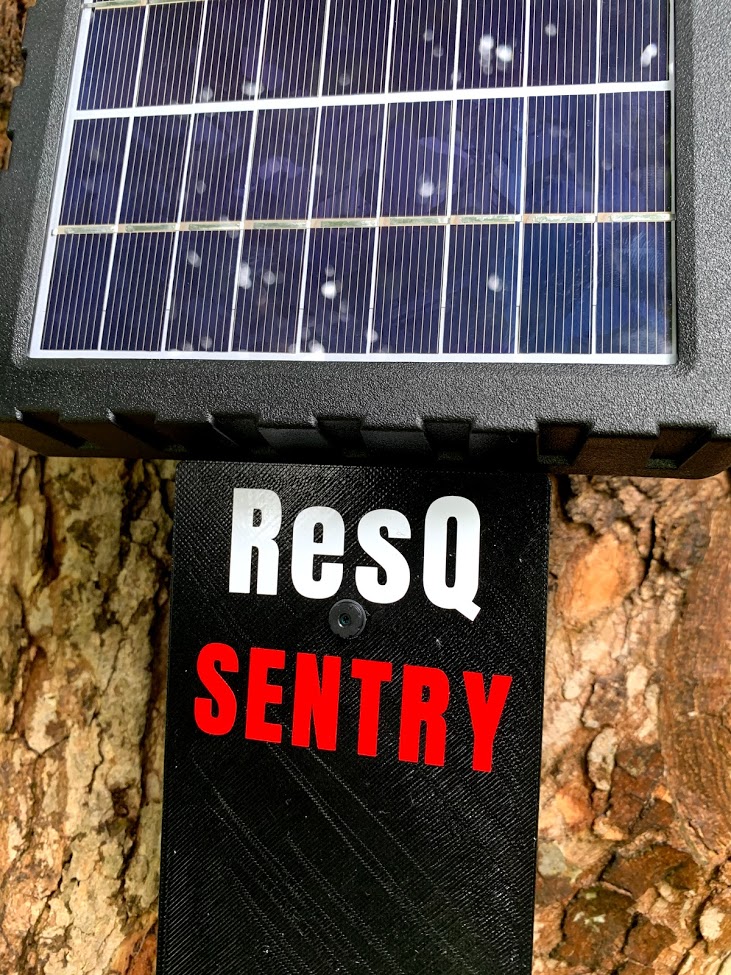
Photos/Sentry/IMG_1219.jpg
