MKme/ResQ/Photos/Sentry/IMG_1227.jpg

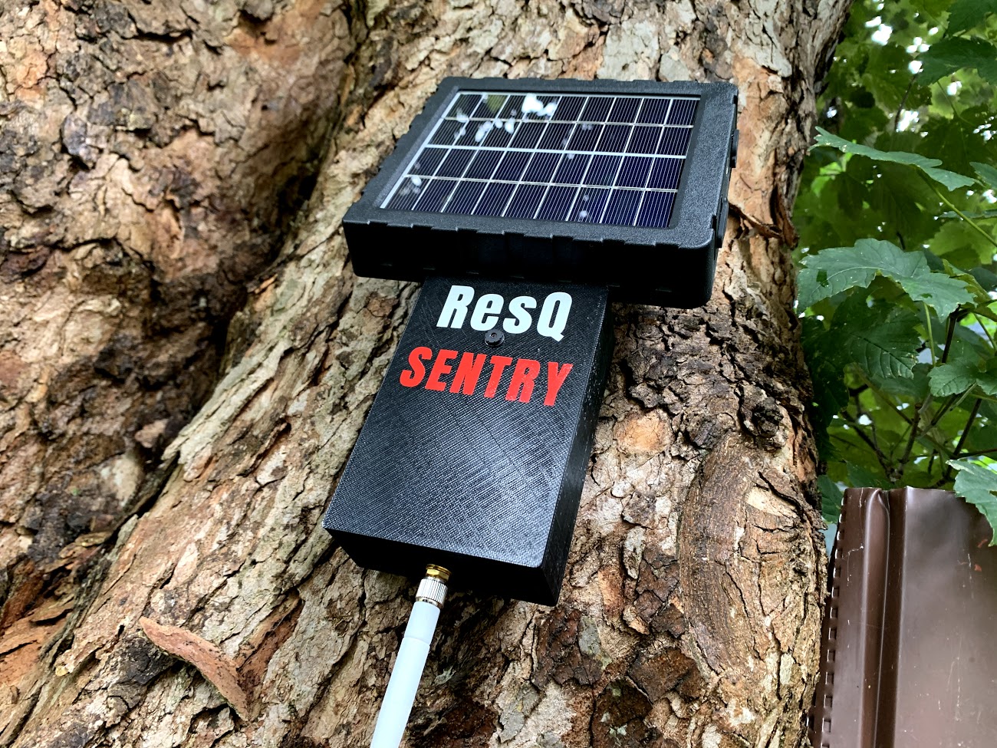
Photos/Sentry/IMG_1227.jpg
