MKme/ResQ/Photos/Sentry/Sentry F360e.JPG

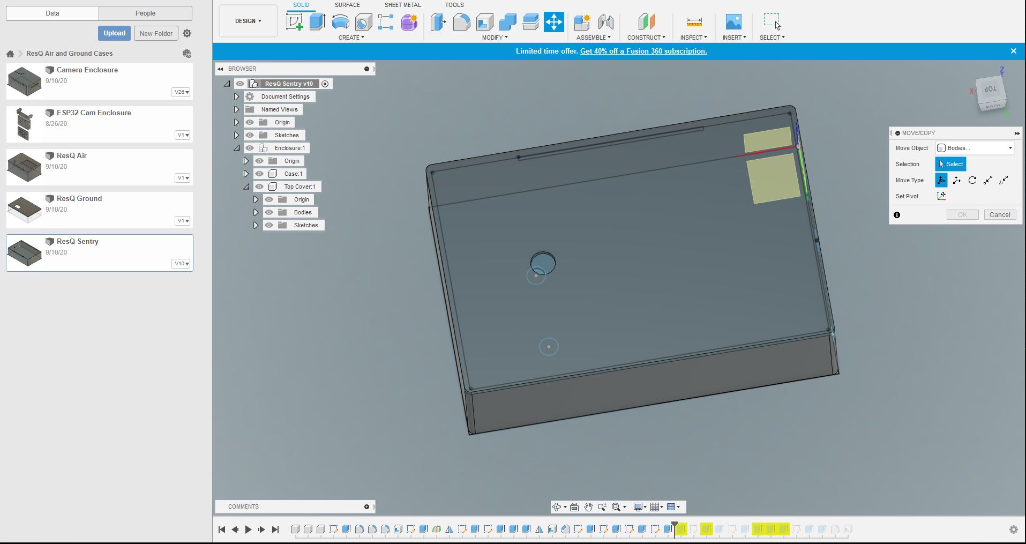
Photos/Sentry/Sentry F360e.JPG
