MKme/ResQ/Photos/Talon.jpg

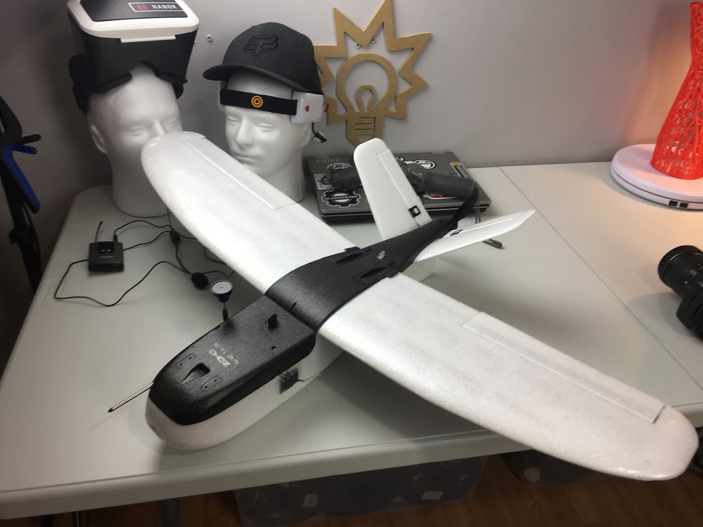
Photos/Talon.jpg
