MKme/ResQ/Photos/Wing1.jpg

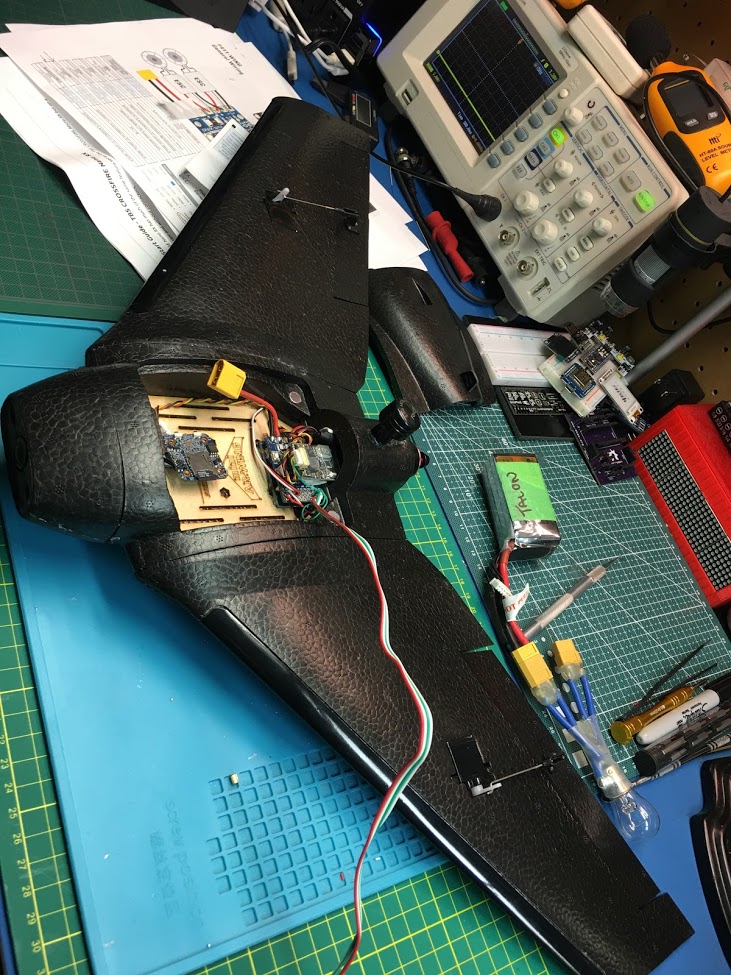
Photos/Wing1.jpg
