MKme/ResQ/Photos/Wing2.jpg

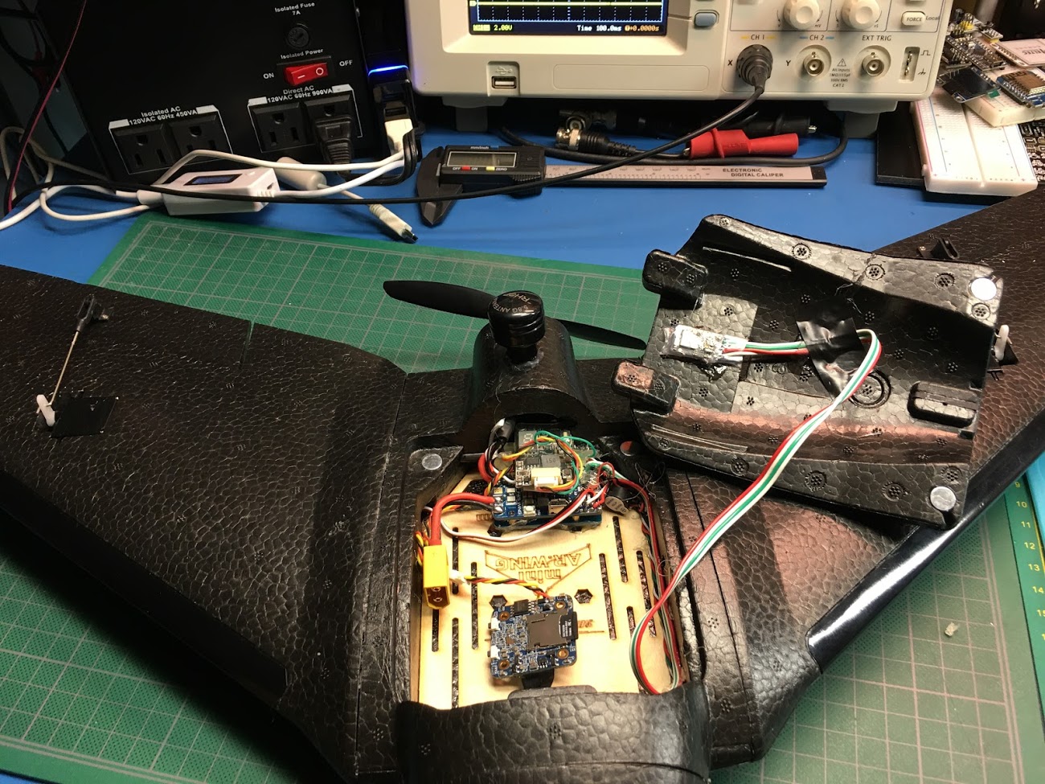
Photos/Wing2.jpg
