MKme/ResQ/Photos/YAGI2.JPG

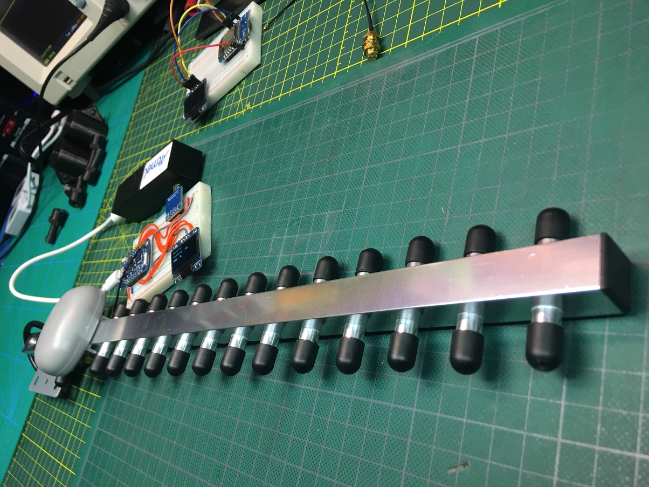
Photos/YAGI2.JPG
