MKme/ResQ/Photos/yagi.jpg

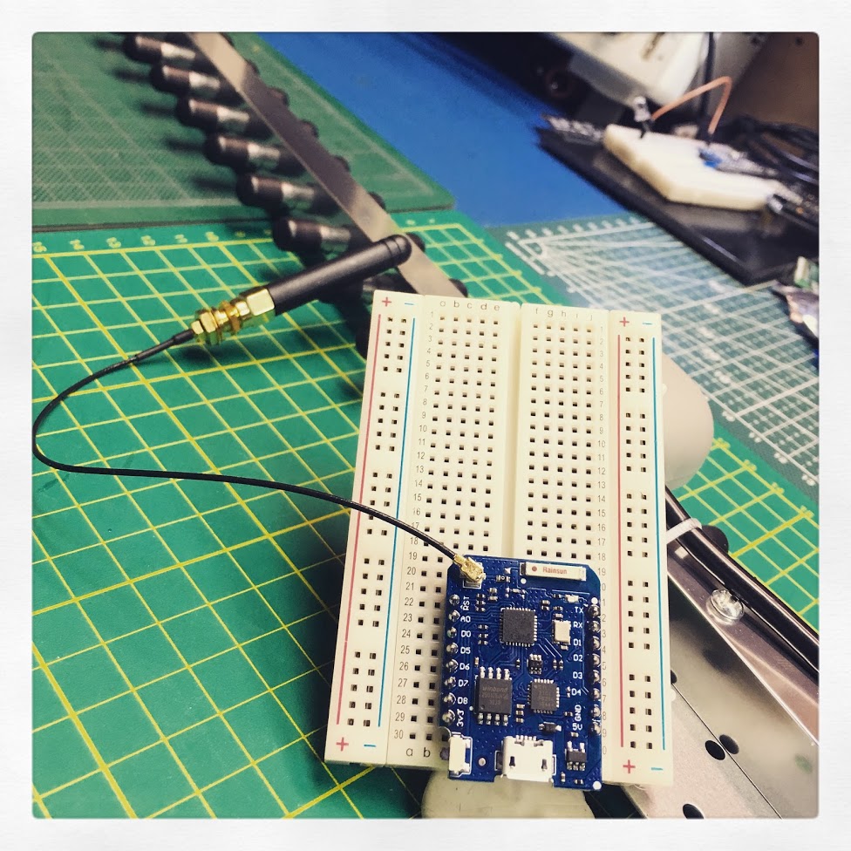
Photos/yagi.jpg
