MKme/ResQ/Photos/YouTube Playlist.PNG

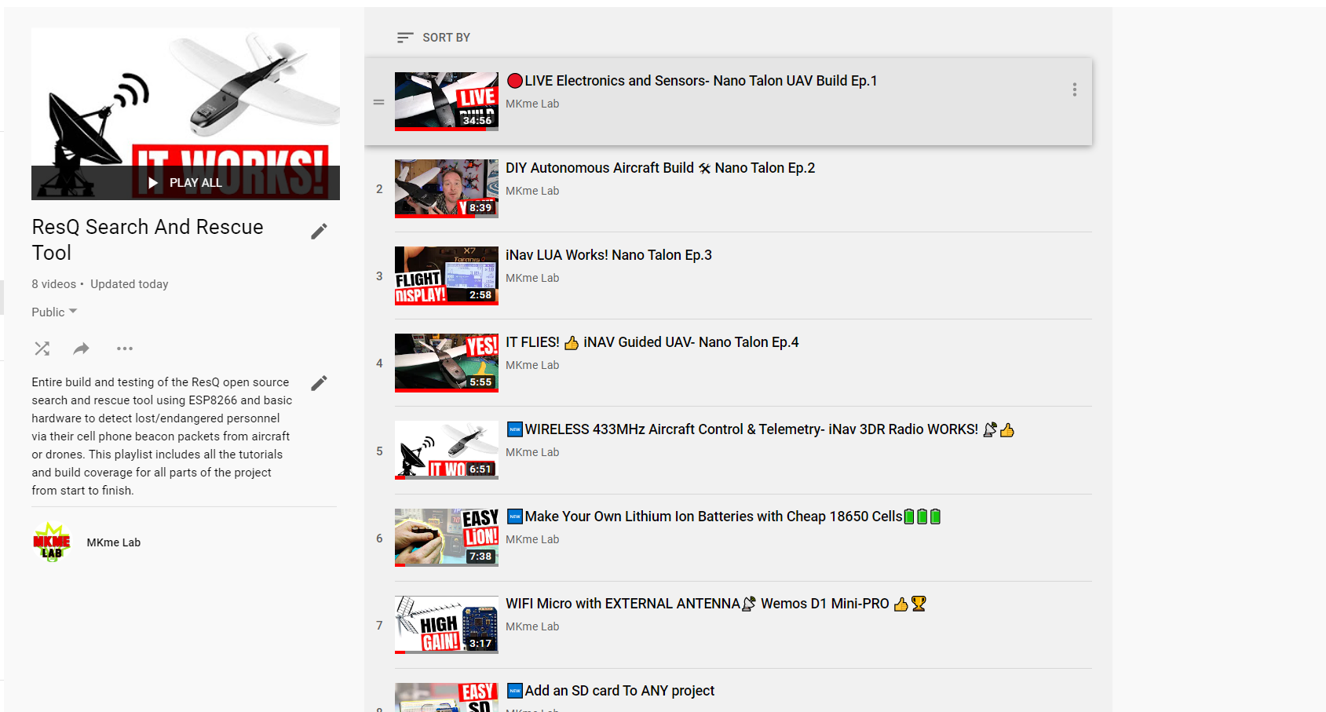
Photos/YouTube Playlist.PNG
