MKme/ResQ/Reference Materials/Flow and Reference Diagrams/Overview With Sentry/NewOverview Inc Sentry.png

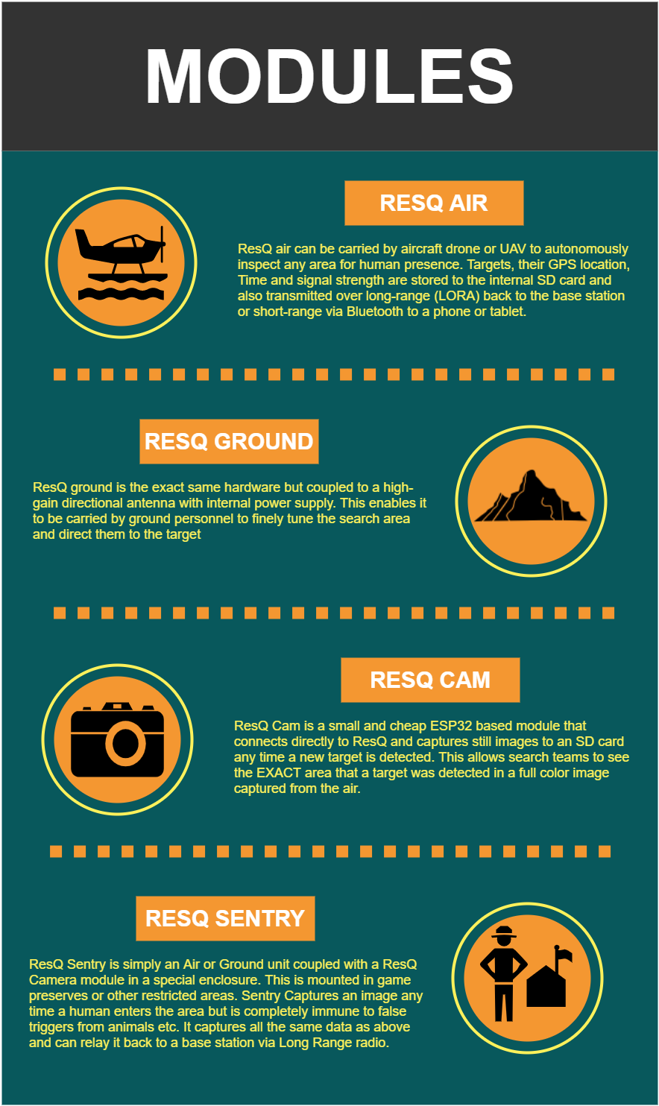
Reference Materials/Flow and Reference Diagrams/Overview With Sentry/NewOverview Inc Sentry.png
