MKme/ResQ/Aircraft Files  and Design Ref/CAD Files Parts/Matek_F722w_holder/images/fa11cc68e6ec0d6c2703b6664aab14d6_preview_featured.jpg

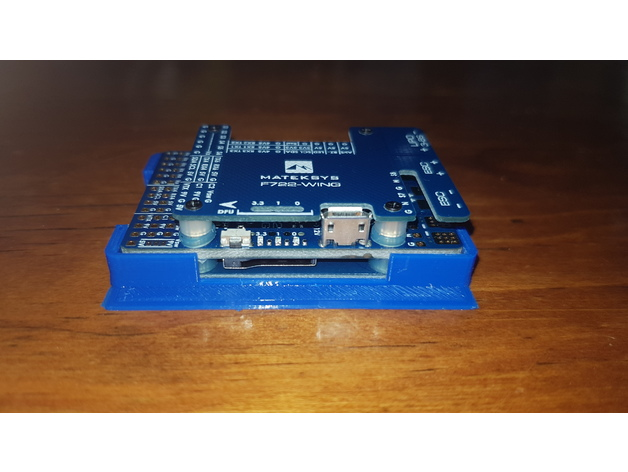
Aircraft Files and Design Ref/CAD Files Parts/Matek_F722w_holder/images/fa11cc68e6ec0d6c2703b6664aab14d6_preview_featured.jpg
