MKme/ResQ/Aircraft Files  and Design Ref/CAD Files Parts/Nano_Talon_AKK_X2_external_mount/images/4fcdb4ef0a7ed6785071d1192c244c25_preview_featured.jpg

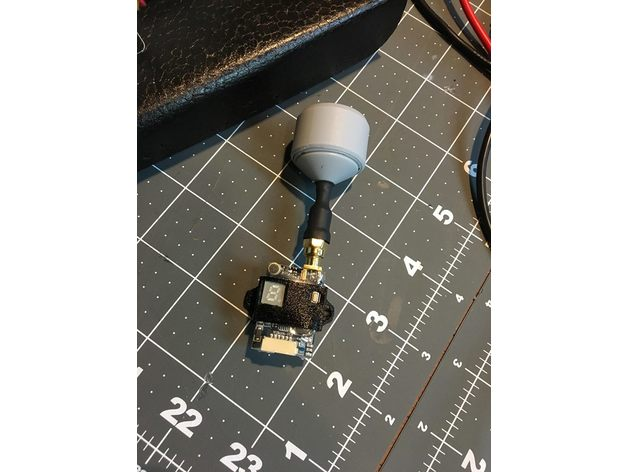
Aircraft Files and Design Ref/CAD Files Parts/Nano_Talon_AKK_X2_external_mount/images/4fcdb4ef0a7ed6785071d1192c244c25_preview_featured.jpg
