MKme/ResQ/Aircraft Files  and Design Ref/CAD Files Parts/Nano_Talon_AKK_X2_external_mount/images/9c2bdbc9a15a0b9ab6f8eb7a28063c87_preview_featured.jpg

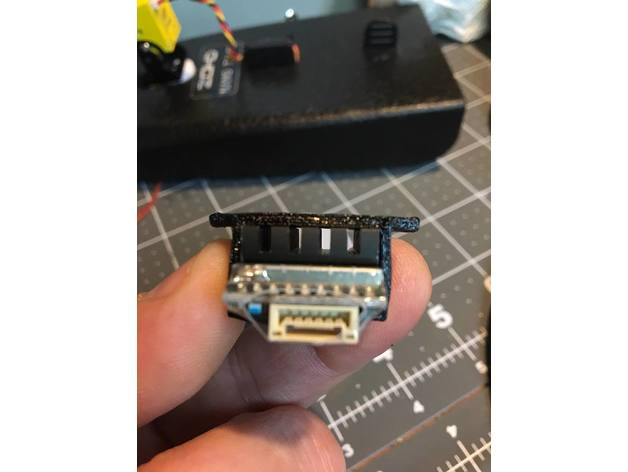
Aircraft Files and Design Ref/CAD Files Parts/Nano_Talon_AKK_X2_external_mount/images/9c2bdbc9a15a0b9ab6f8eb7a28063c87_preview_featured.jpg
