MKme/ResQ/Aircraft Files  and Design Ref/CAD Files Parts/Nano_Talon_AKK_X2_external_mount/images/60170ed32bee4dd302b5a4c103752771_preview_featured.jpg

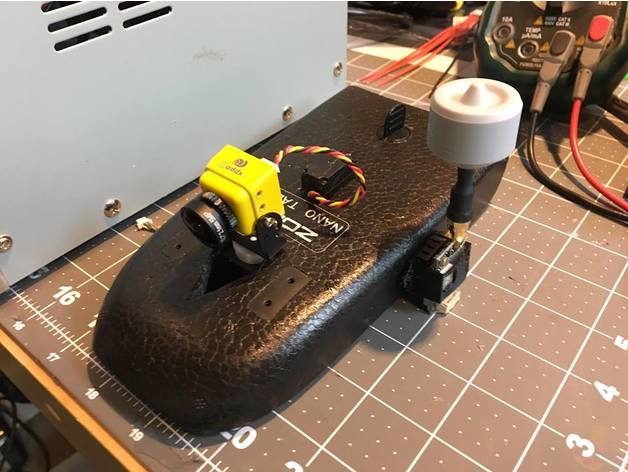
Aircraft Files and Design Ref/CAD Files Parts/Nano_Talon_AKK_X2_external_mount/images/60170ed32bee4dd302b5a4c103752771_preview_featured.jpg
