MKme/ResQ/Aircraft Files  and Design Ref/CAD Files Parts/Nano_Talon_Bottom_Hatch/images/e09a0e4e960d7c41600d8d0c165cd4d4_preview_featured.jpg

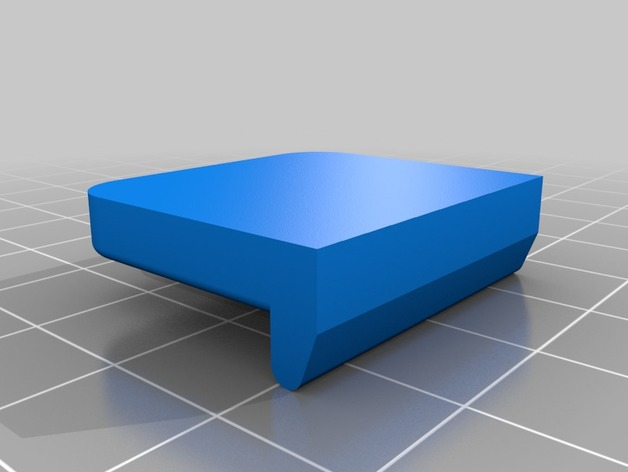
Aircraft Files and Design Ref/CAD Files Parts/Nano_Talon_Bottom_Hatch/images/e09a0e4e960d7c41600d8d0c165cd4d4_preview_featured.jpg
