MKme/ResQ/Reference Materials/Parts datasheets etc/Future ESP option- Use this with single custom board when it is made.jpg

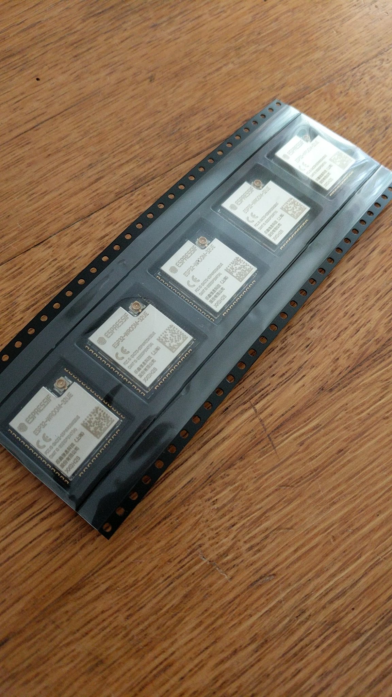
Reference Materials/Parts datasheets etc/Future ESP option- Use this with single custom board when it is made.jpg
