MKme/ResQ/Reference Materials/ResQ Cam/Z Cam Reference Files/Intro 01.jpg

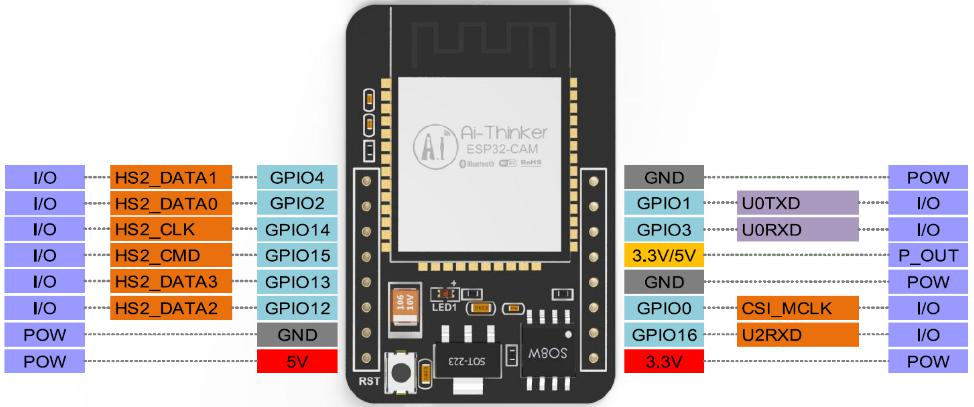
Reference Materials/ResQ Cam/Z Cam Reference Files/Intro 01.jpg
