MKme/ResQ/Reference Materials/ResQ Cam/Z Cam Reference Files/yv050peu22p21.webp

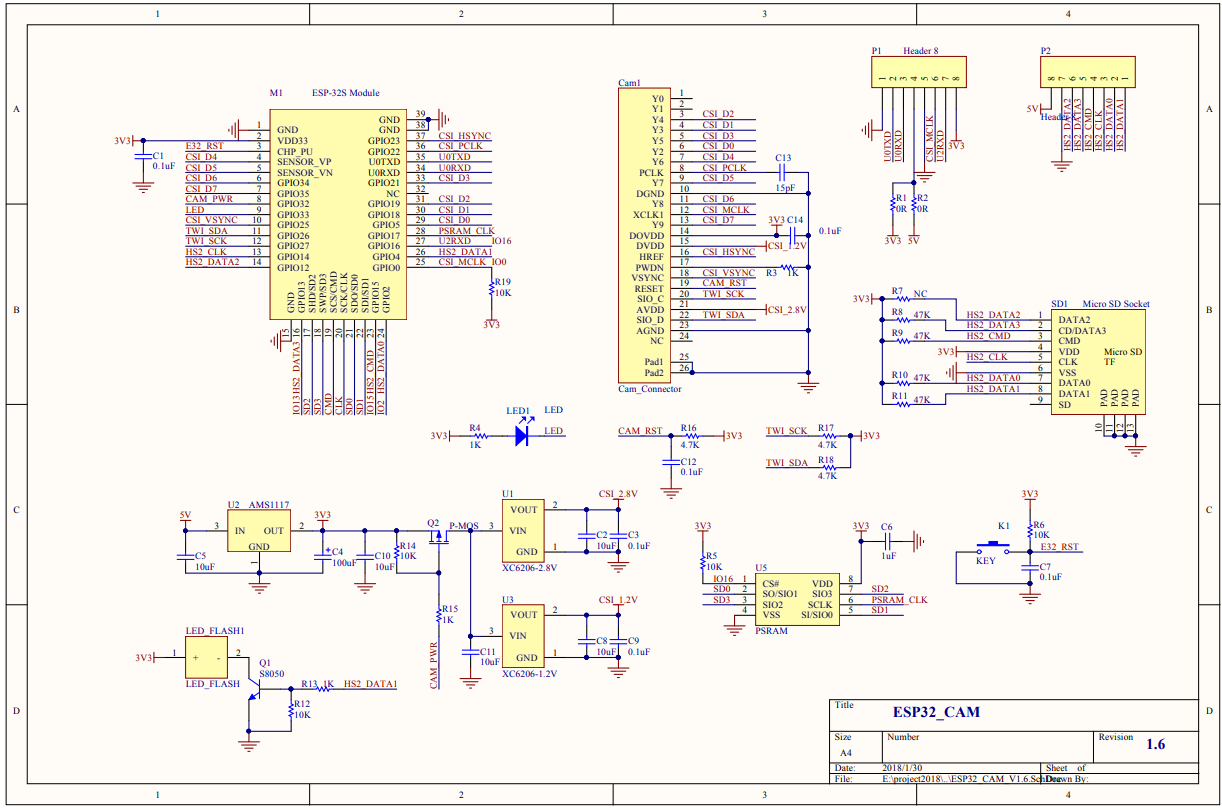
Reference Materials/ResQ Cam/Z Cam Reference Files/yv050peu22p21.webp
