MKme/ResQ/Aircraft Files  and Design Ref/CAD Files Parts/Nano_Talon_Bottom_Hatch/files/Hatch2.stl

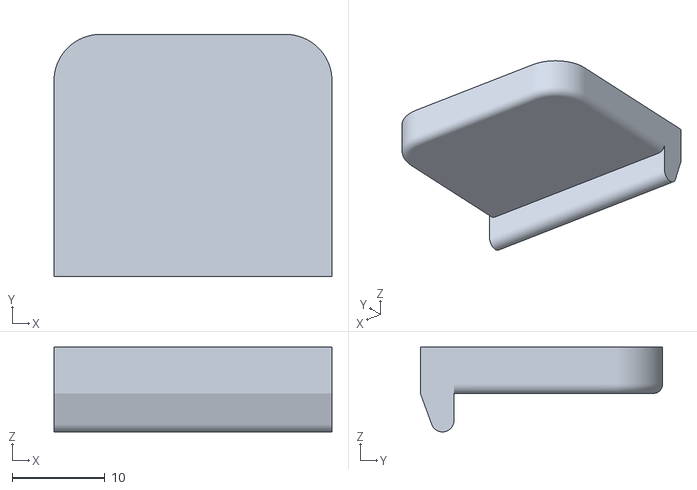
[picture p167: CAD file, 2020-08-03]
Aircraft Files and Design Ref/CAD Files Parts/Nano_Talon_Bottom_Hatch/files/Hatch2.stl
30.0 x 26.1 x 9.16
