MKme/ResQ/Enclsoure CAD Files/3D Models/Air Unit Enclosure/V1.3 Abandoned/Body1.stl

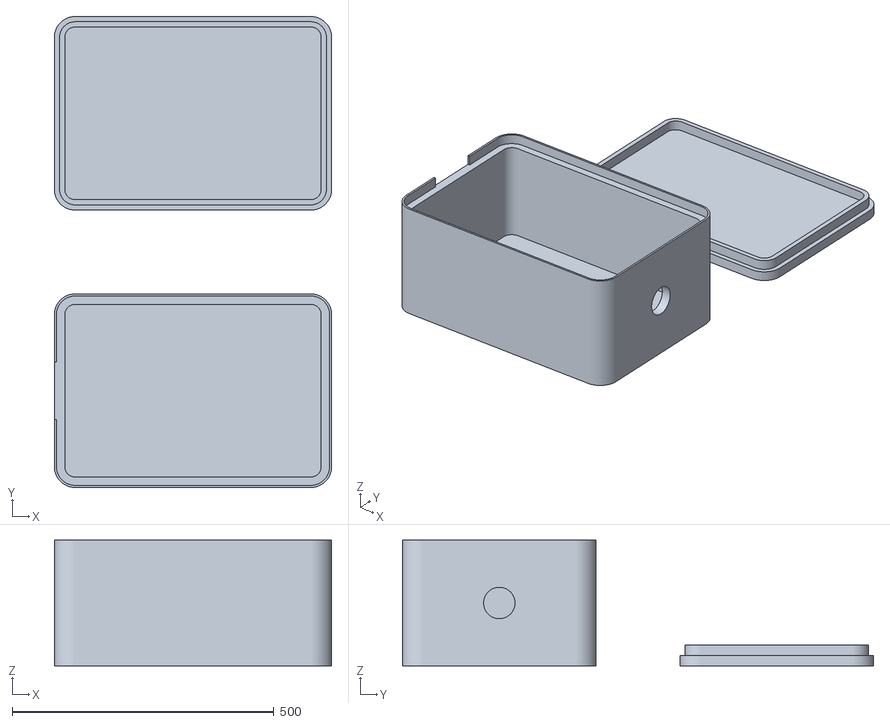
[picture p168: CAD file, 2020-08-05]
Enclsoure CAD Files/3D Models/Air Unit Enclosure/V1.3 Abandoned/Body1.stl
530.0 x 900.0 x 240.0
