MKme/ResQ/Enclsoure CAD Files/3D Models/Air Unit Enclosure/V1.4 Fusion 360/Top Cover.stl

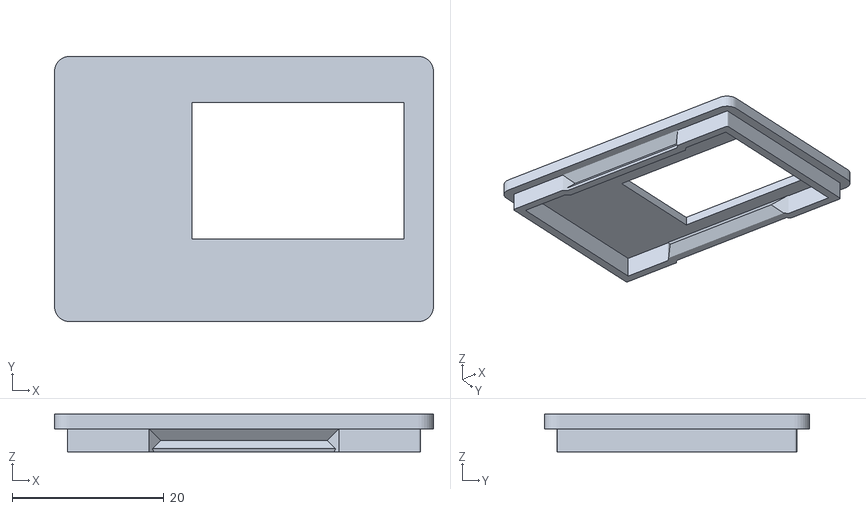
[picture p169: CAD file, 2020-08-05]
Enclsoure CAD Files/3D Models/Air Unit Enclosure/V1.4 Fusion 360/Top Cover.stl
50.0 x 35.0 x 5.00
