MKme/ResQ/Enclsoure CAD Files/3D Models/Air Unit Enclosure/V1.6 Longer and wider yet/Top Cover.stl

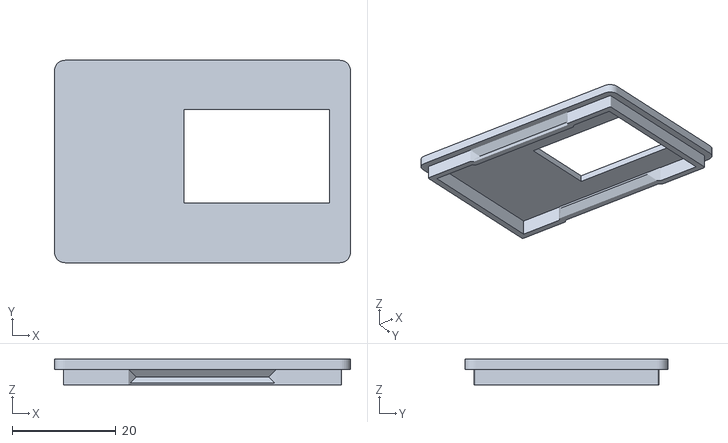
[picture p170: CAD file, 2020-08-08]
Enclsoure CAD Files/3D Models/Air Unit Enclosure/V1.6 Longer and wider yet/Top Cover.stl
57.0 x 39.0 x 5.00
