MKme/ResQ/Enclsoure CAD Files/3D Models/Ground Unit Enclosure/V1.1/My+Customized+Parametric+Project+Box/files/snap_box_both20200601-60-kt0mq8.stl

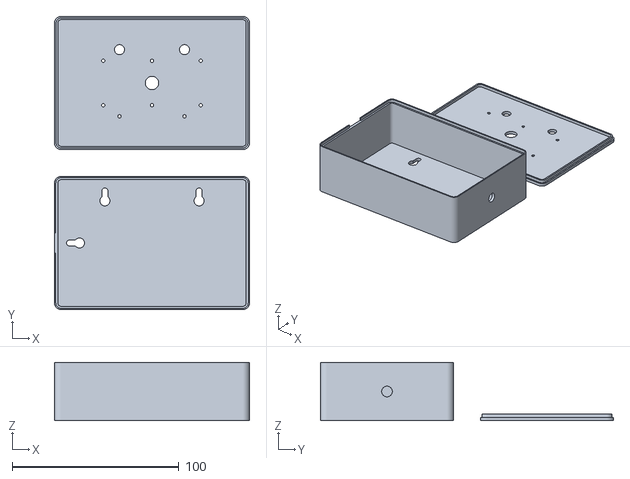
[picture p171: CAD file, 2020-06-01]
Enclsoure CAD Files/3D Models/Ground Unit Enclosure/V1.1/My+Customized+Parametric+Project+Box/files/snap_box_both20200601-60-kt0mq8.stl
117.0 x 176.0 x 35.0
