MKme/ResQ/Enclsoure CAD Files/ResQ Sentry Enclosure/3D/ResQ Sentry v10.step

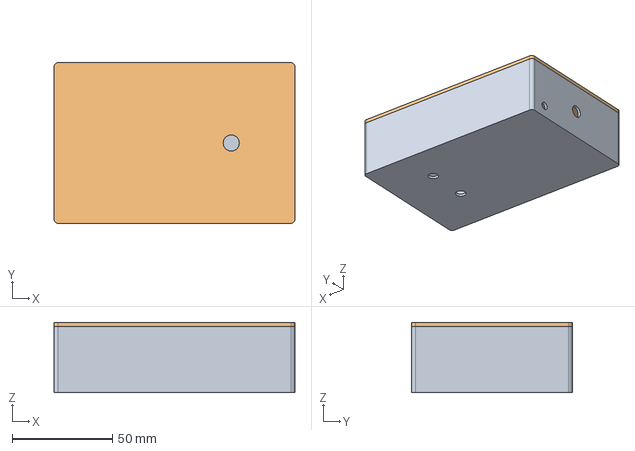
[picture p173: CAD file, 2020-09-24]
Enclsoure CAD Files/ResQ Sentry Enclosure/3D/ResQ Sentry v10.step
120.0 x 80.0 x 35.0 mm
Case
Top Cover
