MKme/ResQ/Enclsoure CAD Files/3D Models/Air Unit Enclosure/V1.6 Longer and wider yet/Case.stl

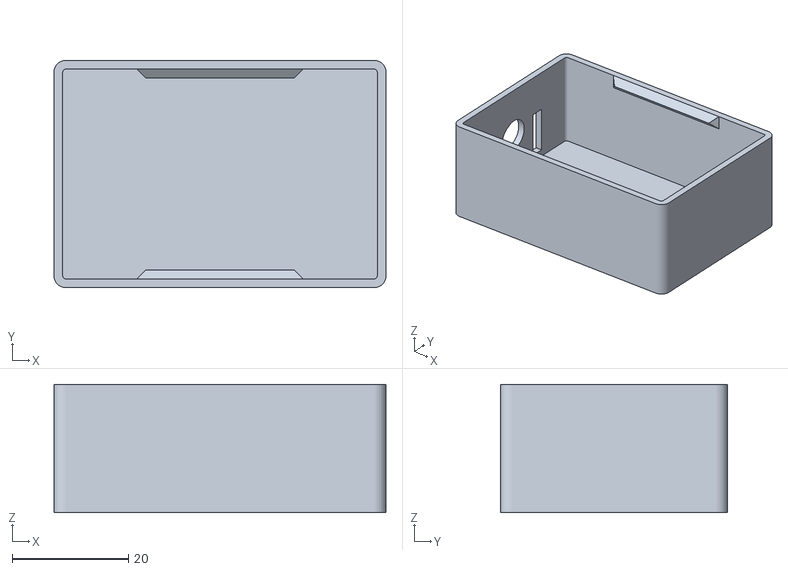
[picture p174: CAD file, 2020-08-06]
Enclsoure CAD Files/3D Models/Air Unit Enclosure/V1.6 Longer and wider yet/Case.stl
57.0 x 39.0 x 22.0
