MKme/ResQ/Enclsoure CAD Files/ResQ Camera Enclosures/3D/V1.1/Top Cover.stl

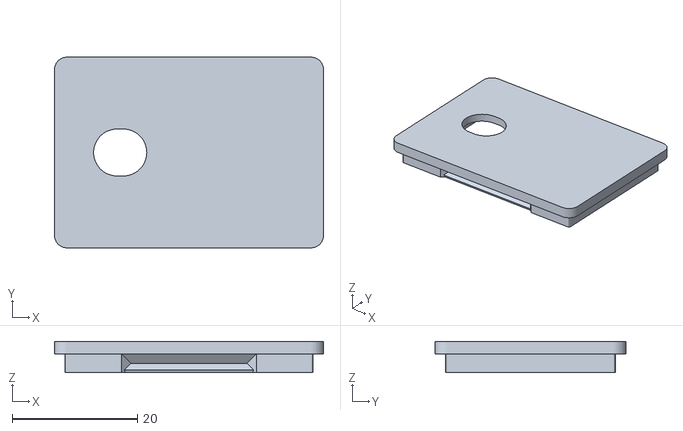
[picture p175: CAD file, 2020-09-13]
Enclsoure CAD Files/ResQ Camera Enclosures/3D/V1.1/Top Cover.stl
43.0 x 30.5 x 5.00
