MKme/ResQ/Enclsoure CAD Files/ResQ Sentry Enclosure/3D/Top Cover.stl

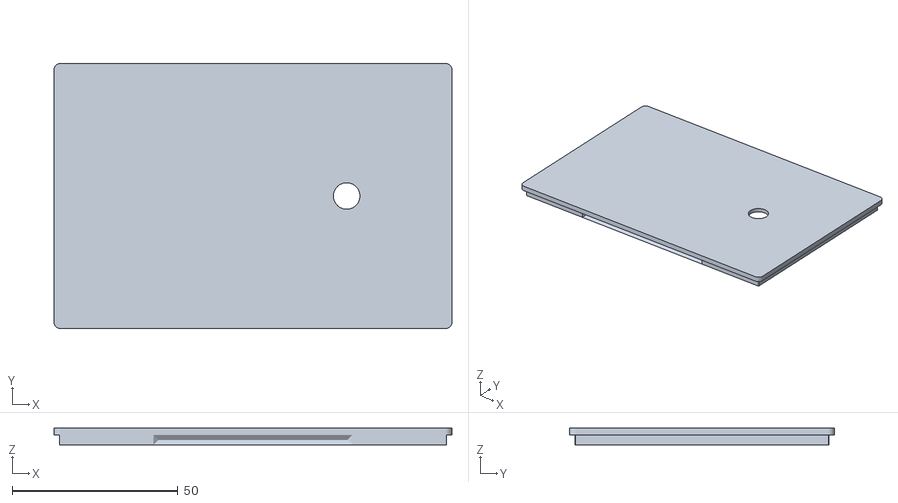
[picture p176: CAD file, 2020-09-24]
Enclsoure CAD Files/ResQ Sentry Enclosure/3D/Top Cover.stl
120.0 x 80.0 x 5.00
