MKme/ResQ/Photos/Bluetooth/Bluetooth InstructionsJPG.JPG

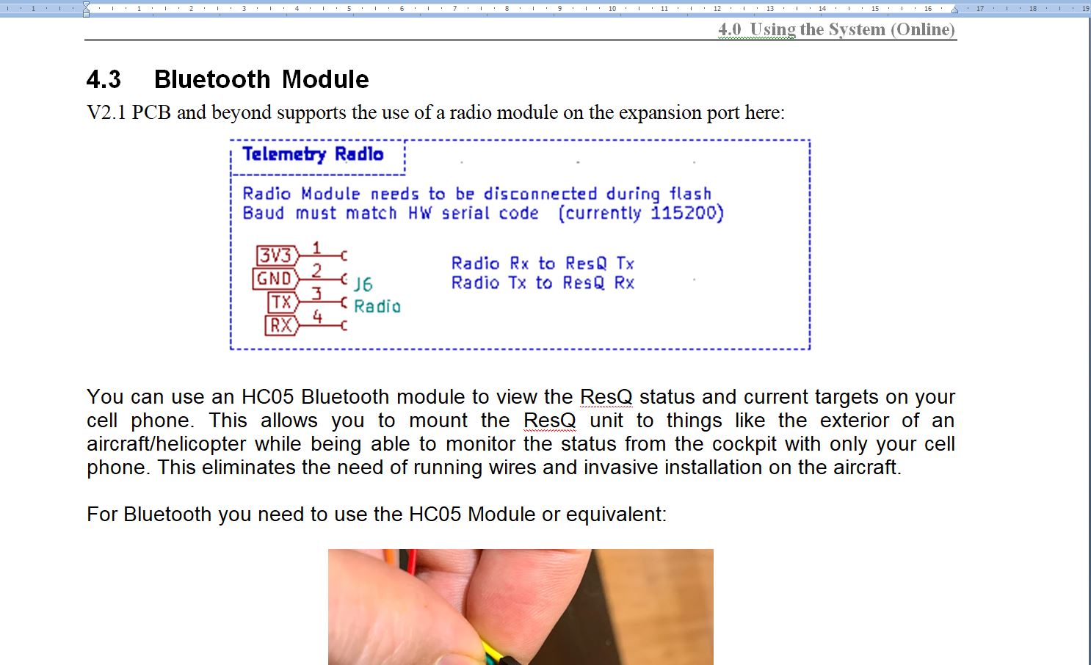
Photos/Bluetooth/Bluetooth InstructionsJPG.JPG
