MKme/ResQ/Photos/wingbuild2.jpg

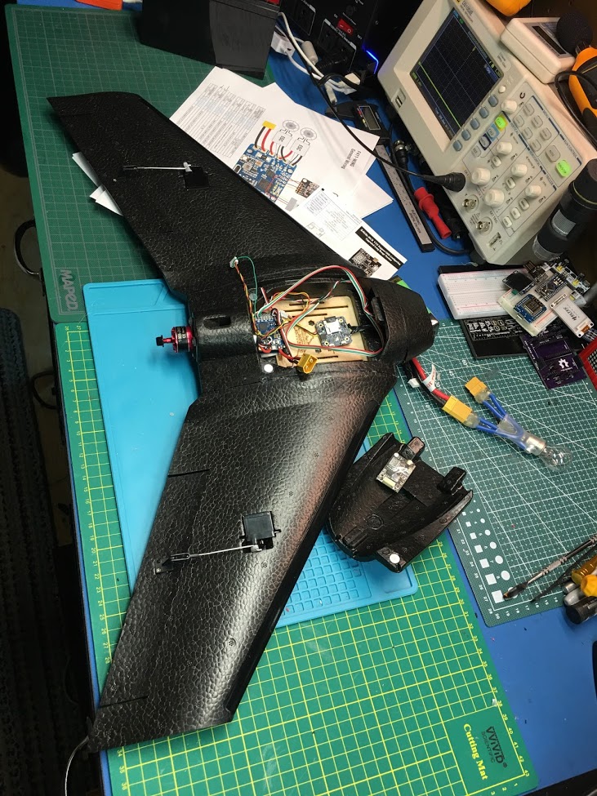
Photos/wingbuild2.jpg
