MKme/ResQ/Photos/Wingbuild.jpg

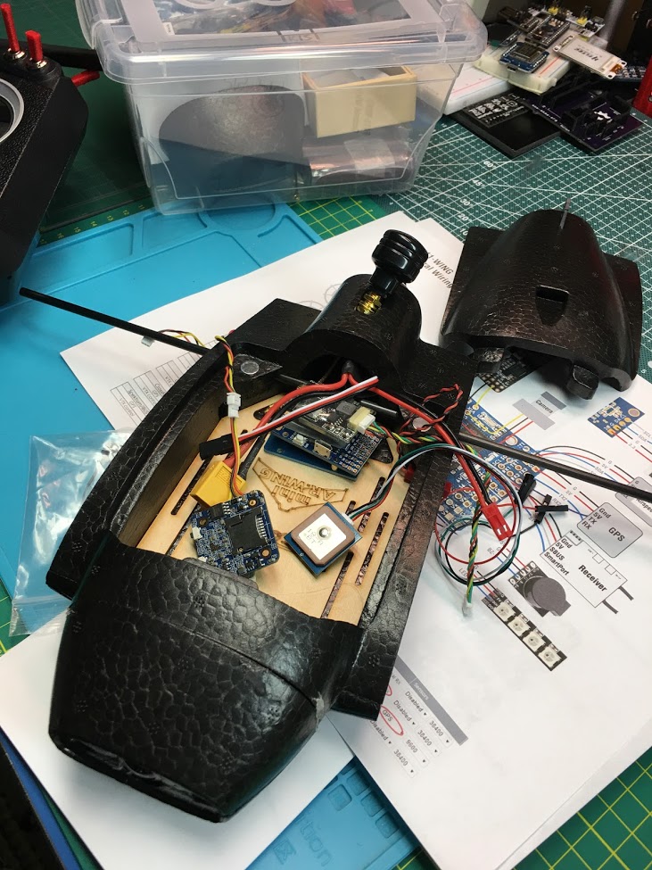
Photos/Wingbuild.jpg
