MKme/ResQ/Reference Materials/ResQ Cam/Z Cam Reference Files/ESP32-CAM-pinout-guide-gpios-pins-explained.webp

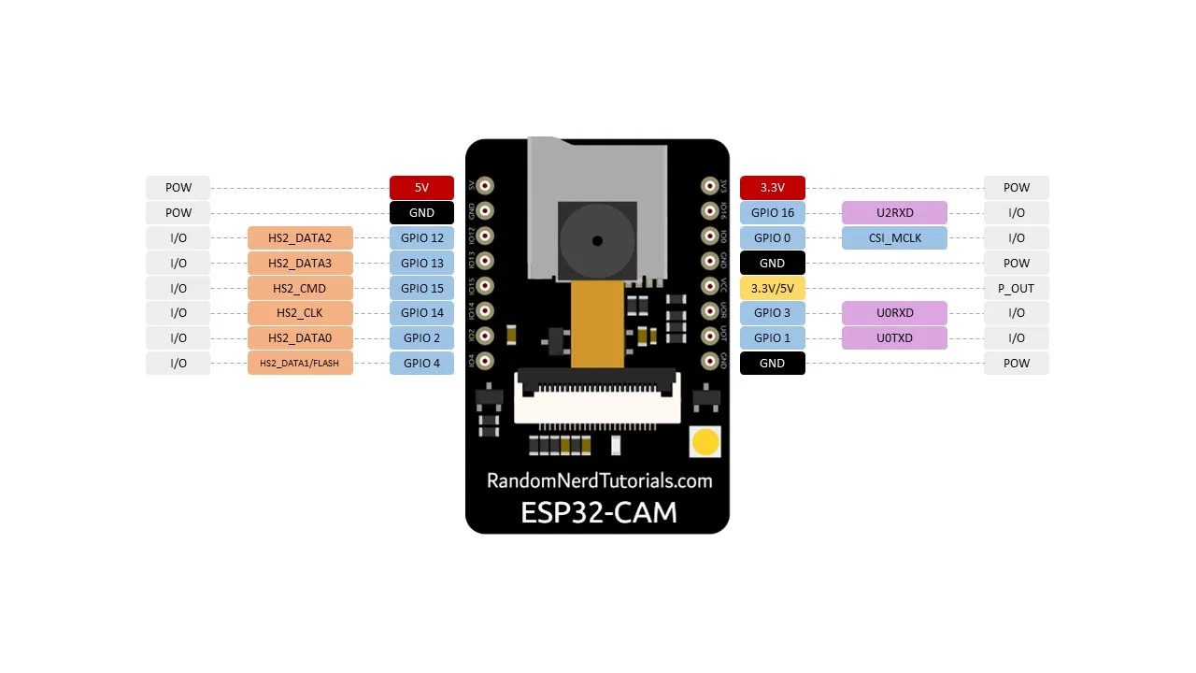
Reference Materials/ResQ Cam/Z Cam Reference Files/ESP32-CAM-pinout-guide-gpios-pins-explained.webp
