MKme/ResQ/Stickers and Artwork/ResQ Mountain Print Sticker/mountain .png

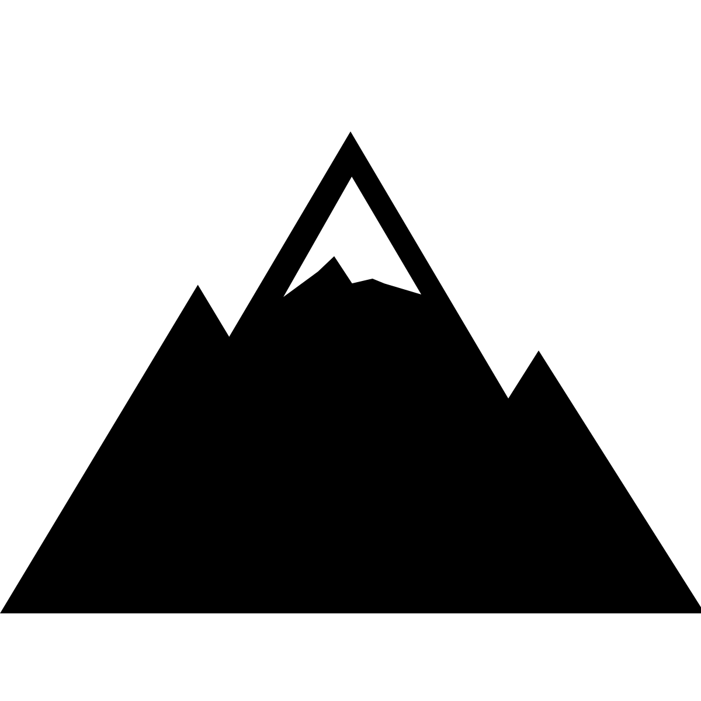
Stickers and Artwork/ResQ Mountain Print Sticker/mountain .png
