MKme/ResQ/Stickers and Artwork/ResQ Mountain Print Sticker/ResQ .png

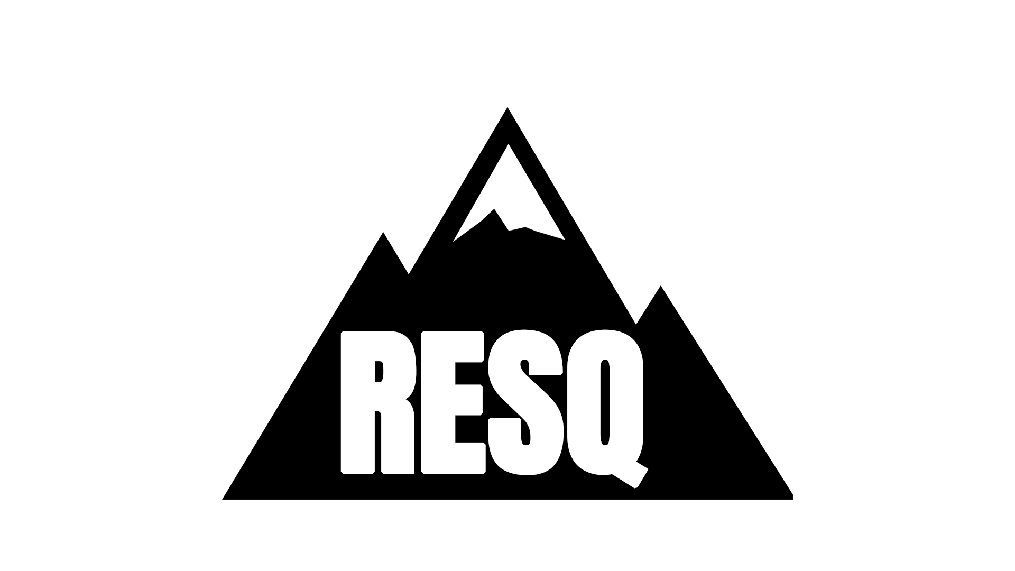
Stickers and Artwork/ResQ Mountain Print Sticker/ResQ .png
