MKme/ResQ/Photos/Antenna Testing/IMG_0358.jpg

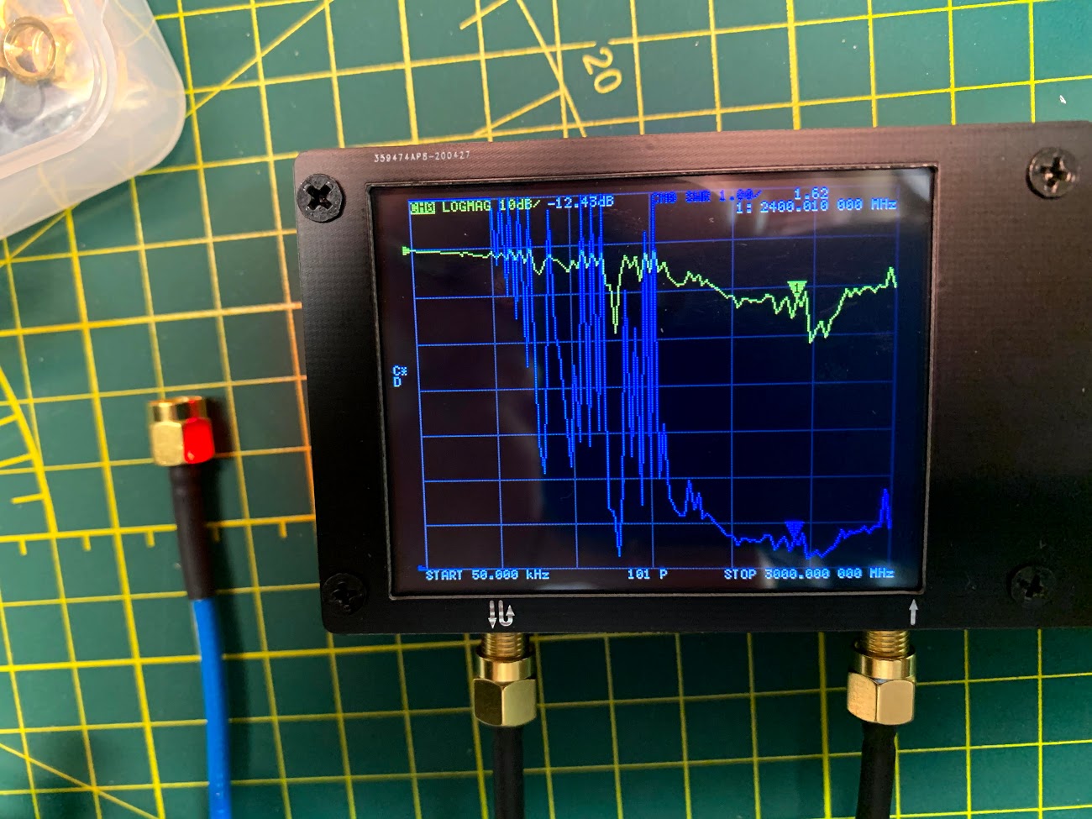
Photos/Antenna Testing/IMG_0358.jpg
