MKme/ResQ/Photos/Antenna Testing/IMG_0359.jpg

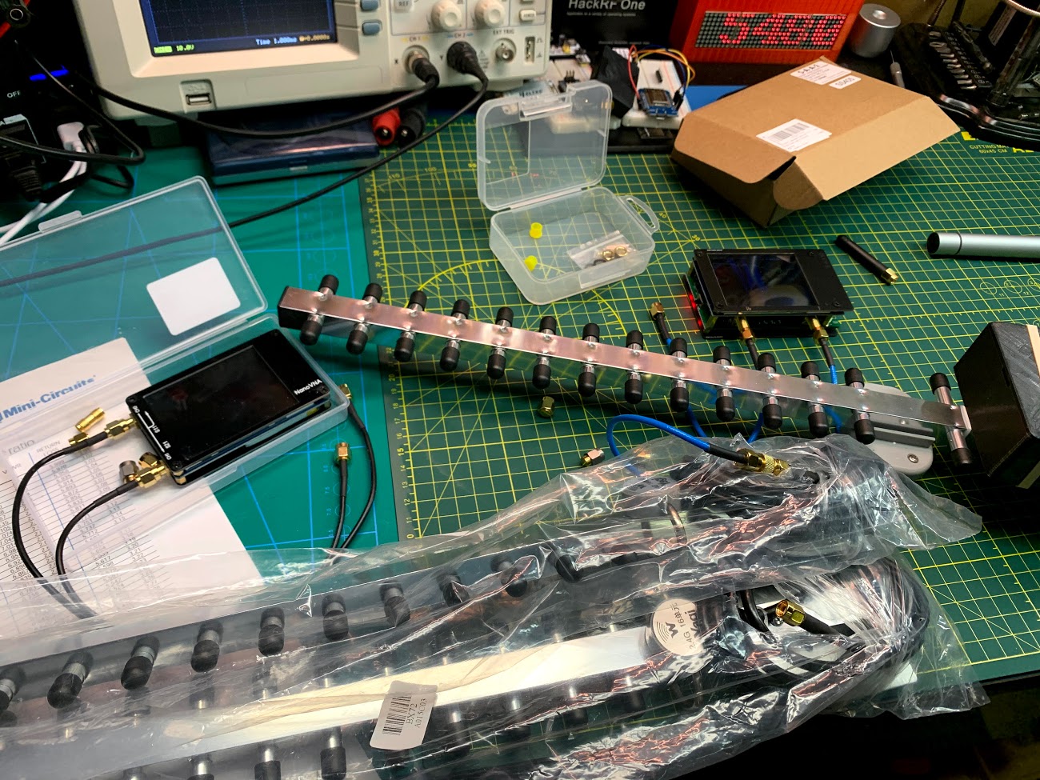
Photos/Antenna Testing/IMG_0359.jpg
