MKme/ResQ/Photos/Antenna Testing/IMG_0361.jpg

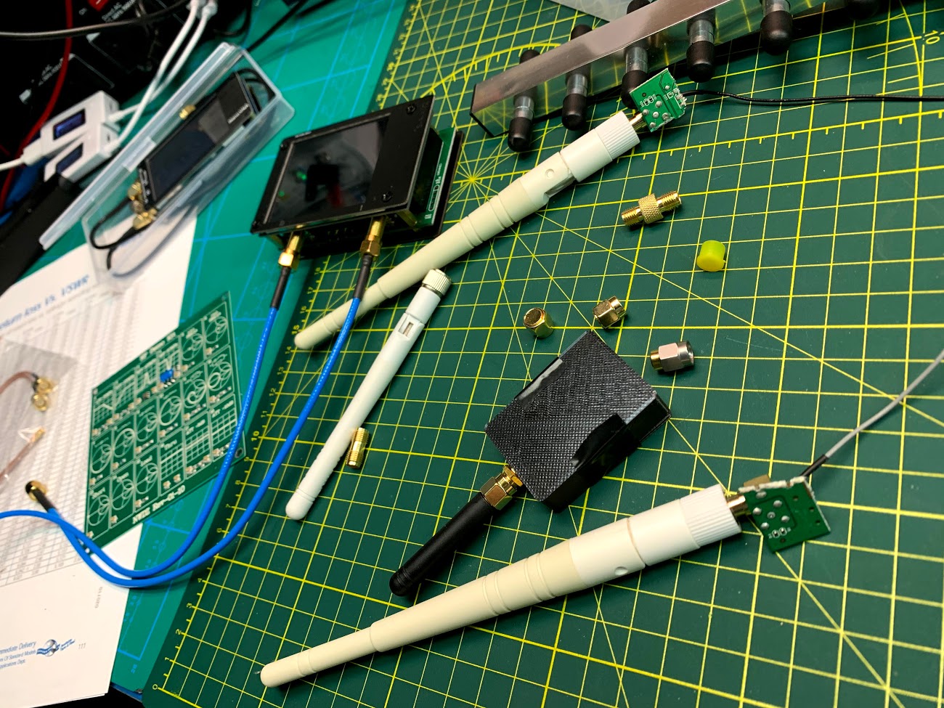
Photos/Antenna Testing/IMG_0361.jpg
