MKme/ResQ/Photos/Antenna Testing/IMG_0362.jpg

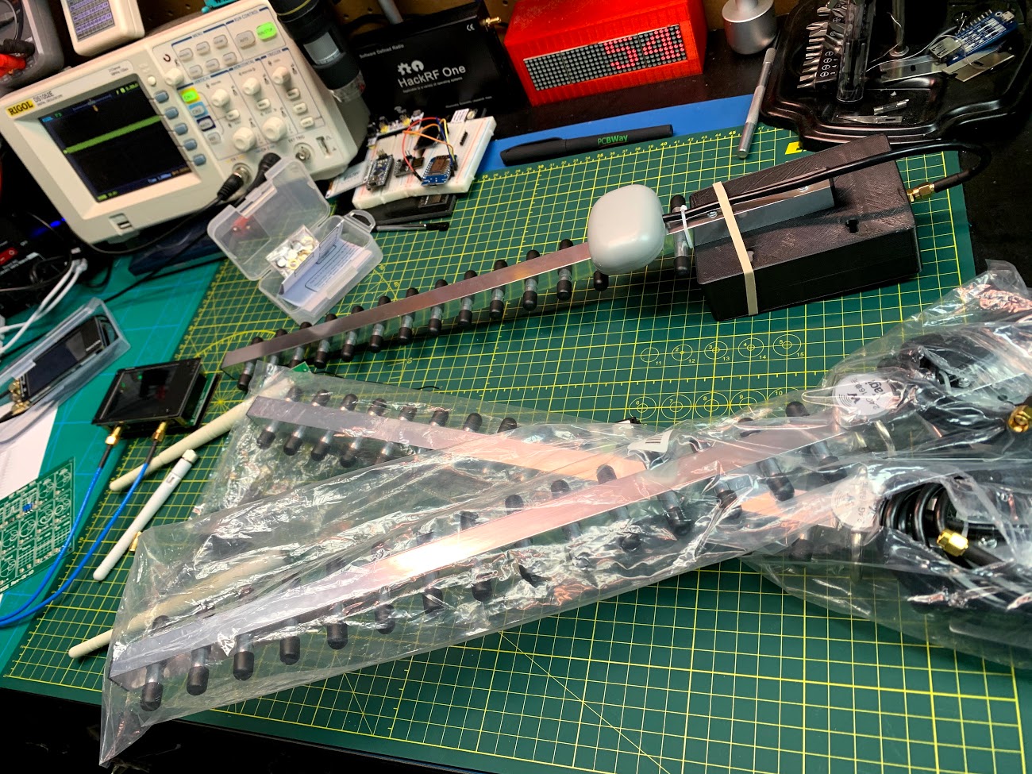
Photos/Antenna Testing/IMG_0362.jpg
