MKme/ResQ/Photos/GPSBreadboardTest.jpg

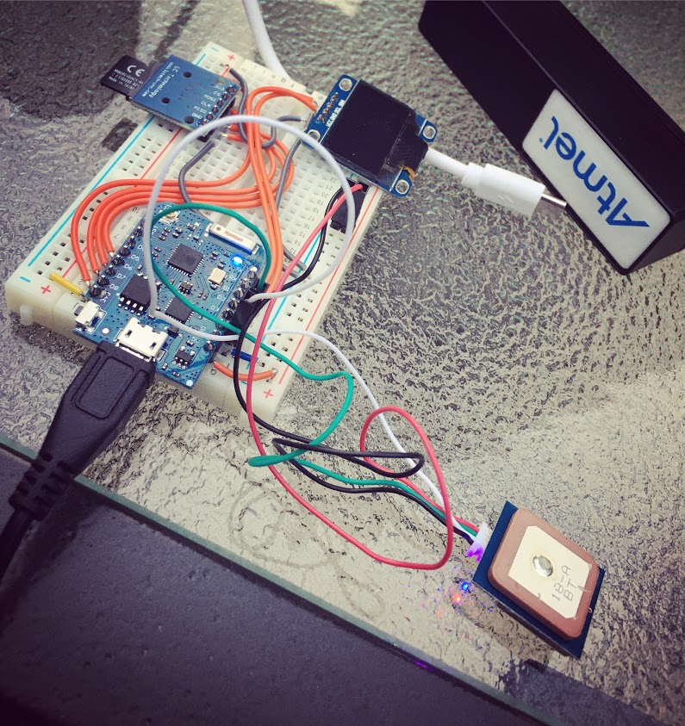
Photos/GPSBreadboardTest.jpg
