MKme/ResQ/Photos/LORA Testing.jpg

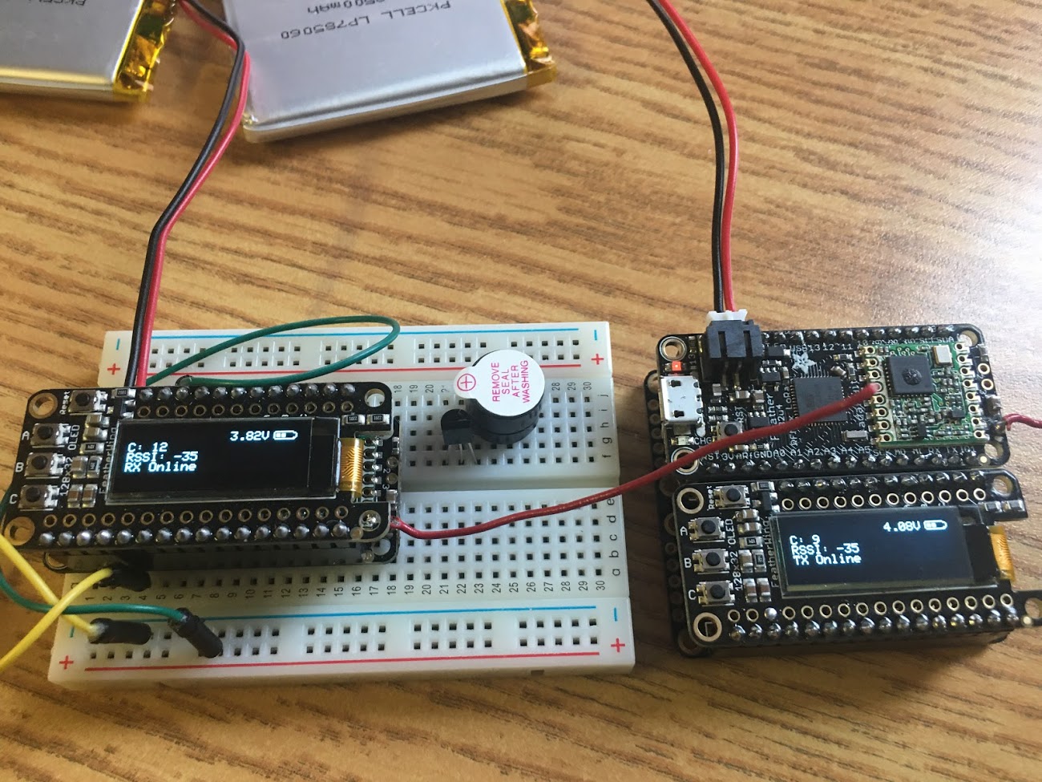
Photos/LORA Testing.jpg
