MKme/ResQ/Photos/MAP Test 2000 MAC Locations .png

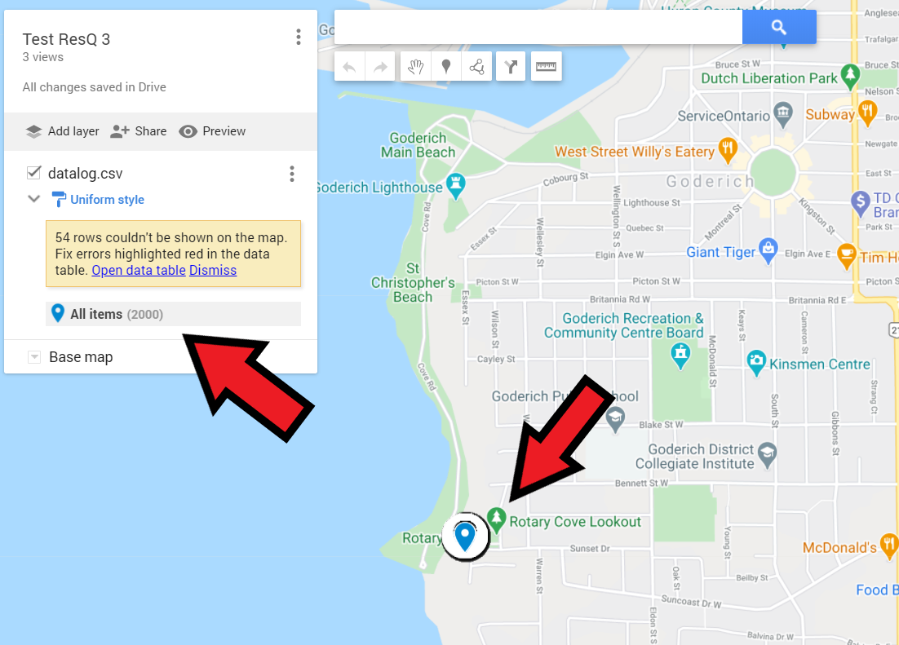
Photos/MAP Test 2000 MAC Locations .png
